BenSeverson/bisque/docs/superpowers/plans/2026-08-11-pcb-rev-b.md

# PCB Rev B Implementation Plan

> **For agentic workers:** REQUIRED SUB-SKILL: Use superpowers:subagent-driven-development (recommended) or superpowers:executing-plans to implement this plan task-by-task. Steps use checkbox (`- [ ]`) syntax for tracking.

**Goal:** Respin the Bisque controller PCB to add a touch interface, a re-mapped GPIO
assignment, an atmosphere purge relay, a second SSR zone, digital CT current sensing, a
second thermocouple input, and MAX31856 front-ends — plus opto-isolated SSR triggers, a
hardware watchdog, TVS protection and test points.

**Architecture:** Everything on the board derives from one table,
`hardware/kicad/generator/design.py` (components, pin→net connectivity, placement). The
schematic and board generators both read it, so they cannot disagree. Work proceeds
subsystem-by-subsystem into that table, each verified by the schematic netlist round-trip,
with a single integration task at the end that places, routes and DRCs the whole board.
Firmware changes are limited to pin symbols and the PSRAM mode — no drivers.

**Tech Stack:** KiCad 10 (`pcbnew` Python API + `kicad-cli`), Python 3 generator scripts,
ESP-IDF 6.0, JLCPCB Economic assembly.

## Global Constraints

- **Spec of record:** `docs/superpowers/specs/2026-08-10-pcb-rev-b-hardware-design.md`.
  Where this plan and the spec disagree, the spec wins — raise it rather than guessing.
- **Branch:** `pcb-rev-b-design` (already exists, already carries the spec).
- **Board:** 2-layer, 100 × 100 mm, `BX0,BY0,BX1,BY1 = 20.0, 20.0, 120.0, 120.0`.
- **Module:** ESP32-S3-WROOM-1U-N16R2, LCSC `C3013945`.
- **No mains anywhere on the PCB.** The ADE7953 voltage channel is DNP and lands on a
  SELV header only.
- **No TVS across thermocouple inputs** — leakage into a ~40 µV/°C source is an accuracy
  error, not protection.
- **All heat/relay outputs must be inactive from power-on through reset**: 10 kΩ pulldown
  on every SSR opto input and every ULN2003 input.
- **KiCad Python is not the system Python.** Board builds need:
  `KPY=/Applications/KiCad/KiCad.app/Contents/Frameworks/Python.framework/Versions/Current/bin/python3`
- **ESP-IDF is never on a bare shell's PATH.** Use `make firmware`, or
  `. ./scripts/idf-env.sh && idf.py ...` in the *same* command.
- **Rev A is a prototype.** No backward compatibility is owed to it by the board. The one
  exception is firmware OTA (spec §4.1), which is out of scope here.
- **Every LCSC part number must be re-verified live before the fab order.** The numbers in
  this plan were checked on 2026-08-10.

### Authoritative pinouts (extracted from KiCad 10 symbol libraries — do not re-derive)

```
MAX31856      Sensor_Temperature:MAX31856      TSSOP-14
  1 AGND   2 BIAS   3 T-     4 T+     5 AVDD   6 DNC    7 ~DRDY
  8 DVDD   9 ~CS   10 SCK   11 SDO   12 SDI   13 ~FAULT 14 DGND

ADE7953xCP    Sensor:ADE7953xCP                LFCSP-28 5x5 + EP
  1 ZX      2 ~RESET  3 VINTD   4 DGND    5 IAP     6 IAN     7 PULL_HIGH
  8 PULL_HIGH  9 IBP 10 IBN    11 VN     12 VP     13 REF    14 PULL_LOW
 15 VINTA  16 AGND   17 VDD    18 CLKIN  19 CLKOUT 20 ~REVP  21 ZX_I
 22 ~IRQ   23 CF1    24 CF2    25 SCLK   26 MISO/SDA/TX      27 MOSI/SCL/RX
 28 ~CS    29 EP

ULN2003A      Transistor_Array:ULN2003A        SOIC-16
  1..7 = I1..I7    8 GND    9 COM    10..16 = O7..O1   (note: O1 is pin 16)

SRV05-4       Power_Protection:SRV05-4         SOT-23-6
  1 IO1    2 VN(GND)   3 IO2    4 IO3    5 VP(VCC)   6 IO4

LTV-817       Isolator:LTV-817                 SO-4
  1 anode  2 cathode   3 emitter  4 collector      (symbol pins are unnamed)
```

### Net naming (use these exactly)

```
TC1_CS TC2_CS TC1_P TC1_N TC2_P TC2_N TC1_BIAS TC2_BIAS
SSR1_CTRL SSR2_CTRL SSR_EN SSR1_A SSR1_B SSR2_A SSR2_B
AUX1 AUX2 AUX3 AUX_VP AUX1_OUT AUX2_OUT AUX3_OUT
IN1_RAW IN1 IN2_RAW IN2 IN3_RAW IN3
I2C_SDA I2C_SCL
CTA_P CTA_N CTA_F CTB_P CTB_N CTB_F ADE_RESET ADE_VINTA ADE_VINTD ADE_REF
ADE_CLKIN ADE_CLKOUT ADE_VP ADE_VN
SSR1_LED_A SSR1_IND_A SSR1_IND_K SSR2_LED_A SSR2_IND_A SSR2_IND_K
T_CLK_R T_CS_R T_DIN_R T_DO_R T_IRQ_R
T_CS T_IRQ
WDT_KICK WDT_PUMP WDT_HOLD
```

`AUX_VP`, `SSR1_A/B`, `SSR2_A/B` and `SSR_EN` are **not** in `POWER_NETS` — `AUX_VP` is an
externally supplied rail the board does not generate, and the SSR nets are isolated.

---

## File Structure

| File | Responsibility | Tasks |
|---|---|---|
| `hardware/kicad/generator/design.py` | Single source of truth: components, pin→net, placement | 1, 3, 5–13 |
| `hardware/kicad/generator/check_pinmap.py` | **New.** Asserts `design.py` U1 pins match Kconfig defaults | 2 |
| `hardware/kicad/generator/check_isolation.py` | **New.** Asserts the opto barrier is unbridged | 7 |
| `hardware/kicad/generator/kicad_build.py` | Board build; gains a GND pour keepout | 7, 14 |
| `hardware/kicad/generator/gen_pcb.py` | Silkscreen header pin labels (`J5_PINS` etc.) | 11 |
| `hardware/kicad/generator/gen_jlc.py` | LCSC table, `HAND_SOLDER`, `JLC_ROTATION` | 1, 15 |
| `hardware/kicad/datasheets/REV-B-NOTES.md` | **New.** Verified answers to the spec's §7.1 risks | 4 |
| `main/Kconfig.projbuild` | Firmware pin defaults (source of truth for firmware) | 3 |
| `components/app_config/include/app_config.h` | `APP_PIN_*` macros | 3 |
| `sdkconfig.defaults` | PSRAM mode | 1 |
| `Makefile` | `pcb` / `pcb-check` targets | 15 |
| `docs/pin-assignments.md`, `docs/application-roadmap-and-pcb-provisions.md`, `hardware/kicad/README.md`, `docs/*.svg` | Documentation | 16 |

**Intermediate states carry dangling nets by design.** Task 3 re-maps U1's pins to nets
whose components do not exist until Tasks 6–13. `python3 generator/design.py` prints
`!! single-pin` for those, which is expected and not a failure until Task 14, where the
count must reach zero.

---

### Task 1: Module swap to WROOM-1U-N16R2

**Files:**
- Modify: `sdkconfig.defaults:11-14`
- Modify: `hardware/kicad/generator/design.py` (U1 entry, module docstring)
- Modify: `hardware/kicad/generator/gen_jlc.py` (LCSC["U1"])

**Interfaces:**
- Consumes: nothing.
- Produces: `U1` uses footprint `RF_Module:ESP32-S3-WROOM-1U`; GPIO 35/36/37 become
  assignable by Task 3.

- [ ] **Step 1: Change the PSRAM mode**

In `sdkconfig.defaults`, replace lines 11–14:

```
# PSRAM (ESP32-S3-WROOM-1U-N16R2: 2MB quad PSRAM)
# Quad, not octal: octal PSRAM consumes GPIO 35/36/37 inside the module, and
# docs/superpowers/specs/2026-08-10-pcb-rev-b-hardware-design.md needs them.
# The only consumer of PSRAM is CONFIG_MBEDTLS_EXTERNAL_MEM_ALLOC below, which
# needs tens of KB for OTA TLS, not megabytes.
CONFIG_SPIRAM=y
CONFIG_SPIRAM_MODE_QUAD=y
CONFIG_SPIRAM_SPEED_80M=y
```

- [ ] **Step 2: Verify the firmware still builds and PSRAM initialises**

```bash
make firmware
```

Expected: build succeeds. Confirm the config actually took:

```bash
grep -E "CONFIG_SPIRAM_MODE_(OCT|QUAD)" sdkconfig
```

Expected: `CONFIG_SPIRAM_MODE_QUAD=y` present, no `_OCT=y`. If `sdkconfig` still shows
OCT, delete `sdkconfig` and re-run `make firmware` — `sdkconfig.defaults` only seeds a
missing `sdkconfig`.

- [ ] **Step 3: Point U1 at the 1U footprint**

In `design.py`, change the `U1` entry's `fp`, `fpf` and `value` (leave `pins` alone —
Task 3 owns those):

```python
    "U1": dict(lib="RF_Module", sym="ESP32-S3-WROOM-1",
               fp="RF_Module:ESP32-S3-WROOM-1U", fpf="ESP32-S3-WROOM-1U.kicad_mod",
               value="ESP32-S3-WROOM-1U-N16R2", at=(70.0, 33.0, 0),
```

Note the symbol stays `ESP32-S3-WROOM-1` — the 1U has no separate symbol and the pin
numbering is identical. Only the footprint (body outline, origin, antenna keep-out)
differs.

- [ ] **Step 4: Update the BOM line**

In `gen_jlc.py`, replace the `U1` entry in `LCSC`:

```python
    "U1": ("C3013945", "ESP32-S3-WROOM-1U-N16R2 (16MB flash, 2MB quad PSRAM, U.FL)", False, True),
```

- [ ] **Step 5: Verify the netlist is unchanged**

```bash
cd hardware/kicad && python3 generator/design.py | tail -5
```

Expected: the same net list as before this task — the footprint swap changes geometry, not
connectivity.

- [ ] **Step 6: Commit**

```bash
git add sdkconfig.defaults hardware/kicad/generator/design.py hardware/kicad/generator/gen_jlc.py
git commit -m "feat(hw): swap to ESP32-S3-WROOM-1U-N16R2

Quad PSRAM frees GPIO 35/36/37; the U.FL connector makes Wi-Fi work in a
metal enclosure and removes the 48x21.7mm antenna keep-out."
```

---

### Task 2: `check_pinmap.py` — the Kconfig/board drift checker

Spec §7 asks for this explicitly: "assert `design.py`'s net-to-module-pin table matches
`main/Kconfig.projbuild` defaults. This has drifted before and is now checked rather than
remembered."

**Files:**
- Create: `hardware/kicad/generator/check_pinmap.py`

**Interfaces:**
- Consumes: `design.COMPONENTS["U1"]["pins"]`, `main/Kconfig.projbuild`.
- Produces: a CLI checker exiting 0 on agreement, 1 on drift. Tasks 3 and 14 run it.

- [ ] **Step 1: Write the checker**

Create `hardware/kicad/generator/check_pinmap.py`:

```python
#!/usr/bin/env python3
"""Assert design.py's U1 pin map agrees with main/Kconfig.projbuild defaults.

The GPIO assignment lives in three files that must agree and have drifted apart
before (see docs/pin-assignments.md). Kconfig is the firmware's source of truth;
design.py is the board's. This checks them against each other so a re-map that
updates one and forgets the other fails loudly instead of reaching a fab house.

Module pin number -> GPIO for ESP32-S3-WROOM-1 / -1U (identical pinout).
"""
import os
import re
import sys

sys.path.insert(0, os.path.dirname(__file__))
from design import COMPONENTS

REPO = os.path.normpath(os.path.join(os.path.dirname(__file__), "..", "..", ".."))
KCONFIG = os.path.join(REPO, "main", "Kconfig.projbuild")

# U1 module pin -> GPIO number. From the ESP32-S3-WROOM-1 datasheet pad list;
# the 1U is identical. Pins carrying power, EN or GND are absent.
# Nets on U1 that are fixed-function and correctly have NO Kconfig pin symbol:
# the native USB peripheral (GPIO 19/20), the UART0 console (GPIO 43/44) and
# the BOOT strapping pin (GPIO 0). These must never count as unmapped.
NO_KCONFIG_SYMBOL = {"USB_DN", "USB_DP", "TXD0", "RXD0", "IO0"}

MODULE_PIN_GPIO = {
    4: 4, 5: 5, 6: 6, 7: 7, 8: 15, 9: 16, 10: 17, 11: 18, 12: 8,
    13: 19, 14: 20, 15: 3, 16: 46, 17: 9, 18: 10, 19: 11, 20: 12,
    21: 13, 22: 14, 23: 21, 24: 47, 25: 48, 26: 45, 27: 0,
    28: 35, 29: 36, 30: 37, 31: 38, 32: 39, 33: 40, 34: 41, 35: 42,
    36: 44, 37: 43, 38: 2, 39: 1,
}

# net name -> Kconfig symbol that must hold that GPIO.
NET_KCONFIG = {
    "SPI_MOSI": "KILN_PIN_SPI_MOSI",
    "SPI_MISO": "KILN_PIN_SPI_MISO",
    "SPI_SCLK": "KILN_PIN_SPI_SCLK",
    "TC1_CS": "KILN_PIN_TC1_CS",
    "TC2_CS": "KILN_PIN_TC2_CS",
    "SSR1_CTRL": "KILN_PIN_SSR1",
    "SSR2_CTRL": "KILN_PIN_SSR2",
    "LCD_CS": "KILN_PIN_LCD_CS",
    "LCD_DC": "KILN_PIN_LCD_DC",
    "LCD_RST": "KILN_PIN_LCD_RST",
    "LCD_BL": "KILN_PIN_LCD_BL",
    "LED_DATA": "KILN_PIN_STATUS_LED",
    "ALARM": "KILN_PIN_ALARM",
    "AUX1": "KILN_PIN_VENT",
    "AUX2": "KILN_PIN_AUX2",
    "AUX3": "KILN_PIN_AUX3",
    "IN1": "KILN_PIN_LID_SWITCH",
    "IN2": "KILN_PIN_IN_GASFLOW",
    "IN3": "KILN_PIN_IN_SPARE",
    "I2C_SDA": "KILN_PIN_I2C_SDA",
    "I2C_SCL": "KILN_PIN_I2C_SCL",
    "T_CS": "KILN_PIN_TOUCH_CS",
    "T_IRQ": "KILN_PIN_TOUCH_IRQ",
    "WDT_KICK": "KILN_PIN_WDT_KICK",
    "BTN_UP": "KILN_PIN_BTN_UP",
    "BTN_DOWN": "KILN_PIN_BTN_DOWN",
    "BTN_LEFT": "KILN_PIN_BTN_LEFT",
    "BTN_RIGHT": "KILN_PIN_BTN_RIGHT",
    "BTN_SEL": "KILN_PIN_BTN_SELECT",
}

def kconfig_defaults(path):
    """{symbol: int default} for every `config X` / `default N` int option."""
    out, sym = {}, None
    for line in open(path):
        m = re.match(r"\s*config\s+(\w+)\s*$", line)
        if m:
            sym = m.group(1)
            continue
        m = re.match(r"\s*default\s+(-?\d+)\s*$", line)
        if m and sym:
            out.setdefault(sym, int(m.group(1)))
    return out

def board_gpios():
    """{net: gpio} for every U1 pin that carries a mapped signal."""
    out = {}
    for pin, net in COMPONENTS["U1"]["pins"].items():
        if net is None:
            continue
        gpio = MODULE_PIN_GPIO.get(int(pin))
        if gpio is not None:
            out[net] = gpio
    return out

def main():
    defaults = kconfig_defaults(KCONFIG)
    board = board_gpios()
    errors = []

    for net, sym in NET_KCONFIG.items():
        on_board = board.get(net)
        in_kconfig = defaults.get(sym)
        if on_board is None:
            errors.append("net %s is in NET_KCONFIG but not on U1 in design.py" % net)
        elif in_kconfig is None:
            errors.append("%s has no integer default in Kconfig.projbuild" % sym)
        elif on_board != in_kconfig:
            errors.append("%s: Kconfig says GPIO %d, design.py wires net %s to GPIO %d"
                          % (sym, in_kconfig, net, on_board))

    unmapped = sorted(set(board) - set(NET_KCONFIG) - NO_KCONFIG_SYMBOL)
    if unmapped:
        errors.append("U1 nets with no Kconfig symbol: %s" % ", ".join(unmapped))

    if errors:
        for e in errors:
            print("FAIL: %s" % e)
        return 1
    print("check_pinmap: %d GPIO assignments agree between Kconfig and design.py"
          % len(NET_KCONFIG))
    return 0

if __name__ == "__main__":
    sys.exit(main())
```

- [ ] **Step 2: Run it and confirm it fails on the current (rev A) state**

```bash
cd hardware/kicad && python3 generator/check_pinmap.py
```

Expected: **exit 1**, with failures naming `TC1_CS`, `SSR1_CTRL`, `AUX2`, `IN1`, and the
symbols that do not exist yet (`KILN_PIN_TC2_CS`, `KILN_PIN_I2C_SDA`, …). This is correct:
the checker encodes the rev B target, and rev B has not been built yet. It proves the
checker can detect drift rather than passing vacuously.

Also confirm it detects real board nets: the `unmapped` line should list rev A's
`TC_CS`, `SSR_CTRL`, `VENT`, `AUX_A`, `AUX_B`, `LID_SW`.

- [ ] **Step 3: Commit**

```bash
git add hardware/kicad/generator/check_pinmap.py
git commit -m "test(hw): add Kconfig/design.py GPIO drift checker

Fails against rev A by design - it encodes the rev B target map. Task 3
brings both files to it."
```

---

### Task 3: GPIO re-map — Kconfig, app_config.h and design.py together

These three must change atomically or `check_pinmap.py` stays red.

**Files:**
- Modify: `main/Kconfig.projbuild`
- Modify: `components/app_config/include/app_config.h`
- Modify: `hardware/kicad/generator/design.py` (U1 `pins` dict only)

**Interfaces:**
- Consumes: `check_pinmap.py` from Task 2.
- Produces: every net in the plan's naming list is wired to U1; Tasks 6–13 attach the
  other end of each.

- [ ] **Step 1: Rewrite U1's pin dict in `design.py`**

```python
               pins={"1": "GND", "2": "+3V3", "3": "EN", "4": "IN1",
                     "5": "T_CS", "6": "T_IRQ", "7": "ALARM",
                     "8": "AUX2", "9": "AUX3", "10": "SSR1_CTRL",
                     "11": "I2C_SDA", "12": "LCD_CS", "13": "USB_DN",
                     "14": "USB_DP", "15": "LCD_BL", "16": "LCD_RST",
                     "17": "LCD_DC", "18": "TC1_CS", "19": "SPI_MOSI",
                     "20": "SPI_SCLK", "21": "SPI_MISO", "22": "AUX1",
                     "23": "SSR2_CTRL", "24": "I2C_SCL", "25": "LED_DATA",
                     "26": None, "27": "IO0", "28": "TC2_CS",
                     "29": "WDT_KICK", "30": None, "31": "BTN_UP",
                     "32": "BTN_DOWN", "33": "BTN_LEFT", "34": "BTN_RIGHT",
                     "35": "BTN_SEL", "36": "RXD0", "37": "TXD0",
                     "38": "IN2", "39": "IN3", "40": "GND",
                     "41": "GND"}),
```

Module pin 30 is GPIO 37 — the spare — and stays `None`.

- [ ] **Step 2: Update Kconfig defaults**

In `main/Kconfig.projbuild`, inside `menu "GPIO Pin Assignments"`:

Rename `KILN_PIN_TC_CS` → `KILN_PIN_TC1_CS` (default stays `10`) and `KILN_PIN_SSR` →
`KILN_PIN_SSR1` (default stays `17`). Change the five button defaults to
`UP=38 DOWN=39 LEFT=40 RIGHT=41 SELECT=42`. Change `KILN_PIN_LID_SWITCH` default `21` →
`4`. Rename `KILN_PIN_AUX_A` → `KILN_PIN_AUX2` (default `-1` → `15`) and `KILN_PIN_AUX_B`
→ `KILN_PIN_AUX3` (default `-1` → `16`).

Then append these new options:

```
        config KILN_PIN_TC2_CS
            int "Thermocouple 2 CS GPIO (-1 = disabled)"
            default 35
            help
                Chip select for the second (load) MAX31856 on the shared SPI
                bus. Populated on the rev B board.

                NOTHING READS THIS PIN YET. The multi-channel thermocouple
                driver is a follow-on; this exists so the board and the
                firmware agree on what is routed.

                Set to -1 on any build with only one thermocouple fitted.

        config KILN_PIN_SSR2
            int "SSR zone 2 output GPIO (-1 = disabled)"
            default 21
            help
                Trigger for the second SSR zone, opto-isolated on the rev B
                board. Driven from the 100 ms SSR window rather than the 1 Hz
                firing tick, because zone 2 modulates simultaneously with
                zone 1.

                NOTHING DRIVES THIS PIN YET. Set to -1 on a single-zone kiln.

        config KILN_PIN_IN_GASFLOW
            int "Gas-flow interlock input GPIO (-1 = disabled)"
            default 2
            help
                Dry-contact input for a gas-flow switch on the atmosphere
                purge line. Same conditioning and fail-safe polarity as the
                lid switch: open contact reads HIGH, so a broken wire reads
                "no flow".

                NOTHING READS THIS PIN YET.

        config KILN_PIN_IN_SPARE
            int "Spare protected input GPIO (-1 = disabled)"
            default 1
            help
                Third dry-contact input, unassigned. Same conditioning as the
                lid and gas-flow inputs.

                NOTHING READS THIS PIN YET.

        config KILN_PIN_I2C_SDA
            int "I2C SDA GPIO (-1 = disabled)"
            default 18
            help
                I2C data. Carries the on-board ADE7953 current-metering IC and
                the Qwiic/STEMMA-QT expansion header.

                NO I2C DRIVER EXISTS YET.

        config KILN_PIN_I2C_SCL
            int "I2C SCL GPIO (-1 = disabled)"
            default 47
            help
                I2C clock. See KILN_PIN_I2C_SDA.

        config KILN_PIN_TOUCH_CS
            int "Touch controller CS GPIO (-1 = disabled)"
            default 5
            help
                Chip select for the XPT2046 resistive touch controller on the
                display module. The controller is on the LCD module, not on
                the Bisque PCB; its clock/data lines are the shared SPI bus.

                NO TOUCH DRIVER EXISTS YET.

        config KILN_PIN_TOUCH_IRQ
            int "Touch pen-down interrupt GPIO (-1 = disabled)"
            default 6
            help
                Pen-down interrupt from the XPT2046. Lets the firmware skip
                touch reads until a press occurs rather than polling.

                Set to -1 to poll instead.

        config KILN_PIN_WDT_KICK
            int "Hardware watchdog kick GPIO (-1 = disabled)"
            default 36
            help
                Square-wave output feeding the charge pump that gates both SSR
                opto channels. If the firmware stops toggling this pin - or
                wedges with it stuck high or stuck low - the pump decays and
                both SSRs de-energize within about a second.

                A charge pump needs TRANSITIONS, which is the whole point: a
                stuck level fails exactly like a stopped one.

                NOTHING TOGGLES THIS PIN YET, so a rev B board runs with the
                WDT DEFEAT solder jumper fitted until the kick task lands. A
                board with neither the jumper nor the kick task will not heat.

                Set to -1 on hardware without the watchdog circuit.
```

- [ ] **Step 3: Update `app_config.h`**

Replace the `MAX31855 Thermocouple`, `SSR Output` and `Optional GPIOs` blocks:

```c
/* --- MAX31856 Thermocouple (2 channels on the shared SPI bus) --- */
#define APP_PIN_TC1_CS CONFIG_KILN_PIN_TC1_CS
#define APP_PIN_TC2_CS CONFIG_KILN_PIN_TC2_CS

/* --- SSR Outputs (opto-isolated, 2 zones) --- */
#define APP_PIN_SSR1 CONFIG_KILN_PIN_SSR1
#define APP_PIN_SSR2 CONFIG_KILN_PIN_SSR2
```

and, in the optional-GPIO block, replace `APP_PIN_AUX_A` / `APP_PIN_AUX_B` and add the
rest:

```c
/* Aux output bank (ULN2003 channels 1-3). Routed and populated on the rev B
   PCB but NOT DRIVEN BY ANY CODE except AUX1, which components/safety/ drives
   as the vent. Roles are firmware policy, not wiring — see
   docs/pin-assignments.md §5. */
#define APP_PIN_AUX2 CONFIG_KILN_PIN_AUX2
#define APP_PIN_AUX3 CONFIG_KILN_PIN_AUX3

/* Protected dry-contact inputs. IN1 is the lid switch (APP_PIN_LID_SWITCH). */
#define APP_PIN_IN_GASFLOW CONFIG_KILN_PIN_IN_GASFLOW
#define APP_PIN_IN_SPARE   CONFIG_KILN_PIN_IN_SPARE

/* I2C bus: on-board ADE7953 current metering + Qwiic expansion header. */
#define APP_PIN_I2C_SDA CONFIG_KILN_PIN_I2C_SDA
#define APP_PIN_I2C_SCL CONFIG_KILN_PIN_I2C_SCL

/* XPT2046 touch controller (on the display module, shared SPI bus). */
#define APP_PIN_TOUCH_CS  CONFIG_KILN_PIN_TOUCH_CS
#define APP_PIN_TOUCH_IRQ CONFIG_KILN_PIN_TOUCH_IRQ

/* Hardware watchdog kick — gates both SSR opto channels. */
#define APP_PIN_WDT_KICK CONFIG_KILN_PIN_WDT_KICK
```

Update the `APP_PIN_TC_CS` / `APP_PIN_SSR` call sites the compiler flags in the next step.

- [ ] **Step 4: Fix the renamed call sites and build**

```bash
grep -rn "APP_PIN_TC_CS\|APP_PIN_SSR\b\|CONFIG_KILN_PIN_TC_CS\|CONFIG_KILN_PIN_SSR\b\|APP_PIN_AUX_A\|APP_PIN_AUX_B" main/ components/ simulator/ tests/
```

Rename each hit to the new symbol (`APP_PIN_TC1_CS`, `APP_PIN_SSR1`, `APP_PIN_AUX2/3`).
Then:

```bash
make firmware && make test-host
```

Expected: both succeed.

- [ ] **Step 5: Run the drift checker — it must now pass**

```bash
cd hardware/kicad && python3 generator/check_pinmap.py
```

Expected: `check_pinmap: 29 GPIO assignments agree between Kconfig and design.py`, exit 0.

- [ ] **Step 6: Regenerate the schematic and confirm the round-trip still passes**

```bash
cd hardware/kicad && python3 generator/gen_sch.py bisque-controller.kicad_sch \
  && python3 generator/check_netlist.py bisque-controller.kicad_sch
```

Expected: `PASS`, 0 mismatches. The single-pin warnings from `design.py` are expected
here (see File Structure).

- [ ] **Step 7: Commit**

```bash
git add main/Kconfig.projbuild components/app_config/include/app_config.h \
        hardware/kicad/generator/design.py hardware/kicad/bisque-controller.kicad_sch \
        main components
git commit -m "feat(hw)!: re-map GPIOs for rev B

Buttons to 38-42 (contiguous module pads), lid to GPIO 4, SSR2 onto 21,
TC2/watchdog onto the pins quad PSRAM freed. check_pinmap.py now passes."
```

---

### Task 4: Retire the spec's pre-layout risks

Spec §7.1 lists six risks that must be answered from datasheets before copper is
committed. Three were already retired during design review (KK-254 1×14 exists; MAX31856
and ADE7953 pinouts are in the Global Constraints above). This task closes the rest.

**Files:**
- Create: `hardware/kicad/datasheets/REV-B-NOTES.md`

**Interfaces:**
- Consumes: nothing.
- Produces: the ADE7953 footprint choice and the confirmed part numbers that Tasks 7–12
  depend on. **Tasks 8, 10 and 12 must not start before this one lands.**

- [ ] **Step 1: Pull the datasheets**

Use the `kicad-happy:datasheets` skill, or fetch directly:

```bash
cd hardware/kicad && python3 ~/.claude/plugins/cache/kicad-happy/kicad-happy/2.1.0/skills/lcsc/scripts/fetch_datasheet_lcsc.py --search "C515890" -o datasheets/ADE7953.pdf
python3 ~/.claude/plugins/cache/kicad-happy/kicad-happy/2.1.0/skills/lcsc/scripts/fetch_datasheet_lcsc.py --search "C2653162" -o datasheets/MAX31856.pdf
python3 ~/.claude/plugins/cache/kicad-happy/kicad-happy/2.1.0/skills/lcsc/scripts/fetch_datasheet_lcsc.py --search "C7512" -o datasheets/ULN2003A.pdf
python3 ~/.claude/plugins/cache/kicad-happy/kicad-happy/2.1.0/skills/lcsc/scripts/fetch_datasheet_lcsc.py --search "C109227" -o datasheets/LTV-817S.pdf
```

- [ ] **Step 2: Answer each question and write it down**

Create `hardware/kicad/datasheets/REV-B-NOTES.md` recording, with a page or table citation
for each:

1. **ADE7953 `IRMS` with the voltage channel unused.** Does the current-channel RMS
   register update independently of the voltage channel? Which registers are invalid
   without it (expect: active/reactive power, power factor, line-cycle accumulation,
   `ZX`)? **If IRMS turns out to require the voltage channel, STOP and escalate** — spec
   §2.2's whole current-only premise fails and the CT section needs redesigning.
2. **ADE7953 exposed-pad size.** KiCad ships no LFCSP-28 footprint (only LFCSP-32).
   Confirm the package's EP dimensions against
   `Package_DFN_QFN:QFN-28-1EP_5x5mm_P0.5mm_EP3.1x3.1mm` and
   `Package_DFN_QFN:VQFN-28-1EP_5x5mm_P0.5mm_EP3.25x3.25mm`, and record which one to use.
   These pads are 0.5 mm pitch — a wrong EP is not something DRC can catch.
3. **ADE7953 interface selection.** How I2C mode is strapped (pins 7/8 `PULL_HIGH`, 14
   `PULL_LOW`, and what `~CS` pin 28 must do), plus the I2C address and any address-select
   pins. Record the required resistor values.
4. **ADE7953 support components.** Required capacitor values on `VINTA` (15), `VINTD` (3),
   `REF` (13), the `CLKIN`/`CLKOUT` crystal load caps, and the `~RESET` (2) arrangement.
5. **MAX31856 `BIAS` pin (2) and split AVDD/DVDD.** The capacitor `BIAS` needs to AGND, and
   whether AVDD (5) and DVDD (8) may share the 3V3 rail (expect yes, with separate
   decoupling). Record the datasheet's recommended thermocouple input filter — series R,
   differential C, common-mode C.
6. **ULN2003 input threshold with a floating driver.** Confirm a 10 kΩ pulldown holds every
   channel off while the ESP32 pin is high-impedance at boot.
7. **LTV-817S-TA1-C footprint match.** Which of `Package_SO:SO-4_4.4x2.3mm_P1.27mm`,
   `SO-4_4.4x3.6mm_P2.54mm`, `SO-4_4.4x3.9mm_P2.54mm`, `SO-4_4.4x4.3mm_P2.54mm` matches
   the LCSC part's drawing. Record CTR at the chosen drive current and the resulting
   guaranteed output current.
8. **Charge-pump Schottky.** Confirm a suitable dual Schottky at LCSC (BAT54S or
   equivalent), its LCSC number, and whether it is Basic. Record `Vf` — the pump must hold
   the AO3400A gate above its worst-case `Vgs(th)` (see Task 12).
9. **U.FL clearance.** Connector height above the module and the pigtail's exit direction,
   so Task 14 can keep the reclaimed antenna band clear of it.

- [ ] **Step 3: Confirm every LCSC part is still in stock**

```bash
cd /tmp && for p in C3013945 C2653162 C515890 C7471632 C7512 C109227 C558418; do
  printf "%-10s " $p
  curl -s "https://jlcsearch.tscircuit.com/api/search?q=$p&limit=1&full=true" \
   | python3 -c "import json,sys;d=json.load(sys.stdin)['components'];print(d[0]['mfr'],d[0]['stock'],d[0]['price']) if d else print('NOT FOUND')"
  sleep 0.4
done
```

Expected: all seven resolve with non-zero stock. Record the figures and the date in
`REV-B-NOTES.md`; note any that have moved since 2026-08-10.

- [ ] **Step 4: Commit**

```bash
git add hardware/kicad/datasheets/
git commit -m "docs(hw): retire the rev B pre-layout datasheet risks

Answers spec 7.1 from the datasheets: ADE7953 current-only IRMS, its
exposed-pad size (KiCad has no LFCSP-28), I2C strapping, MAX31856 BIAS
and split supplies, ULN2003 boot state, opto footprint, pump Schottky."
```

---

### Task 5: Board outline and placement regions

**Files:**
- Modify: `hardware/kicad/generator/design.py` (outline constants, mounting holes,
  `POWER_NETS`, module docstring)

**Interfaces:**
- Consumes: Task 1.
- Produces: `BX0..BY1 = 20,20,120,120`; the region comment block Tasks 6–13 place against.

- [ ] **Step 1: Grow the board and move the mounting holes**

In `design.py`:

```python
# --- board outline (mm, page coords) ---
BX0, BY0, BX1, BY1 = 20.0, 20.0, 120.0, 120.0   # 100 x 100 mm

# Placement regions (docs/.../2026-08-10-pcb-rev-b-hardware-design.md §6.2).
# The quiet analog region holds both thermocouple cold junctions and the CT
# front-end; keep it away from the ULN2003 and the SSR optos.
#   digital   x 20..120  y 20..48   module, USB-C, reclaimed antenna band
#   switching x 20..60   y 50..92   ULN2003, SSR optos, watchdog, buzzer
#   analog    x 92..120  y 50..92   MAX31856 x2, ADE7953, CT front-end
#   headers   x 20..120  y 94..120  LCD / nav / aux / I2C, screw terminals
#   barrier   x 20..60   y 74..92   GND pour keepout across the opto row

# net name -> netclass ("signal" default).
# AUX_VP is an externally supplied coil rail the board does not generate, and
# the SSR_* nets are on the isolated side of the opto barrier — neither may
# join the GND/power pour logic.
POWER_NETS = {"GND", "+5V", "+3V3", "VBUS", "VIN", "VLED"}
```

Move the four mounting holes to a 90 × 90 mm grid: `H1` `(25.5, 25.0)`, `H2`
`(115.5, 25.0)`, `H3` `(25.5, 115.0)`, `H4` `(115.5, 115.0)`.

- [ ] **Step 2: Move the bottom-edge parts down 20 mm**

Everything that was referenced to the old 100 mm bottom edge moves with it. Add 20.0 to
the Y of: `J5` `(31.0, 115.0)`, `J6` `(53.0, 115.0)`, `J7` `(70.5, 115.0)`, `C11`
`(26.5, 110.5)`, `J1` `(96.0, 115.6)`, `R5` `(103.5, 117.9)`, `D2` `(102.5, 106.0)`, `U4`
`(96.0, 102.0)`, `R4` `(91.0, 108.0)`, `LED1` `(75.0, 106.0)`, `R3` `(82.0, 104.35)`,
`D3` `(72.55, 99.5)`, `C10` `(69.0, 101.5)`, `R12` `(87.3, 107.6)`, `R13` `(83.5, 101.5)`,
`C12` `(83.8, 107.6)`, `BZ1` `(38.0, 98.0)`, `D4` `(49.5, 104.0)`, `Q2` `(58.0, 100.0)`,
`R11` `(58.8, 94.0)`, `R8` `(62.0, 97.5)`.

These are initial placements. Task 14 iterates them against DRC — do not treat them as
final.

- [ ] **Step 3: Verify connectivity is untouched**

```bash
cd hardware/kicad && python3 generator/design.py > /tmp/nets-after.txt && wc -l /tmp/nets-after.txt
```

Expected: the same net count as before this task — moving parts changes no connectivity.

- [ ] **Step 4: Commit**

```bash
git add hardware/kicad/generator/design.py
git commit -m "feat(hw): grow rev B board to 100x100mm with placement regions"
```

---

### Task 6: Thermocouple front-ends — 2 × MAX31856

**Files:**
- Modify: `hardware/kicad/generator/design.py`

**Interfaces:**
- Consumes: Task 4's `REV-B-NOTES.md` (BIAS cap value, input filter values), Task 3's
  `TC1_CS` / `TC2_CS` nets.
- Produces: nets `TC1_P TC1_N TC2_P TC2_N TC1_BIAS TC2_BIAS`; designators `U3` (TC1),
  `U5` (TC2), `J3` (TC1 terminal), `J8` (TC2 terminal).

- [ ] **Step 1: Replace U3 and add U5**

Delete the old `U3` (MAX31855) entry and its `C8`/`C9`, and add. Use the filter values
recorded in `REV-B-NOTES.md` — the ones below are the datasheet's typical application and
must be confirmed against it:

```python
    # --- Thermocouple channel 1 (control TC) -----------------------------
    # MAX31856 pinout from Sensor_Temperature:MAX31856. Note AVDD (5) and
    # DVDD (8) are separate supply pins - both 3V3, each decoupled - and BIAS
    # (2) needs its own capacitor to AGND. DRDY (7) and FAULT (13) are left
    # unconnected on purpose: both are readable from registers, and polling
    # them saves four GPIOs the pin budget does not have.
    "U3": dict(lib="Sensor_Temperature", sym="MAX31856",
               fp="Package_SO:TSSOP-14_4.4x5mm_P0.65mm",
               fpf="TSSOP-14_4.4x5mm_P0.65mm.kicad_mod",
               value="MAX31856MUD+", at=(104.0, 56.0, 90),
               pins={"1": "GND", "2": "TC1_BIAS", "3": "TC1_N", "4": "TC1_P",
                     "5": "+3V3", "6": None, "7": None, "8": "+3V3",
                     "9": "TC1_CS", "10": "SPI_SCLK", "11": "SPI_MISO",
                     "12": "SPI_MOSI", "13": None, "14": "GND"}),
    "C8": dict(lib="Device", sym="C", fp=C0805[0], fpf=C0805[1],
               value="100nF", at=(100.0, 53.0, 90),
               pins={"1": "+3V3", "2": "GND"}),
    "C13": dict(lib="Device", sym="C", fp=C0805[0], fpf=C0805[1],
                value="100nF", at=(100.0, 59.0, 90),
                pins={"1": "+3V3", "2": "GND"}),
    "C14": dict(lib="Device", sym="C", fp=C0805[0], fpf=C0805[1],
                value="100nF", at=(108.0, 52.0, 0),
                pins={"1": "TC1_BIAS", "2": "GND"}),
    # Differential + common-mode input filter. No TVS here: a TVS array's
    # leakage into a ~40uV/degC source is an accuracy error, not protection.
    "C9": dict(lib="Device", sym="C", fp=C0805[0], fpf=C0805[1],
               value="10nF", at=(110.0, 56.0, 0),
               pins={"1": "TC1_P", "2": "TC1_N"}),
    "C15": dict(lib="Device", sym="C", fp=C0805[0], fpf=C0805[1],
                value="100pF", at=(110.0, 53.5, 0),
                pins={"1": "TC1_P", "2": "GND"}),
    "C16": dict(lib="Device", sym="C", fp=C0805[0], fpf=C0805[1],
                value="100pF", at=(110.0, 58.5, 0),
                pins={"1": "TC1_N", "2": "GND"}),
    "J3": dict(lib="Connector", sym="Screw_Terminal_01x02",
               fp=TBLOCK[0], fpf=TBLOCK[1], value="TC1_K", at=(116.0, 56.0, 90),
               pins={"1": "TC1_P", "2": "TC1_N"}),
```

- [ ] **Step 2: Add channel 2 as an exact copy**

Repeat the block above as `U5`, `C17`–`C22`, `J8`, substituting `TC2_*` for `TC1_*` and
`TC2_CS` for `TC1_CS`, placed 14 mm south: `U5` at `(104.0, 70.0, 90)`, `C17` `(100.0,
67.0, 90)`, `C18` `(100.0, 73.0, 90)`, `C19` `(108.0, 66.0, 0)`, `C20` `(110.0, 70.0, 0)`,
`C21` `(110.0, 67.5, 0)`, `C22` `(110.0, 72.5, 0)`, `J8` `(116.0, 70.0, 90)`.

Note `TC1_N`/`TC2_N` go to the terminal, **not** to GND — unlike rev A's MAX31855, whose
T− was grounded at the chip. Both MAX31856 channels reference their own differential pair.
Record in the README (Task 16) that **ungrounded-junction probes are required**: both
chips share board ground, so two grounded-junction probes in one chamber form a loop
through the kiln body.

- [ ] **Step 3: Verify**

```bash
cd hardware/kicad && python3 generator/design.py | grep -E "TC1_|TC2_"
```

Expected: `TC1_P`, `TC1_N`, `TC2_P`, `TC2_N`, `TC1_BIAS`, `TC2_BIAS`, `TC1_CS`, `TC2_CS`
each with ≥2 pins and **no** `!! single-pin` marker.

```bash
python3 generator/gen_sch.py bisque-controller.kicad_sch && python3 generator/check_netlist.py bisque-controller.kicad_sch
```

Expected: `PASS`.

- [ ] **Step 4: Commit**

```bash
git add hardware/kicad/generator/design.py hardware/kicad/bisque-controller.kicad_sch
git commit -m "feat(hw): two MAX31856 thermocouple front-ends

Replaces the MAX31855. Separate AVDD/DVDD decoupling and the BIAS cap per
datasheet; DRDY and FAULT left NC and polled from registers to save four
GPIOs. Ungrounded-junction probes now required."
```

---

### Task 7: Opto-isolated SSR channels, the pour keepout, and `check_isolation.py`

**Files:**
- Modify: `hardware/kicad/generator/design.py`
- Modify: `hardware/kicad/generator/kicad_build.py` (`add_zones`)
- Create: `hardware/kicad/generator/check_isolation.py`

**Interfaces:**
- Consumes: Task 4 (`LTV-817S` footprint choice, CTR), Task 3 (`SSR1_CTRL`, `SSR2_CTRL`).
- Produces: net `SSR_EN` — the shared opto-LED cathode node that Task 12's watchdog
  MOSFET gates. **Task 12 depends on this net existing.**

- [ ] **Step 1: Write the isolation checker first**

Create `hardware/kicad/generator/check_isolation.py`:

```python
#!/usr/bin/env python3
"""Assert the SSR opto-isolation barrier is not bridged.

The board pours GND on both layers. An opto buys nothing if the pour runs
underneath it, so kicad_build.py carves a keepout across the opto row and the
isolated nets must touch nothing but their opto and their terminal.

Runs on design.py connectivity alone - no KiCad required.
"""
import os
import sys

sys.path.insert(0, os.path.dirname(__file__))
from design import netlist

# isolated net -> exactly the (ref, pin) endpoints it may have.
ISOLATED = {
    "SSR1_A": {("U8", "4"), ("J4", "1")},
    "SSR1_B": {("U8", "3"), ("J4", "2")},
    "SSR2_A": {("U9", "4"), ("J9", "1")},
    "SSR2_B": {("U9", "3"), ("J9", "2")},
}

# Nets that must never appear on the isolated side.
FORBIDDEN = {"GND", "+3V3", "+5V", "VBUS", "VIN", "VLED", "AUX_VP"}

def main():
    nets = netlist()
    errors = []
    for net, allowed in ISOLATED.items():
        got = set(nets.get(net, []))
        if not got:
            errors.append("isolated net %s does not exist" % net)
        elif got != allowed:
            errors.append("isolated net %s connects to %s; expected exactly %s"
                          % (net, sorted(got), sorted(allowed)))
    isolated_refs = {ref for allowed in ISOLATED.values() for ref, _ in allowed}
    for bad in FORBIDDEN:
        for ref, pin in nets.get(bad, []):
            if ref in isolated_refs and (ref, pin) not in \
                    {e for a in ISOLATED.values() for e in a}:
                errors.append("%s.%s is on %s but %s straddles the barrier"
                              % (ref, pin, bad, ref))
    if errors:
        for e in errors:
            print("FAIL: %s" % e)
        return 1
    print("check_isolation: %d isolated nets, barrier intact" % len(ISOLATED))
    return 0

if __name__ == "__main__":
    sys.exit(main())
```

- [ ] **Step 2: Run it and confirm it fails**

```bash
cd hardware/kicad && python3 generator/check_isolation.py
```

Expected: **exit 1**, "isolated net SSR1_A does not exist" ×4. The optos do not exist yet.

- [ ] **Step 3: Replace the discrete SSR driver with two opto channels**

Delete rev A's `R6`, `R7`, `Q1`, `LED3`, `R10` and re-point `J4`. Add:

```python
    # --- SSR channel 1 (opto-isolated) -----------------------------------
    # GPIO -> R -> opto LED -> SSR_EN, with the indicator LED as a parallel
    # branch off the same GPIO. The indicator cannot sit in SERIES with the
    # opto LED: ~2.0V (indicator) + ~1.2V (opto) leaves nothing to drop from a
    # 3.3V GPIO. Both cathodes land on SSR_EN so the watchdog (Task 12) gates
    # the indicator too - an LED that lights while the SSR is cut would lie.
    # R7/R14 hold the LEDs dark through boot and reset.
    "U8": dict(lib="Isolator", sym="LTV-817",
               fp="Package_SO:SO-4_4.4x4.3mm_P2.54mm",
               fpf="SO-4_4.4x4.3mm_P2.54mm.kicad_mod",
               value="LTV-817S", at=(30.0, 78.0, 0),
               pins={"1": "SSR1_LED_A", "2": "SSR_EN",
                     "3": "SSR1_B", "4": "SSR1_A"}),
    "R6": dict(lib="Device", sym="R", fp=R0805[0], fpf=R0805[1],
               value="220R", at=(36.0, 78.0, 180),
               pins={"1": "SSR1_CTRL", "2": "SSR1_LED_A"}),
    "R7": dict(lib="Device", sym="R", fp=R0805[0], fpf=R0805[1],
               value="10k", at=(40.0, 76.0, 90),
               pins={"1": "SSR1_CTRL", "2": "GND"}),
    "LED3": dict(lib="Device", sym="LED", fp=LED0805[0], fpf=LED0805[1],
                 value="amber", at=(24.5, 74.0, 270),
                 pins={"1": "SSR1_IND_K", "2": "SSR1_IND_A"}),
    "R10": dict(lib="Device", sym="R", fp=R0805[0], fpf=R0805[1],
                value="680R", at=(28.0, 74.0, 90),
                pins={"1": "SSR1_CTRL", "2": "SSR1_IND_A"}),
    "R15": dict(lib="Device", sym="R", fp=R0805[0], fpf=R0805[1],
                value="0R", at=(24.5, 71.0, 0),
                pins={"1": "SSR1_IND_K", "2": "SSR_EN"}),
    "J4": dict(lib="Connector", sym="Screw_Terminal_01x02",
               fp=TBLOCK[0], fpf=TBLOCK[1], value="SSR1", at=(22.5, 82.0, 270),
               pins={"1": "SSR1_A", "2": "SSR1_B"}),
```

Repeat as channel 2 — `U9`, `R16` (220R), `R17` (10k), `LED4` (amber), `R18` (680R),
`R19` (0R), `J9` — substituting `SSR2_*`, placed 8 mm south: `U9` `(30.0, 86.0, 0)`,
`R16` `(36.0, 86.0, 180)`, `R17` `(40.0, 84.0, 90)`, `LED4` `(24.5, 90.0, 270)`, `R18`
`(28.0, 90.0, 90)`, `R19` `(24.5, 93.0, 0)`, `J9` `(22.5, 90.0, 270)`.

The 220 Ω series value assumes ~10 mA into the LED from 3.3 V; confirm against the CTR
recorded in `REV-B-NOTES.md` that the resulting collector current clears the SSR input's
requirement.

- [ ] **Step 4: Carve the GND keepout in `kicad_build.py`**

In `add_zones()`, after the two GND zones are added, append a rule area over the barrier
band. `_gnd_islands()` already skips `z.GetIsRuleArea()`, so the healing logic ignores it:

```python
    # Opto-isolation barrier: no GND copper on either layer across the SSR
    # opto row, or the pour shorts around the barrier the optos exist to make.
    # A rule area (not a zone) - _gnd_islands() skips these by design.
    ka = pcbnew.ZONE(board)
    ka.SetIsRuleArea(True)
    ka.SetDoNotAllowZoneFills(True)
    ka.SetDoNotAllowTracks(False)
    ka.SetDoNotAllowVias(True)
    ka.SetLayerSet(pcbnew.LSET(
        [pcbnew.F_Cu, pcbnew.B_Cu]))
    ol = ka.Outline()
    ol.NewOutline()
    for (x, y) in [(20.5, 70.0), (34.0, 70.0), (34.0, 96.0), (20.5, 96.0)]:
        ol.Append(MM(x), MM(y))
    board.Add(ka)
```

- [ ] **Step 5: Verify both checkers**

```bash
cd hardware/kicad && python3 generator/check_isolation.py
```

Expected: `check_isolation: 4 isolated nets, barrier intact`, exit 0.

```bash
python3 generator/gen_sch.py bisque-controller.kicad_sch && python3 generator/check_netlist.py bisque-controller.kicad_sch
```

Expected: `PASS`.

- [ ] **Step 6: Commit**

```bash
git add hardware/kicad/generator/design.py hardware/kicad/generator/kicad_build.py \
        hardware/kicad/generator/check_isolation.py hardware/kicad/bisque-controller.kicad_sch
git commit -m "feat(hw): opto-isolate both SSR channels

LTV-817S per channel, indicator LED as a parallel branch (series would not
fit under 3.3V). Both cathodes on SSR_EN so the watchdog gates the
indicator too. GND pour keepout across the barrier, checked by
check_isolation.py."
```

---

### Task 8: Aux output bank — ULN2003 with an external coil rail

**Files:**
- Modify: `hardware/kicad/generator/design.py`

**Interfaces:**
- Consumes: Task 4 (ULN2003 boot behaviour), Task 3 (`AUX1`, `AUX2`, `AUX3`).
- Produces: `AUX_VP`, `AUX1_OUT`, `AUX2_OUT`, `AUX3_OUT`; designator `U6`, terminal `J10`.

- [ ] **Step 1: Add the bank**

```python
    # --- Aux output bank (vent / purge / spare) --------------------------
    # ULN2003A: 7 Darlington channels with integrated freewheel diodes to COM,
    # and a JLCPCB *Basic* part - so it replaces ~19 discrete parts at zero
    # feeder fee. Pin order is I1..I7 = 1..7, GND = 8, COM = 9, O7..O1 = 10..16
    # (note O1 is pin 16, so the outputs run backwards).
    #
    # COM goes to AUX_VP, its own screw terminal, NOT the board's +5V: a gas
    # purge solenoid is realistically 12V or 24V DC and the ULN is rated 50V /
    # 500mA per channel. A solder link (SJ1) ties AUX_VP to +5V for plain 5V
    # relays. The buzzer deliberately keeps its discrete driver so a 5V buzzer
    # and a 24V solenoid never share a COM rail.
    #
    # R20-R22 hold the inputs low while the ESP32 pins are high-impedance at
    # boot - a floating Darlington input must not energize a solenoid.
    "U6": dict(lib="Transistor_Array", sym="ULN2003A",
               fp="Package_SO:SOIC-16_3.9x9.9mm_P1.27mm",
               fpf="SOIC-16_3.9x9.9mm_P1.27mm.kicad_mod",
               value="ULN2003A", at=(44.0, 60.0, 0),
               pins={"1": "AUX1", "2": "AUX2", "3": "AUX3",
                     "4": None, "5": None, "6": None, "7": None,
                     "8": "GND", "9": "AUX_VP",
                     "10": None, "11": None, "12": None, "13": None,
                     "14": "AUX3_OUT", "15": "AUX2_OUT", "16": "AUX1_OUT"}),
    "R20": dict(lib="Device", sym="R", fp=R0805[0], fpf=R0805[1],
                value="10k", at=(38.0, 56.0, 90),
                pins={"1": "AUX1", "2": "GND"}),
    "R21": dict(lib="Device", sym="R", fp=R0805[0], fpf=R0805[1],
                value="10k", at=(38.0, 59.0, 90),
                pins={"1": "AUX2", "2": "GND"}),
    "R22": dict(lib="Device", sym="R", fp=R0805[0], fpf=R0805[1],
                value="10k", at=(38.0, 62.0, 90),
                pins={"1": "AUX3", "2": "GND"}),
    # 4-position terminal: coil rail + three switched low sides.
    "J10": dict(lib="Connector", sym="Screw_Terminal_01x04",
                fp="TerminalBlock_Phoenix:TerminalBlock_Phoenix_MKDS-1,5-4-5.08_1x04_P5.08mm_Horizontal",
                fpf="TerminalBlock_Phoenix_MKDS-1,5-4-5.08_1x04_P5.08mm_Horizontal.kicad_mod",
                value="AUX", at=(22.5, 60.0, 270),
                pins={"1": "AUX_VP", "2": "AUX1_OUT",
                      "3": "AUX2_OUT", "4": "AUX3_OUT"}),
    # Solder link: AUX_VP <- +5V for 5V relay coils. Open by default.
    "SJ1": dict(lib="Jumper", sym="SolderJumper_2_Open",
                fp="Jumper:SolderJumper-2_P1.3mm_Open_RoundedPad1.0x1.5mm",
                fpf="SolderJumper-2_P1.3mm_Open_RoundedPad1.0x1.5mm.kicad_mod",
                value="AUX_VP=5V", at=(30.0, 55.0, 0),
                pins={"1": "+5V", "2": "AUX_VP"}),
```

- [ ] **Step 2: Verify**

```bash
cd hardware/kicad && python3 generator/design.py | grep -E "AUX"
```

Expected: `AUX1 AUX2 AUX3 AUX1_OUT AUX2_OUT AUX3_OUT AUX_VP` all with ≥2 pins, no
`!! single-pin`.

```bash
python3 generator/gen_sch.py bisque-controller.kicad_sch && python3 generator/check_netlist.py bisque-controller.kicad_sch
```

Expected: `PASS`.

- [ ] **Step 3: Commit**

```bash
git add hardware/kicad/generator/design.py hardware/kicad/bisque-controller.kicad_sch
git commit -m "feat(hw): ULN2003 aux bank with external coil rail

Vent, purge and spare on one Basic part with integrated flyback diodes.
COM lands on its own AUX_VP terminal so 12/24V solenoids work; SJ1 links
it to +5V for 5V relays."
```

---

### Task 9: Protected inputs ×3 and TVS

**Files:**
- Modify: `hardware/kicad/generator/design.py`

**Interfaces:**
- Consumes: Task 3 (`IN1`, `IN2`, `IN3`).
- Produces: `IN1_RAW`, `IN2_RAW`, `IN3_RAW`; terminal `J11`, TVS `D5`.

- [ ] **Step 1: Generalise rev A's lid conditioning to three channels**

Rev A's `R12`/`R13`/`C12` become input 1. Re-point them from `LID_IN`/`LID_SW` to
`IN1_RAW`/`IN1`, then add two more copies plus the TVS and terminal:

```python
    # --- Protected dry-contact inputs (lid / gas flow / spare) -----------
    # Rev A's proven conditioning, three times over: 1k series, 10k pull-up to
    # +3V3, 100nF to GND. Open contact reads HIGH, so a broken wire, a pulled
    # connector or a failed-open switch all read "open" and fail safe.
    # Wire a dry contact between the channel and J11.4 (GND).
    "R12": dict(lib="Device", sym="R", fp=R0805[0], fpf=R0805[1],
                value="1k", at=(96.0, 100.0, 180),
                pins={"1": "IN1_RAW", "2": "IN1"}),
    "R13": dict(lib="Device", sym="R", fp=R0805[0], fpf=R0805[1],
                value="10k", at=(92.0, 97.0, 0),
                pins={"1": "+3V3", "2": "IN1"}),
    "C12": dict(lib="Device", sym="C", fp=C0805[0], fpf=C0805[1],
                value="100nF", at=(92.0, 100.0, 0),
                pins={"1": "IN1", "2": "GND"}),
    "R23": dict(lib="Device", sym="R", fp=R0805[0], fpf=R0805[1],
                value="1k", at=(96.0, 104.0, 180),
                pins={"1": "IN2_RAW", "2": "IN2"}),
    "R24": dict(lib="Device", sym="R", fp=R0805[0], fpf=R0805[1],
                value="10k", at=(92.0, 103.0, 0),
                pins={"1": "+3V3", "2": "IN2"}),
    "C23": dict(lib="Device", sym="C", fp=C0805[0], fpf=C0805[1],
                value="100nF", at=(92.0, 106.0, 0),
                pins={"1": "IN2", "2": "GND"}),
    "R25": dict(lib="Device", sym="R", fp=R0805[0], fpf=R0805[1],
                value="1k", at=(96.0, 108.0, 180),
                pins={"1": "IN3_RAW", "2": "IN3"}),
    "R26": dict(lib="Device", sym="R", fp=R0805[0], fpf=R0805[1],
                value="10k", at=(92.0, 109.0, 0),
                pins={"1": "+3V3", "2": "IN3"}),
    "C24": dict(lib="Device", sym="C", fp=C0805[0], fpf=C0805[1],
                value="100nF", at=(92.0, 112.0, 0),
                pins={"1": "IN3", "2": "GND"}),
    # SRV05-4: 1 IO1, 2 VN(GND), 3 IO2, 4 IO3, 5 VP(+3V3), 6 IO4.
    # Rev A skipped a TVS because one feeder fee for a single input was not
    # worth it; rev B takes the externally exposed net count from two to ~ten,
    # so one array covers the board. IO4 is spare.
    "D5": dict(lib="Power_Protection", sym="SRV05-4",
               fp="Package_TO_SOT_SMD:SOT-23-6", fpf="SOT-23-6.kicad_mod",
               value="SRV05-4", at=(101.0, 104.0, 0),
               pins={"1": "IN1_RAW", "2": "GND", "3": "IN2_RAW",
                     "4": "IN3_RAW", "5": "+3V3", "6": None}),
    "J11": dict(lib="Connector", sym="Screw_Terminal_01x04",
                fp="TerminalBlock_Phoenix:TerminalBlock_Phoenix_MKDS-1,5-4-5.08_1x04_P5.08mm_Horizontal",
                fpf="TerminalBlock_Phoenix_MKDS-1,5-4-5.08_1x04_P5.08mm_Horizontal.kicad_mod",
                value="INPUTS", at=(112.0, 104.0, 90),
                pins={"1": "IN1_RAW", "2": "IN2_RAW",
                      "3": "IN3_RAW", "4": "GND"}),
```

- [ ] **Step 2: Remove the lid signal from J7**

J7 pin 6 carried `LID_IN` in rev A. The lid now lands on `J11`, so change J7 pin 6 to
`None` (Task 11 re-purposes the freed header pins).

- [ ] **Step 3: Verify**

```bash
cd hardware/kicad && python3 generator/design.py | grep -E "IN[123]"
```

Expected: `IN1 IN1_RAW IN2 IN2_RAW IN3 IN3_RAW` all with ≥2 pins, no `!! single-pin`, and
no remaining `LID_IN` or `LID_SW` net.

```bash
python3 generator/gen_sch.py bisque-controller.kicad_sch && python3 generator/check_netlist.py bisque-controller.kicad_sch
```

Expected: `PASS`.

- [ ] **Step 4: Commit**

```bash
git add hardware/kicad/generator/design.py hardware/kicad/bisque-controller.kicad_sch
git commit -m "feat(hw): three protected dry-contact inputs with TVS

Lid, gas-flow interlock and a spare, all on rev A's proven RC conditioning
and one SRV05-4 array. Lid moves off J7 onto its own terminal."
```

---
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
