BenSeverson/bisque/docs/superpowers/plans/2026-08-15-rev-a-freeze-and-rev-b-transition.md

# Rev A Freeze and Rev B Transition — Implementation Plan

> **For agentic workers:** REQUIRED SUB-SKILL: Use superpowers:subagent-driven-development (recommended) or superpowers:executing-plans to implement this plan task-by-task. Steps use checkbox (`- [ ]`) syntax for tracking.

**Goal:** Freeze the rev A perfboard firmware behind a verified tag and a `v1` branch, hand `main` to rev B, and correct every document that the handover makes false.

**Architecture:** Rev A is preserved as a published GitHub release, not a maintained line — no board profile, no CI matrix, no OTA changes. `main` becomes rev B only. The documentation debt is then paid in one follow-up PR so `main` is not left internally inconsistent.

**Tech Stack:** git/GitHub Actions (`release.yml` triggers on `v*`, `build.yml` on `main` + PRs to `main`), ESP-IDF, `make test` / `make lint` / `make pcb-check`.

**Spec:** [`docs/superpowers/specs/2026-08-15-rev-a-freeze-and-rev-b-firmware-design.md`](../specs/2026-08-15-rev-a-freeze-and-rev-b-firmware-design.md)

## Global Constraints

- **Task 1 is a human gate.** It requires physical hardware — flashing the perfboard and firing a real profile end to end. An agent cannot complete it and must not mark it done.
- The freeze tag must be an **annotated** tag matching `v*` and must be an **ancestor of `main`**. `v1.0.0` is not (`git merge-base --is-ancestor v1.0.0 main` is false, `git describe --tags main` fails), which is why `scripts/version.sh` currently prints a bare hash.
- **Never create a tag named `v1`.** `refs/heads/v1` and `refs/tags/v1` would both answer to `v1`. Tags on that line stay fully qualified: `v1.1.0`, `v1.1.1`.
- **Do not push any new `v*` tag after Task 1** until the PCBs arrive. An untagged `main` is the mechanism that keeps the frozen perfboard from being offered a rev B image.
- After editing any firmware C/H file, run `clang-format -i` on it. CI's `clang-format` job fails on unformatted code.
- Commit messages end with `Co-Authored-By: Claude Opus 5 <noreply@anthropic.com>`.

## File Structure

| File | Task | Responsibility after this plan |
|---|---|---|
| `docs/heat-treating-extension-plan.md` | 3 | Phase-3 TC plan, corrected to a driver *replacement* |
| `components/app_config/include/app_config.h` | 4 | `APP_PID_KD_DEFAULT` rationale, no longer citing MAX31855 quantization as settled |
| `components/pid_control/pid_control.c` | 4 | Same rationale in the derivative-filter comment |
| `tests/host/stubs/safety_host.c` | 4 | Lid-switch default comment, GPIO 21 → 4 |
| `docs/perfboard-layout.svg` | 5 | Marked historical (rev A) |
| `docs/wiring-diagram.svg` | 5 | Marked historical (rev A) |
| `README.md` | 5 | Perfboard BOM/wiring marked rev A; MAX31855 → MAX31856 in the component tree |
| `CLAUDE.md` | 5 | Hardware Diagrams section and component tree point at rev B |

---

### Task 1: Verify and freeze rev A

**HUMAN GATE — requires the physical perfboard kiln. Do not mark complete without a real firing.**

**Files:** none modified. Produces a tag, a branch, and a GitHub release.

**Interfaces:**
- Produces: the annotated tag `v1.1.0` and the branch `v1`, both consumed by Task 2's ordering constraint (rev B must not reach `main` before the freeze exists).

- [ ] **Step 1: Confirm you are freezing rev A, not rev B**

```bash
git switch main
git log --oneline -1
grep -A1 'config KILN_PIN_BTN_UP' main/Kconfig.projbuild
```

Expected: `KILN_PIN_BTN_UP` defaults to `4` (the rev A perfboard map). If it defaults to `38`, you are on the rev B branch — stop, switch to `main`.

- [ ] **Step 2: Build the freeze candidate**

```bash
./build.sh
```

Expected: `=== Build Complete ===`. This builds the web UI and firmware together; the frozen image must include the SPIFFS web bundle.

- [ ] **Step 3: Flash the perfboard**

```bash
. ./scripts/idf-env.sh && idf.py flash monitor
```

Expected: the kiln boots to the splash and then the dashboard, the 5-way nav switch moves focus, and a temperature reads.

- [ ] **Step 4: Fire a real profile end to end**

Load `docs/smoke-test-profile.json` (or a real bisque profile) and run it to completion on the actual kiln. Follow `docs/bench-smoke-test.md`.

Expected: the firing starts, ramps, holds, and completes; the SSR cycles; history records the run. **This is the step that makes the tag a proven recovery point.** If anything fails, fix it on `main` and restart from Step 2.

- [ ] **Step 5: Tag the verified commit**

```bash
git tag -a v1.1.0 -m "Rev A perfboard — final firmware

Verified on the perfboard kiln with a complete firing before tagging.
Rev A is frozen here: main moves to rev B hardware after this tag.
Recovery image for the perfboard; see docs/superpowers/specs/2026-08-15-rev-a-freeze-and-rev-b-firmware-design.md"
git push origin v1.1.0
```

- [ ] **Step 6: Verify the tag actually describes `main`**

```bash
git merge-base --is-ancestor v1.1.0 main && echo OK-ancestor
git describe --tags main
./scripts/version.sh
```

Expected: `OK-ancestor`, then `v1.1.0` from both commands (not a bare hash). If `describe` still fails, the tag is on the wrong commit — delete and redo it before going further.

- [ ] **Step 7: Create the `v1` branch**

```bash
git branch v1 v1.1.0
git push -u origin v1
```

Do not protect it, do not open PRs against it, do not add it to any workflow trigger.

- [ ] **Step 8: Archive the release artifacts**
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
