BenSeverson/bisque/docs/screenshots/lcd-autotune.png

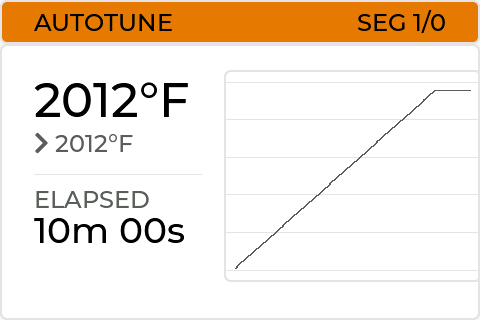
docs/screenshots/lcd-autotune.png
