BenSeverson/bisque/docs/screenshots/lcd-modal-stop-confirm.png

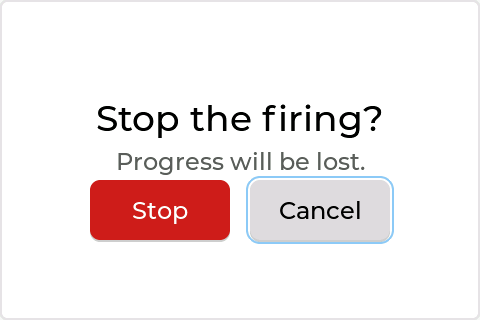
docs/screenshots/lcd-modal-stop-confirm.png
