BenSeverson/bisque/components/safety/include/lid_state.h

#pragma once

/**
 * State of the lid/door interlock switch, as reported to the UIs.
 *
 * Deliberately standalone — no esp_err.h, no FreeRTOS — so the three consumers
 * can share one type without dragging the safety driver's dependencies along:
 * the pure JSON builders in web_server/api_json.c (host-buildable by contract),
 * the LVGL dashboard (which the SDL simulator compiles with no ESP-IDF at all),
 * and safety.c itself.
 *
 * NOT_FITTED is a distinct state rather than a "closed": a kiln with no switch
 * would otherwise show an indicator permanently reading "lid closed", reporting
 * on hardware that isn't there. Consumers omit the reading entirely in that
 * case.
 *
 * Note that CONFIG_KILN_PIN_LID_SWITCH now defaults to GPIO 4 to match the
 * PCB (J11 pin 1, the rev B protected-input terminal), so NOT_FITTED only
 * appears on builds that explicitly set it back to -1.
 * A build with no switch fitted must do that, or jumper the input to GND —
 * otherwise the pulled-up pin reads OPEN and the interlock holds the SSR off.
 */
typedef enum {
    LID_STATE_NOT_FITTED = -1,
    LID_STATE_CLOSED = 0,
    LID_STATE_OPEN = 1,
} lid_state_t;
