BenSeverson/bisque/hardware/kicad/generator/kicad_build.py

"""Build bisque-controller.kicad_pcb through KiCad's own engine (pcbnew API).

Loads the real system-library footprints, places them per design.py,
routes with router.py (obstacle model taken from the *loaded* pad
geometry, so it always matches the libraries actually used), then lets
KiCad do the rest: `kicad-cli pcb drc --refill-zones` fills the ground
pours and runs KiCad's real DRC. The saved board is a genuine
pcbnew-written file. Requires KiCad 10+.

Usage: python3 kicad_build.py [--no-route] <out.kicad_pcb>

`--no-route` is the fast path. Routing 93 nets across 141 parts is ~91%
of the 158 s a full build costs, and several classes of change cannot
touch copper at all: silkscreen placement (silk.py), 3D model offsets
(MODEL_FIXUP), the title block, reference-designator text metrics. With
`--no-route` the tracks, vias and filled zones are read back off the
existing board and everything else is re-derived by the same code a full
build runs, so the result is byte-identical for the same design.py -
`check_fast_path.py` proves that rather than assuming it. Anything that
moves a part, changes connectivity, or changes a routing parameter needs
the full path; `verify_reusable()` below refuses the fast one when
design.py and the loaded board have drifted apart.
"""
import math
import os
import shutil
import subprocess
import sys
import tempfile

sys.path.insert(0, os.path.dirname(__file__))
try:
    # macOS: pcbnew's settings manager needs a live wx app in standalone use
    import wx
    _wx_app = wx.App(False)
    if hasattr(wx, "DisableAsserts"):
        wx.DisableAsserts()
except ImportError:
    pass
import pcbnew
from canonicalize import canonicalize_file
from design import COMPONENTS, netlist, BX0, BY0, BX1, BY1
from project_sync import sync_project
import router as R
import silk
import stages
from gen_jlc import DNP, NOT_ASSEMBLED
from gen_pcb import (all_seeds, route_all, ripup_retry, promoted_order, plane_vias,
                     apply_stackup, SILK, SILK_GRAPHICS, MANUAL_VIAS,
                     EP_VIA_GRID, STITCH_VIAS, is_ep_pad, TP_LABEL_TEXTS, LEGEND_OWNER,
                     TP_LEGEND_OK,
                     PLANE_LAYER, HIDE_REFS, STRIP_FP_SILK, sync_netclasses,
                     netclass_table,
                     USB_KEEPOUT_MARGIN, USB_DIFF_PAIR, route_usb_pair,
                     U2_POUR, COPPER_LAYER_TYPE, FID_KEEPOUT)

# Copper stack-up. Rev B is 4-layer (spec 6.1): signals on the outside, an
# unbroken GND plane on In1.Cu and the +3V3 plane on In2.Cu. router.py still
# knows only two routing layers - 0 and 1 - and they map to F.Cu and B.Cu; the
# inner layers carry no tracks at all, only the plane fills, so the router
# never needs to model them. Vias stay through-hole, which is what lets a pad
# reach either plane with a single hole.
COPPER_LAYERS = 4
LAYER = {0: pcbnew.F_Cu, 1: pcbnew.B_Cu}
PLANE_CU = {"In1.Cu": pcbnew.In1_Cu, "In2.Cu": pcbnew.In2_Cu}


def _find_fp_base():
    cand = [os.environ.get("KICAD_FOOTPRINT_DIR", "")]
    cand += ["/usr/share/kicad/footprints",
             "/usr/local/share/kicad/footprints",
             "/Applications/KiCad/KiCad.app/Contents/SharedSupport/footprints",
             r"C:\Program Files\KiCad\10.0\share\kicad\footprints"]
    import glob as _g
    cand += sorted(_g.glob("/usr/share/kicad*/footprints"), reverse=True)
    for c in cand:
        if c and os.path.isdir(c):
            return c
    sys.exit("KiCad footprint libraries not found - set KICAD_FOOTPRINT_DIR")


import glob
FPBASE = _find_fp_base()


MM = pcbnew.FromMM

# Minimum silkscreen stroke, mm. JLCPCB quotes 0.153 mm as the floor below
# which a legend line may print blurred or drop out entirely. 0.16 rather than
# KiCad's 0.15 house value on purpose: 0.15 is 2.4 um UNDER the quoted number,
# which is finer than a screen resolves and would almost certainly print, but
# "under the published figure by less than anyone can measure" is a sentence
# nobody should have to reconstruct while reading a DFM report. 0.16 is over
# it, and it was free - the placer seats all 204 labels with 0 silk-on-silk at
# either value, so there was no trade to make.
#
# Both silk TEXT sites clamp here, and so - since JLC's DFM report on the
# 2026-10-04 package - do footprint OUTLINES (`widen_fp_silk`). They arrive at
# 0.12 mm from KiCad's stock libraries and used to be left there on the
# argument that nobody reads a part outline during assembly. Two things broke
# that: JLC's DFM flags every one of them under its line-width floor, and some
# outlines ARE read - C46's chamfered outline and `+` are the board's only
# printed polarity mark on a 100 uF electrolytic, and LED1's corner and U1's
# pin-1 marker orient parts by eye. The cost the old note feared is real but
# small: the placer's outline obstacles grow by 0.02 mm a side. It is done at
# build time, as STRIP_FP_SILK is, so no .kicad_mod is edited.
SILK_MIN_STROKE = 0.16

_major = int(pcbnew.Version().split(".")[0])
if _major < 10:
    sys.exit("kicad_build.py requires KiCad 10+ (found %s)" % pcbnew.Version())

# The footprint reader, resolved once. Belt-and-braces against the swig
# type-table corruption `strip_derived()` documents: while a live pcbnew
# session is in that state, PCB_IO_MGR.FindPlugin() is one of the calls that
# hands back an untyped pointer - here, one with no FootprintLoad on it. A
# handle taken before any board is loaded keeps working.
_FP_PLUGIN = pcbnew.PCB_IO_MGR.FindPlugin(pcbnew.PCB_IO_MGR.KICAD_SEXP)


def load_footprint(lib, name):
    path = os.path.join(FPBASE, lib + ".pretty")
    return _FP_PLUGIN.FootprintLoad(path, name)


def V(x, y):
    return pcbnew.VECTOR2I(MM(x), MM(y))


# 3D models. Cosmetic only - no fab output (gerbers, drill, BOM, CPL, DRC)
# touches a model at all - but the renders in 3d/ are how placement and silk
# get eyeballed without a board in hand, so a part that renders as bare pads
# or floats off its footprint costs real time to diagnose.
#
# Five footprints need help. KiCad 10 ships NO model for four of them, and its
# failure mode is silence: `kicad-cli pcb render` exits 0, prints "Loading 3D
# models...", and omits the part. That is why every model this board depends on
# is vendored into 3dmodels/ and referenced through ${KIPRJMOD} rather than
# ${KICAD10_3DMODEL_DIR} - the system path is not reproducible (a KiCad upgrade
# wipes a hand-installed file, and a fresh clone never had one), and the whole
# point of a committed render is that a clean machine can reproduce it.
#
# `file` is a stem in 3dmodels/; see that directory's README for provenance.
# `offset` is mm in the footprint frame, `rotate` degrees about X/Y/Z.
#
# U1 - Espressif's own STEP is authored with its origin at a body CORNER (body
# spans X 0..18, Y 0..19.2 mm, measured off the STEP) while KiCad's footprint
# origin is the body CENTRE. Two independent derivations agree on -9.6:
#   * body centre from the STEP bounding box = (9.0, 9.6) -> offset (-9, -9.6)
#   * Espressif's own footprint uses (offset -9 -9.75 0), and their footprint
#     origin differs from KiCad's by exactly dY -0.15 mm (verified across all
#     40 signal pads, dX 0.0) -> -9.75 + 0.15 = -9.60
#
# J1 - the only one of the four LCSC models needing a correction. Unrotated,
# the shell sits ~8.9 mm north of its pads, which reads as a translation but is
# not one: EasyEDA stores a per-model display rotation next to the geometry
# (the SVGNODE's c_rotation, "0,0,180" for this part) and the STEP is authored
# in the unrotated frame. Applying it puts all 12 pins on the 12 signal pads
# with the mouth facing the board edge. C515890's c_rotation is "0,0,90" and is
# deliberately NOT applied - a square QFN is invariant under it, so it would be
# an untestable claim; C318884's is "0,0,0".
MODEL_FIXUP = {
    "U1": dict(file="ESP32-S3-WROOM-1U", offset=(-9.0, -9.6, 0.0)),
    "J1": dict(file="USB_C_Receptacle_HRO_TYPE-C-31-M-12", rotate=(0, 0, 180)),
    "U7": dict(file="QFN-28-1EP_5x5mm_P0.5mm_EP3.1x3.1mm"),
    "SW1": dict(file="SW_Push_1P1T_XKB_TS-1187A"),
    "SW2": dict(file="SW_Push_1P1T_XKB_TS-1187A"),
    # Y1 - the fifth footprint KiCad 10 ships no model for. It DECLARES one at
    # ${KICAD10_3DMODEL_DIR}/Oscillator.3dshapes/..., and that directory exists
    # with nine other parts in it, so the reference looks satisfied right up
    # until the render quietly omits the part. c_rotation is "0,0,0", so unlike
    # J1 there is nothing to correct.
    "Y1": dict(file="Oscillator_SMD_Abracon_ASE-4Pin_3.2x2.5mm"),
    # F1 - the sixth, and the one that proves the trap is still live. The
    # footprint declares ${KICAD10_3DMODEL_DIR}/Fuse.3dshapes/
    # Fuse_1812_4532Metric.step and that directory exists with 0402, 0603,
    # 0805, 1206 and 1210 in it - just not 1812. So the reference resolves to
    # a real directory, the render exits 0, and F1 simply is not there.
    # Nobody noticed until it was spotted in the committed image.
    # c_rotation "0,0,0", so nothing to correct.
    "F1": dict(file="Fuse_1812_4532Metric"),
}
MODEL_DIR = "${KIPRJMOD}/3dmodels/%s.step"


def build_board(existing=None):
    """Everything about the board except copper.

    `existing` is an already-routed board that `strip_derived()` has just
    emptied of footprints and board graphics; it keeps its tracks, vias and
    filled zones and gets the rest rebuilt here. Passing it through the same
    function as a fresh build - rather than a separate "patch the loaded
    board" routine - is what makes `--no-route` byte-identical by
    construction instead of by inspection.
    """
    board = pcbnew.BOARD() if existing is None else existing
    board.SetCopperLayerCount(COPPER_LAYERS)
    bds = board.GetDesignSettings()
    bds.m_TrackMinWidth = MM(0.2)
    bds.m_ViasMinSize = MM(0.5)
    bds.m_MinThroughDrill = MM(0.3)
    bds.m_CopperEdgeClearance = MM(0.3)

    # Title block. The schematic has carried one since rev A; the board did
    # not, so every page of the exported board PDF showed a blank Title and
    # Rev - on six pages that otherwise look nearly identical, since four
    # copper layers of the same outline are hard to tell apart at a glance.
    # Values mirror gen_sch.py's block so the two documents agree. The date is
    # deliberately FIXED, not today's: check_canonical.py requires rebuilds to
    # be byte-identical, and a live date would break that every midnight.
    # A fresh TITLE_BLOCK rather than board.GetTitleBlock(): on a board that
    # came off disk the getter hands back an untyped swig pointer with no
    # methods on it. Building one here also means every field is set from
    # this table, so `--no-route` cannot inherit a stale one.
    tb = pcbnew.TITLE_BLOCK()
    tb.SetTitle("Bisque Kiln Controller")
    tb.SetDate("2026-09-19")
    tb.SetRevision("B")
    tb.SetCompany("Bisque project")
    tb.SetComment(0, "ESP32-S3-WROOM-1U-N16R2 + 2x MAX31856 + dual SSR + ADE7953")
    tb.SetComment(1, "4-layer, 100 x 100 mm, JLCPCB standard process")
    board.SetTitleBlock(tb)

    # nets. A .kicad_pcb of this vintage carries no net table - tracks, vias
    # and zones name their net inline - so a reused board already has every
    # net the copper on it mentions, and re-minting them would orphan that
    # copper. Net *codes* are internal only and never reach the file.
    nets = {}
    for name in sorted(netlist()):
        n = board.FindNet(name) if existing is not None else None
        if n is None:
            n = pcbnew.NETINFO_ITEM(board, name)
            board.Add(n)
        nets[name] = n

    # footprints
    fps = {}
    for ref, c in COMPONENTS.items():
        lib, name = c["fp"].split(":", 1)
        fp = load_footprint(lib, name)
        assert fp is not None, c["fp"]
        fx, fy, frot = c["at"]
        fp.SetReference(ref)
        fp.SetValue(c["value"])
        fp.SetPosition(V(fx, fy))
        fp.SetOrientationDegrees(frot)
        for pad in fp.Pads():
            num = str(pad.GetNumber())
            net = c["pins"].get(num)
            if net:
                pad.SetNet(nets[net])
            # library EP thermal vias use 0.2mm drills; upsize to 0.3mm so
            # the whole board stays inside JLCPCB's standard drill range
            if pad.GetAttribute() == pcbnew.PAD_ATTRIB_PTH:
                d = pad.GetDrillSize().x
                if 0 < d < MM(0.3):
                    pad.SetDrillSize(pcbnew.VECTOR2I(MM(0.3), MM(0.3)))
            # solid pour connection where thermals starve (module GND/EP,
            # USB shell) — these want maximum copper anyway
            if (ref == "U1" and num in ("1", "40", "41")) or \
               (ref == "J1" and num in ("A1", "B1", "A12", "B12", "S1")):
                pad.SetLocalZoneConnection(pcbnew.ZONE_CONNECTION_FULL)
        fix = MODEL_FIXUP.get(ref)
        if fix:
            # fp.Models() hands back COPIES - mutating them writes nothing
            # back to the footprint. Rebuild the entry instead.
            #
            # The scale and rotation are unpacked to plain floats HERE rather
            # than carried as VECTOR3Ds. `m` is a temporary, and `m.m_Scale`
            # is a reference into it, so holding that reference past the
            # comprehension leaves it dangling: whether it still reads (1,1,1)
            # or has become (0,0,0) depends on when Python happens to collect
            # the temporary. A model scaled to zero renders nothing at all,
            # and it made the board file differ between two runs of an
            # unchanged design - a determinism bug that only showed up once
            # the fast path changed the allocation pattern around it.
            old = [((m.m_Scale.x, m.m_Scale.y, m.m_Scale.z),
                    (m.m_Rotation.x, m.m_Rotation.y, m.m_Rotation.z))
                   for m in fp.Models()]
            # Every ref here names a footprint the library ships a <model>
            # entry for, even when it ships no file to back it. Rebuilding a
            # missing entry from nothing would work, but losing one is a
            # library change worth hearing about rather than papering over.
            assert old, "%s: MODEL_FIXUP set but footprint has no 3D model" % ref
            fp.Models().clear()
            for scale, rot in old:
                nm = pcbnew.FP_3DMODEL()
                nm.m_Filename = MODEL_DIR % fix["file"]
                nm.m_Scale = pcbnew.VECTOR3D(*scale)
                nm.m_Rotation = pcbnew.VECTOR3D(*fix.get("rotate", rot))
                nm.m_Offset = pcbnew.VECTOR3D(*fix.get("offset", (0.0, 0.0, 0.0)))
                fp.Models().push_back(nm)
        # A part that is not fitted must not be rendered as if it were. J13 is
        # the AC-sense header, deliberately DNP - the board ships with the
        # voltage channel unconnected - and it was drawing a full 2-pin header
        # body in 3d/, which reads as "this is populated". The set is the one
        # gen_jlc already keeps, so this cannot drift from the BOM: if a part
        # is excluded from assembly it is also absent from the picture.
        #
        # The MODEL is hidden rather than the footprint marked DNP, and that
        # is deliberate. `kicad-cli pcb render` has no DNP switch; whether it
        # draws DNP parts follows an appearance PRESET stored in the project,
        # which is a setting a GUI session can change out from under a
        # committed image. m_Show is a property of the board file itself, so
        # the render is a function of the design either way.
        #
        # Rebuilt, not mutated, for the same reason MODEL_FIXUP above rebuilds:
        # fp.Models() hands back COPIES, so `for m in fp.Models(): m.m_Show =
        # False` sets the flag on a temporary and writes nothing. It reports
        # no error and the board is unchanged - this shipped once exactly that
        # way, with J13 still drawing a populated header.
        # The footprint attribute, set from the same table gen_sch.py writes
        # `(dnp yes)` from, so the two documents cannot disagree and
        # --schematic-parity has nothing to compare unfavourably. This is a
        # narrower set than NOT_ASSEMBLED below on purpose: DNP means a part
        # that could be fitted and is not, and a test point or fiducial is not
        # a part at all.
        if ref in DNP:
            fp.SetDNP(True)
        if ref in NOT_ASSEMBLED and fp.Models():
            keep = [(m.m_Filename,
                     (m.m_Scale.x, m.m_Scale.y, m.m_Scale.z),
                     (m.m_Rotation.x, m.m_Rotation.y, m.m_Rotation.z),
                     (m.m_Offset.x, m.m_Offset.y, m.m_Offset.z))
                    for m in fp.Models()]
            fp.Models().clear()
            for fn, scale, rot, off in keep:
                nm = pcbnew.FP_3DMODEL()
                nm.m_Filename = fn
                nm.m_Scale = pcbnew.VECTOR3D(*scale)
                nm.m_Rotation = pcbnew.VECTOR3D(*rot)
                nm.m_Offset = pcbnew.VECTOR3D(*off)
                nm.m_Show = False
                fp.Models().push_back(nm)
        board.Add(fp)
        fps[ref] = fp
    # Silk: one size for every reference designator. WHERE each one lands is
    # not decided here - `silk.py` derives it after the board texts exist (see
    # add_outline_and_silk). Rev B carried a hand-maintained list of 18 refs
    # nudged out of collisions at this point; at 141 parts a patch list cannot
    # keep up, and it didn't - DRC reported 109 silkscreen violations across
    # 49 designators.
    #
    # SILK_MIN_STROKE is a fab floor, not a taste setting. JLCPCB's published
    # legend capability is 0.153 mm minimum stroke and 0.8 mm minimum height;
    # below either, the line is documented as possibly blurred or dropped
    # outright. These labels are load-bearing rather than decorative - the 13
    # through-hole parts on `jlcpcb/hand-solder-parts.csv` are fitted by hand
    # against them after the board comes back - so an illegible designator is
    # a functional defect. The stroke used to be 0.12 mm, 0.033 mm UNDER the
    # floor.
    #
    # The HEIGHT stays at 0.8 mm, which meets the minimum exactly, and the
    # 0.1875 stroke ratio that gives is bolder than KiCad's 0.15 convention.
    # That is deliberate, and taking it to 0.9 mm for a prettier 1:6 ratio was
    # tried and reverted: `silk.py` is a greedy placer over a live index, so
    # making all 141 designators 12.5% taller does not just cost those labels
    # room - it reorders who wins which gap board-wide. The one casualty was
    # the `INPUTS 1 / 2 / 3 / GND` legend, which lost its 1.82 mm slot between
    # the J6/J7 header row (F.Fab bottom y=106.93) and J11 (F.Fab top
    # y=108.75) and printed across the terminal block it names. Nothing was
    # wrong with the anchor; a neighbour simply got there first. Stroke width
    # was the actual fab defect, so stroke width is all that changed.
    for ref, fp in fps.items():
        t = fp.Reference()
        t.SetTextSize(pcbnew.VECTOR2I(MM(0.8), MM(0.8)))
        t.SetTextThickness(MM(SILK_MIN_STROKE))
        # The designator is not the only text a footprint can put on silk.
        # Two here arrive from the stock libraries at 1.0/0.15 - under the
        # floor by the same 2.4 um the constant above declines to ship - and
        # neither this loop nor the SILK table would otherwise reach them,
        # which would leave "every silk text clears the floor" true only of
        # the text we author. Clamp, never shrink: LED1's pin-1 mark and BZ1's
        # `+` are deliberately bolder than the floor in their own libraries.
        for it in list(fp.GraphicalItems()) + [fp.Value()]:
            if it.GetLayer() == pcbnew.F_SilkS and hasattr(it, "GetText"):
                if it.GetTextThickness() < MM(SILK_MIN_STROKE):
                    it.SetTextThickness(MM(SILK_MIN_STROKE))
        # Hidden, not deleted: the field still exists, so the netlist, the
        # BOM and the CPL are untouched and DRC still knows what it is - it
        # simply is not printed. `silk.py` and `check_silk.py` both skip an
        # invisible reference already, so this also hands the placer back the
        # four corners those labels were competing for.
        if ref in HIDE_REFS:
            t.SetVisible(False)
        # Outline-only silk that cannot meet the pad-to-silk rule on this
        # footprint at all; see gen_pcb.STRIP_FP_SILK.
        if str(fp.GetFPID().GetLibItemName()) in STRIP_FP_SILK:
            for it in list(fp.GraphicalItems()):
                if it.GetLayer() == pcbnew.F_SilkS and not hasattr(it, "GetText"):
                    fp.Remove(it)
                    _REMOVED.append(it)   # never let swig collect it; see strip_derived()
        widen_fp_silk(fp)
    return board, nets, fps


# Pad-to-silk clearance, mm - the `JLC: pad to silkscreen` rule in the .dru.
PAD_SILK_CLEAR = 0.15


def _pad_gap(sh, pads):
    """Edge-to-edge distance from silk shape `sh` to the nearest mask opening.

    A mask opening is the pad's copper grown by its solder-mask expansion -
    zero on every pad here except the fiducials. Bisected on Collide() rather
    than computed, because pcbnew's SHAPE API answers "within c?" and not
    "how far?"; 20 halvings of 1 mm is under a nanometre.
    """
    lim = MM(1.0)
    best = lim
    bb = sh.BBox()
    for psh, exp in pads:
        pb = psh.BBox()
        if (pb.GetLeft() - exp - lim > bb.GetRight() or bb.GetLeft() > pb.GetRight() + exp + lim
                or pb.GetTop() - exp - lim > bb.GetBottom() or bb.GetTop() > pb.GetBottom() + exp + lim):
            continue
        if sh.Collide(psh, exp):
            return 0
        if not sh.Collide(psh, exp + best):
            continue
        lo, hi = 0, best
        for _ in range(20):
            mid = (lo + hi) // 2
            if sh.Collide(psh, exp + mid):
                hi = mid
            else:
                lo = mid
        best = hi
    return best


def widen_fp_silk(fp):
    """Clamp a footprint's silk OUTLINES to SILK_MIN_STROKE, growing away from its pads.

    A stroke widened in place moves both edges out, and on the outlines that
    already sit closest to their own copper - TP1-TP12's ring (0.141 mm) and
    U1's pin-1 corner (0.130 mm), both under the pad-to-silk rule by name in
    the .dru - that would eat the very clearance the exception budgets. So an
    outline whose widened gap falls below min(original gap, the 0.15 mm rule)
    is moved by the half-width it gained, in whichever direction gives it the
    most room: grown in radius (a ring around its pad), or slid along one of
    eight directions (a line or a marker beside one). If no move gets back to
    that floor the build fails naming the outline, rather than shipping one
    that a DRC exception would have to absorb.
    """
    floor = MM(SILK_MIN_STROKE)
    pads = [(p.GetEffectiveShape(pcbnew.F_Cu), max(0, p.GetSolderMaskExpansion(pcbnew.F_Mask)))
            for p in fp.Pads()
            if p.IsOnLayer(pcbnew.F_Cu) and p.IsOnLayer(pcbnew.F_Mask)]
    for it in fp.GraphicalItems():
        if it.GetLayer() != pcbnew.F_SilkS or hasattr(it, "GetText"):
            continue
        w = it.GetWidth()
        if w >= floor:
            continue
        before = _pad_gap(it.GetEffectiveShape(), pads)
        it.SetWidth(floor)
        need = min(before, MM(PAD_SILK_CLEAR))
        if _pad_gap(it.GetEffectiveShape(), pads) >= need:
            continue
        d = (floor - w + 1) // 2
        moves = [("move", pcbnew.VECTOR2I(round(d * math.cos(a)), round(d * math.sin(a))))
                 for a in (k * math.pi / 4 for k in range(8))]
        if it.GetShape() == pcbnew.SHAPE_T_CIRCLE:
            moves.append(("radius", d))
        best = None
        for kind, arg in moves:
            if kind == "move":
                it.Move(arg)
            else:
                it.SetRadius(it.GetRadius() + arg)
            gap = _pad_gap(it.GetEffectiveShape(), pads)
            if kind == "move":
                it.Move(pcbnew.VECTOR2I(-arg.x, -arg.y))
            else:
                it.SetRadius(it.GetRadius() - arg)
            if best is None or gap > best[0]:
                best = (gap, kind, arg)
        if best[0] < need:
            raise SystemExit("widen_fp_silk: %s %s outline cannot reach %.3f mm of its pads "
                             "at a %.2f mm stroke (best %.3f mm)"
                             % (fp.GetReference(), it.GetShapeStr(), pcbnew.ToMM(need),
                                SILK_MIN_STROKE, pcbnew.ToMM(best[0])))
        if best[1] == "move":
            it.Move(best[2])
        else:
            it.SetRadius(it.GetRadius() + best[2])


def ep_via_positions(fps):
    """(x, y, net) for every via EP_VIA_GRID asks for, from real pad geometry.

    Derived rather than tabulated so the vias follow the part if it moves, and
    inset from the pad edge by a via radius plus a little so the annulus stays
    fully inside the copper - a via breaking the pad edge is a solder-wicking
    path out of the joint, which is the whole thing via-in-pad has to avoid.
    """
    out = []
    for (ref, num), n in sorted(EP_VIA_GRID.items()):
        fp = fps[ref]
        pad = next((p for p in fp.Pads()
                    if is_ep_pad(str(p.GetNumber()), num,
                                 pcbnew.ToMM(p.GetSizeX()),
                                 pcbnew.ToMM(p.GetSizeY()))), None)
        if pad is None:
            raise SystemExit("EP_VIA_GRID: %s pad %s is not a large pad" % (ref, num))
        cx = pcbnew.ToMM(pad.GetPosition().x)
        cy = pcbnew.ToMM(pad.GetPosition().y)
        w = pcbnew.ToMM(pad.GetSizeX()); h = pcbnew.ToMM(pad.GetSizeY())
        inset = R.VIA_DIA / 2.0 + 0.15
        spanx = max(0.0, w / 2.0 - inset); spany = max(0.0, h / 2.0 - inset)
        net = pad.GetNetname()
        if isinstance(n, int):
            offsets = [(0.0 if n == 1 else (i / (n - 1.0)) * 2.0 - 1.0,
                        0.0 if n == 1 else (j / (n - 1.0)) * 2.0 - 1.0)
                       for i in range(n) for j in range(n)]
        else:
            offsets = list(n)
        for fx, fy in offsets:
            out.append((cx + fx * spanx, cy + fy * spany, net))
    return out


def build_router_model(board, fps):
    r = R.Router(BX0, BY0, BX1, BY1)
    # Antenna keepout, if the module footprint carries one. The WROOM-1U does
    # NOT - that is the point of the swap (spec 2.1): the 48 x 7 mm band the
    # WROOM-1's PCB antenna reserved is reclaimed for parts and pour, and rev
    # B places USB-C, the reset switch and three test points in it. There is
    # deliberately no computed fallback: inventing a keepout for a module that
    # has none would bar tracks from a third of the digital band.
    for z in fps["U1"].Zones():
        if z.GetIsRuleArea():
            bb = z.GetBoundingBox()
            r.add_keepout(pcbnew.ToMM(bb.GetLeft()), BY0,
                          pcbnew.ToMM(bb.GetRight()), pcbnew.ToMM(bb.GetBottom()))
    # Fiducial keepouts. A fiducial is a bare copper dot with a LOCAL pad
    # clearance override (0.6 mm) so the placement camera sees an unambiguous
    # target, and it is on no net - so the router, which reasons about nets,
    # had no reason to keep away and the pads alone do not stop it. That was
    # invisible while nothing happened to route nearby; adding the 24 V entry
    # chain put VIN_F straight past FID1 and the buck's output caps past FID3,
    # for 6 DRC violations on a board that had 0.
    #
    # 1.7 mm from centre: 0.5 mm pad radius + the 0.6 mm override + up to
    # 0.4 mm of half-track on the widest rail here, plus margin.
    for ref, fp in fps.items():
        if not ref.startswith("FID"):
            continue
        cx = pcbnew.ToMM(fp.GetPosition().x)
        cy = pcbnew.ToMM(fp.GetPosition().y)
        r.add_keepout(cx - FID_KEEPOUT, cy - FID_KEEPOUT,
                      cx + FID_KEEPOUT, cy + FID_KEEPOUT)
    pad_pos = {}
    for ref, fp in fps.items():
        c = COMPONENTS[ref]
        for pad in fp.Pads():
            ls = pad.GetLayerSet()
            on_f = ls.Contains(pcbnew.F_Cu)
            on_b = ls.Contains(pcbnew.B_Cu)
            if not (on_f or on_b):
                continue
            layers = tuple([l for l, on in ((0, on_f), (1, on_b)) if on])
            bb = pad.GetBoundingBox()
            cx = pcbnew.ToMM(bb.GetCenter().x)
            cy = pcbnew.ToMM(bb.GetCenter().y)
            w = pcbnew.ToMM(bb.GetWidth())
            h = pcbnew.ToMM(bb.GetHeight())
            num = str(pad.GetNumber())
            if pad.GetAttribute() == pcbnew.PAD_ATTRIB_NPTH or num == "":
                net = None
            else:
                net = c["pins"].get(num)
                if net is None:
                    net = "__nc_%s_%s" % (ref, num)
            # Hole geometry is not pad geometry. A slot drill (the USB-C
            # shield's `(drill oval 0.6 1.7)`) has a diameter AND a length,
            # and its centre is the pad's position, not the copper bounding
            # box centre — those differ whenever the pad has an offset. Both
            # distinctions matter to hole-to-hole clearance and neither
            # survives collapsing the drill to GetDrillSize().x.
            drill = drill_len = 0.0
            drill_ang = 0.0
            hole = None
            if pad.GetAttribute() in (pcbnew.PAD_ATTRIB_PTH,
                                      pcbnew.PAD_ATTRIB_NPTH):
                ds = pad.GetDrillSize()
                dw, dh = pcbnew.ToMM(ds.x), pcbnew.ToMM(ds.y)
                drill, drill_len = min(dw, dh), max(dw, dh)
                drill_ang = pad.GetOrientationDegrees() + (0.0 if dw >= dh else 90.0)
                hole = (pcbnew.ToMM(pad.GetPosition().x),
                        pcbnew.ToMM(pad.GetPosition().y))
            r.add_pad(net, layers, cx, cy, w, h,
                      circle=pad.GetShape() == pcbnew.PAD_SHAPE_CIRCLE,
                      drill=drill, drill_len=drill_len, drill_ang=drill_ang,
                      hole=hole)
            if num:
                pad_pos.setdefault((ref, num), []).append((cx, cy, layers, w * h))
    return r, pad_pos


def add_copper(board, nets, r):
    for s in r.result_tracks:
        t = pcbnew.PCB_TRACK(board)
        t.SetStart(V(s.x1, s.y1))
        t.SetEnd(V(s.x2, s.y2))
        t.SetWidth(MM(s.w))
        t.SetLayer(LAYER[s.layer])
        t.SetNet(nets[s.net])
        board.Add(t)
    for (net, x, y, _fixed) in r.result_vias:
        v = pcbnew.PCB_VIA(board)
        v.SetPosition(V(x, y))
        v.SetViaType(pcbnew.VIATYPE_THROUGH)
        v.SetDrill(MM(R.VIA_DRILL))
        v.SetWidth(MM(R.VIA_DIA))
        v.SetLayerPair(pcbnew.F_Cu, pcbnew.B_Cu)
        v.SetNet(nets[net])
        board.Add(v)


def add_outline_and_silk(board):
    corners = [(BX0, BY0), (BX1, BY0), (BX1, BY1), (BX0, BY1)]
    for k in range(4):
        a, b = corners[k], corners[(k + 1) % 4]
        sh = pcbnew.PCB_SHAPE(board)
        sh.SetShape(pcbnew.SHAPE_T_SEGMENT)
        sh.SetStart(V(*a))
        sh.SetEnd(V(*b))
        sh.SetLayer(pcbnew.Edge_Cuts)
        sh.SetWidth(MM(0.1))
        board.Add(sh)
    anchors = []
    for (txt, x, y, rot, size, lock) in SILK:
        t = pcbnew.PCB_TEXT(board)
        t.SetText(txt)
        t.SetPosition(V(x, y))
        t.SetLayer(pcbnew.F_SilkS)
        t.SetTextSize(pcbnew.VECTOR2I(MM(size), MM(size)))
        # The 0.15 ratio is KiCad's own stroke-to-height convention and the
        # nameplate rows depend on it, but the floor underneath it has to be
        # the fab's, not a round number: at the 0.8 mm size most of the SILK
        # table uses, size * 0.15 is 0.12 mm - well under JLCPCB's 0.153 mm
        # legend minimum, and the old 0.1 mm floor was lower still, so it
        # never bit. Clamping at SILK_MIN_STROKE leaves every row above
        # 1.0 mm untouched (they already derive more than the floor) and
        # lifts only the small legends that were under it.
        t.SetTextThickness(MM(max(SILK_MIN_STROKE, size * 0.15)))
        t.SetTextAngleDegrees(rot)
        board.Add(t)
        anchors.append((t, x, y, lock))
    # Silk graphics are placed, not anchored, so none of these go into
    # `anchors`: `silk.place()` has nothing to move them to. It does have to
    # SEE them - board-level F.SilkS drawings are in its obstacle set for
    # exactly this reason, or the nameplate's flame would be the one thing on
    # the board a reference designator could legally print through.
    for pts, width in SILK_GRAPHICS:
        sh = pcbnew.PCB_SHAPE(board)
        sh.SetShape(pcbnew.SHAPE_T_POLY)
        sh.SetLayer(pcbnew.F_SilkS)
        sh.SetPolyPoints([V(x, y) for x, y in pts])
        sh.SetFilled(False)
        sh.SetWidth(MM(width))
        board.Add(sh)
    return anchors


def usb_keepout(board):
    """(x0, y0, x1, y1) of the outer-layer copper keepout around the USB pair:
    the bounding box of every USB_DP/USB_DN track on the board, grown by
    USB_KEEPOUT_MARGIN.

    Read off the board rather than typed, so it follows the pair on both
    paths - the full build has just drawn the tracks, --no-route has just
    loaded them - and cannot go stale the way the measured constant it
    replaces did. Asserts the box stays east of U2_POUR: a keepout reaching
    into that pour does not fail anything, it just stops the AMS1117's
    thermal copper from filling.
    """
    names = set(USB_DIFF_PAIR)
    xs, ys = [], []
    for t in board.GetTracks():
        if t.Type() != pcbnew.PCB_TRACE_T or t.GetNetname() not in names:
            continue
        for v in (t.GetStart(), t.GetEnd()):
            xs.append(pcbnew.ToMM(v.x))
            ys.append(pcbnew.ToMM(v.y))
    assert xs, "usb_keepout: no %s tracks on the board" % "/".join(sorted(names))
    m = USB_KEEPOUT_MARGIN
    box = (min(xs) - m, min(ys) - m, max(xs) + m, max(ys) + m)
    assert box[0] >= U2_POUR[2], (
        "USB keepout reaches x %.2f, into U2_POUR (ends at x %.2f): the pair "
        "has moved west and the AMS1117's thermal pour would silently stop "
        "filling" % (box[0], U2_POUR[2]))
    return box


def add_zones(board, nets):
    """The two inner planes, plus a GND pour on each outer layer.

    The outer pours are a late addition and the reasoning that kept them off
    is worth keeping, because it was right at the time. Rev A poured GND on
    both signal layers; on rev B's density that was the single largest
    consumer of routing space on exactly the two layers the boxed-in signals
    needed to escape through, so the 4-layer respin dropped them and gave the
    outer layers to signals alone.

    What changed is that the routing is now DONE. These zones are added after
    every track and via exists, so they flood what is left rather than
    competing for it - the objection was about the router's freedom, and the
    router has already had it. What they buy back is everything a pour buys
    that a buried plane does not:

      * U7's exposed pad is now embedded in F.Cu ground rather than sitting
        on bare laminate with one 0.25 mm stub to one via. Measured: the pour
        merges with the pad.
      * The 3.58 MHz crystal gets local ground - 1.30 and 2.35 mm from its
        two pins. The ADE7953's layout section (Rev C p.67) asks for "a
        ground plane surrounding as much as possible the through hole crystal
        pins", and a board with bare laminate on both outer layers had none
        at all. It does not shorten the 40 mm oscillator loop, which is a
        placement problem and stays open.
      * Copper balance, which is the big one. F.Cu carried ~2% coverage
        against ~90% on both inner layers; it is now 50.9% and B.Cu 73.8%.
        That asymmetry is what warps a 1.6 mm press.

    It does NOT help U2, and the tempting claim that it would is wrong: the
    SOT-223 tab is +3V3 and this is a GND pour, so the nearest poured copper
    stops 1.47 mm away across a clearance gap and conducts nothing. U2's
    thermal path was fixed by giving its tab four plane vias instead of one
    (_extra_plane_vias in gen_pcb.py); pouring +3V3 locally around the tab
    would add to that, and is a separate change.

    USB is held off by geometry, not by a clearance number. gen_pcb.STACKUP's
    comment is explicit that a flood at the default clearance turns the pair
    into coplanar waveguide and drags it from 93.1 to ~79 ohm, outside
    JLCPCB's +-10% window, and that any pour must stay >= 0.5 mm clear. A
    clearance setting would satisfy that letter while leaving the coupling
    question live - at 0.5 mm against a 0.2104 mm dielectric the gap is only
    2.4 dielectric heights, which is not obviously far enough to ignore. So
    instead a rule area keeps copper out of the pair's neighbourhood
    altogether: the 93.1 ohm figure is a microstrip-over-In1.Cu calculation,
    and it stays valid because there is no outer copper near the pair to
    invalidate it. The box is usb_keepout(): the pair's track bounding box
    plus USB_KEEPOUT_MARGIN, derived from the board every build.
    """
    m = 0.5
    corners = [(BX0 + m, BY0 + m), (BX1 - m, BY0 + m),
               (BX1 - m, BY1 - m), (BX0 + m, BY1 - m)]

    def _pour(layer, netname):
        z = pcbnew.ZONE(board)
        z.SetLayer(layer)
        z.SetNet(nets[netname])
        ol = z.Outline()
        ol.NewOutline()
        for (x, y) in corners:
            ol.Append(MM(x), MM(y))
        z.SetLocalClearance(MM(0.3))
        z.SetMinThickness(MM(0.2))
        z.SetThermalReliefGap(MM(0.3))
        z.SetThermalReliefSpokeWidth(MM(0.4))
        z.SetPadConnection(pcbnew.ZONE_CONNECTION_THERMAL)
        board.Add(z)
        return z

    for netname, layername in sorted(PLANE_LAYER.items()):
        _pour(PLANE_CU[layername], netname)

    for layer in (pcbnew.F_Cu, pcbnew.B_Cu):
        z = _pour(layer, "GND")
        # min_thickness stays at _pour's 0.2 mm. 0.25 was tried, to sever the
        # 0.116 mm neck that moving H1 west (review A1) left in the NW corner
        # puddle, and it is a strictly worse trade: it severed the B.Cu pour
        # near J5 too, isolating a puddle that J5 pad 2 then thermal-connected
        # to with one spoke. That is a `starved_thermal` ERROR in place of a
        # `connection_width` WARNING on a corner sliver of ground that carries
        # nothing. If the neck is ever worth removing, do it by moving copper
        # near H1, not by raising the floor for the whole board.
        # An inner plane is one sheet and any island is a defect worth
        # reporting (plane_islands does). An outer pour is the opposite: it
        # is *expected* to leave puddles trapped between traces, and a puddle
        # touching no pad is unconnected copper - an antenna, and a DRC
        # island. Drop them rather than ship them.
        z.SetIslandRemovalMode(pcbnew.ISLAND_REMOVAL_MODE_ALWAYS)

    # Local +3V3 flood around U2, the one place a GND pour cannot help. Three
    # things about it are deliberate:
    #
    # Priority 1, above the GND pour's 0, or the board-wide zone would fill
    # this area first and leave the tab with the same clearance gap it has now.
    #
    # ZONE_CONNECTION_FULL, not THERMAL. Thermal relief exists to make a pad
    # hand-solderable by RESTRICTING heat flow into the copper, which is the
    # exact opposite of what a heat path wants. Everything this zone touches
    # (U2's tab, its pin-2 pad) is reflow-soldered, so there is no reason to
    # pay the spokes. This is also why it is a separate zone rather than a
    # net change on the big one: the pad connection differs.
    #
    # F.Cu only. The tab is on the front, and B.Cu under U2 is more useful as
    # continuous ground.
    z = pcbnew.ZONE(board)
    z.SetLayer(pcbnew.F_Cu)
    z.SetNet(nets["+3V3"])
    ol = z.Outline()
    ol.NewOutline()
    x0, y0, x1, y1 = U2_POUR
    for (x, y) in [(x0, y0), (x1, y0), (x1, y1), (x0, y1)]:
        ol.Append(MM(x), MM(y))
    z.SetLocalClearance(MM(0.3))
    z.SetMinThickness(MM(0.2))
    z.SetPadConnection(pcbnew.ZONE_CONNECTION_FULL)
    z.SetAssignedPriority(1)
    z.SetIslandRemovalMode(pcbnew.ISLAND_REMOVAL_MODE_ALWAYS)
    board.Add(z)

    # Copper-free box around the USB pair; see the docstring for why this is
    # geometry rather than a clearance. Outer layers only - the pair is a
    # microstrip referenced to the In1.Cu GND plane, so that plane must stay
    # whole underneath it. Cutting In1 here would remove the very reference
    # the 93.1 ohm figure is computed against.
    ka = pcbnew.ZONE(board)
    ls = pcbnew.LSET()
    ls.addLayer(pcbnew.F_Cu)
    ls.addLayer(pcbnew.B_Cu)
    ka.SetLayerSet(ls)
    ka.SetIsRuleArea(True)
    ka.SetDoNotAllowZoneFills(True)
    ka.SetDoNotAllowTracks(False)
    ka.SetDoNotAllowVias(False)
    ka.SetDoNotAllowPads(False)
    ka.SetDoNotAllowFootprints(False)
    ol = ka.Outline()
    ol.NewOutline()
    x0, y0, x1, y1 = usb_keepout(board)
    for (x, y) in [(x0, y0), (x1, y0), (x1, y1), (x0, y1)]:
        ol.Append(MM(x), MM(y))
    board.Add(ka)

    # Rev B also carved a four-layer pour keepout across the SSR optocoupler
    # row so the planes could not short around the barrier; the optos were
    # reverted to direct low-side MOSFET drive (design.py's SSR block), so
    # that one is gone and both inner planes run whole.


def plane_islands(board):
    """[(layer, area_mm2, x, y), ...] for every plane island beyond the
    largest one on its layer.

    A plane is one sheet of copper only until enough antipads line up to cut
    it. Nothing can bridge a severed island back - there is no second copper
    layer carrying the same net to via across to - so this is a report, not a
    repair: it names the layer and the spot so the fix goes into placement.
    KiCad's own DRC reports the same thing as an unconnected zone, but only
    when a pad happens to sit on the stranded piece.

    INNER layers only. That restriction is the whole meaning of the check: on
    In1/In2 an island is a severed plane and a real defect, while on an outer
    pour it is just a puddle of copper trapped between traces, which is what
    a pour on a routed layer always produces. Reporting those would bury the
    signal it exists to raise - the outer pours generated two B.Cu puddles of
    87 and 75 mm2 on their first build, both perfectly ordinary. Anything the
    outer pours strand with no pad on it is deleted rather than reported, by
    ISLAND_REMOVAL_MODE_ALWAYS in add_zones().
    """
    out = []
    for z in board.Zones():
        if z.GetIsRuleArea():
            continue
        layer = z.GetLayer()
        if layer not in PLANE_CU.values():
            continue
        polys = z.GetFilledPolysList(layer)
        areas = []
        for i in range(polys.OutlineCount()):
            ol = polys.Outline(i)
            bb = ol.BBox()
            areas.append((abs(ol.Area()) / 1e12,
                          pcbnew.ToMM(bb.GetCenter().x),
                          pcbnew.ToMM(bb.GetCenter().y)))
        for (area, cx, cy) in sorted(areas, reverse=True)[1:]:
            out.append((board.GetLayerName(layer), area, cx, cy))
    return out


def summarize(rpt_path):
    import re
    report = open(rpt_path).read()
    counts = dict(re.findall(r"\*\* Found (\d+) (\w[\w ]*?) \*\*", report))
    for key, v in counts.items():
        print("  %s: %s" % (v, key.strip()) if False else "  %s: %s" % (key.strip(), v))
    return counts


# Sentinel rule appended to a throwaway copy of the .kicad_dru by
# verify_dru_loaded(). It has to be a constraint no real board can satisfy, so
# that silence means "file dropped" and never "board happens to comply".
DRU_SENTINEL_NAME = "SELF-TEST: rules file loaded"
DRU_SENTINEL = ('\n(rule "%s"\n\t(constraint track_width (min 5mm)))\n'
                % DRU_SENTINEL_NAME)


def verify_dru_loaded(out):
    """Prove KiCad actually READ the .kicad_dru, rather than assume it.

    A .kicad_dru KiCad cannot parse is discarded IN FULL and WITHOUT A
    MESSAGE. The one that happened here (FAB-READINESS-REVIEW-REVB.md A11)
    was a `(condition "...")` string broken across two lines; the cost was
    that every `kicad-cli pcb drc` pass for the life of the file checked none
    of JLC's limits and said so in the only way it can - by reporting a clean
    board. That is indistinguishable from success, which is exactly why it
    survived: 0 violations is what passing looks like.

    So the load is asserted positively instead. Copy the board, its project
    and the rules to a scratch directory, append a rule that CANNOT hold on
    any real board (every track at least 5 mm wide), and require it to fire.
    A silent sentinel means the rules file was dropped. Returns None on
    success, or a message describing the failure.
    """
    dru = os.path.splitext(out)[0] + ".kicad_dru"
    if not os.path.exists(dru):
        return None          # no sidecar is a choice, not a defect
    pro = os.path.splitext(out)[0] + ".kicad_pro"
    with tempfile.TemporaryDirectory() as tmp:
        base = os.path.basename(os.path.splitext(out)[0])
        shutil.copy(out, os.path.join(tmp, base + ".kicad_pcb"))
        if os.path.exists(pro):
            shutil.copy(pro, os.path.join(tmp, base + ".kicad_pro"))
        # The rules KiCad will be asked to load, plus the sentinel.
        with open(os.path.join(tmp, base + ".kicad_dru"), "w") as fh:
            fh.write(open(dru).read() + DRU_SENTINEL)
        rpt = os.path.join(tmp, "selftest.rpt")
        # No --refill-zones and no --save-board: this pass exists to find out
        # whether a file parsed, not to check or rewrite anything.
        subprocess.run(["kicad-cli", "pcb", "drc", "--format", "report",
                        "--severity-error", "-o", rpt,
                        os.path.join(tmp, base + ".kicad_pcb")],
                       check=True, capture_output=True)
        hits = open(rpt).read().count(DRU_SENTINEL_NAME)
    if hits:
        print("  %s: loaded (self-test rule fired %d\u00d7)"
              % (os.path.basename(dru), hits))
        return None
    return ("%s was IGNORED by KiCad - the whole file, silently. Every JLC "
            "limit in it went unchecked and the DRC report above is "
            "meaningless. Almost always a syntax error: a quoted string "
            "spanning two lines, an unbalanced paren, an unknown token. "
            "kicad-cli names neither the file nor the line, so bisect it by "
            "deleting rules until the self-test fires."
            % os.path.basename(dru))


def build_copper(board, fps, order):
    """One complete routing attempt. Returns (router, failed-net list)."""
    r, pad_pos = build_router_model(board, fps)
    seed_list, stub_terms = all_seeds(pad_pos)
    for (net, layer, pts, w) in seed_list:
        for a, b in zip(pts, pts[1:]):
            r.add_seg(net, layer, a[0], a[1], b[0], b[1], w, fixed=True)
    for (net, x, y) in MANUAL_VIAS:
        r.add_via(net, x, y, fixed=True)
    for (net, x, y) in STITCH_VIAS:
        r.add_via(net, x, y, fixed=True)
    for (x, y, net) in ep_via_positions(fps):
        r.add_via(net, x, y, fixed=True)
    # The USB pair before anything else, plane vias included. It is the one
    # impedance-controlled object on the board and the only one whose two
    # tracks have to stay side by side, so it gets the board while the board
    # is empty; everything after it is routed around it. Routed as one
    # object (router.route_pair) and marked fixed, so no later net and no
    # rip-up can move it. A failure here is a placement problem, not an
    # ordering one, and stops the build.
    pair = route_usb_pair(r, pad_pos)
    a, b = USB_DIFF_PAIR
    la, lb = (sum(math.hypot(q[0] - p[0], q[1] - p[1])
                  for p, q in zip(pair[n], pair[n][1:])) for n in (a, b))
    print("  USB pair: %s %.2f mm, %s %.2f mm, skew %.2f mm, F.Cu, no vias"
          % (a, la, b, lb, abs(la - lb)))
    # Plane vias next: they are not optional (a missing one is an unconnected
    # pad) and they are short, so they claim their spots while the board is
    # still nearly empty and the signal router threads what is left.
    pv, pv_fail = plane_vias(r, pad_pos, seed_list)
    print("  plane vias: %d (%d unplaceable)" % (len(pv), len(pv_fail)))
    failed = route_all(r, pad_pos, seed_list, stub_terms, order=order,
                       verbose=False)
    if failed:
        failed = ripup_retry(r, failed, pad_pos, stub_terms)
    failed = failed + pv_fail
    r._memo = {}
    r._memo_net = None
    print("  mitred %d right-angle corners" % r.miter_corners())
    return r, failed


def route_board(board, fps, passes=6):
    """Route, promoting whatever failed and trying again.

    router.py is greedy and never rips up, so a failed net failed because
    something routed earlier took the one lane out of its pocket. Re-running
    with the failures at the head of the order is the cheapest rip-up
    available: the blocking net gets re-routed around them, and being the
    longer of the two it usually has somewhere else to go. Iterate until
    nothing fails or the failure set stops shrinking, and keep the best
    attempt - promotion can trade one failure for another, and the loop must
    not end on a worse board than it has already seen.
    """
    promoted = []
    best = None
    seen = []
    for attempt in range(passes):
        order = promoted_order(promoted) if promoted else None
        print("routing pass %d (%d promoted)..." % (attempt + 1, len(promoted)))
        r, failed = build_copper(board, fps, order)
        print("  pass %d: %d net(s) unrouted%s"
              % (attempt + 1, len(failed),
                 (": " + ", ".join(failed)) if failed else ""))
        if best is None or len(failed) < len(best[1]):
            best = (r, failed)
        if not failed:
            break
        if frozenset(failed) in seen:
            break                      # the same answer again: a cycle
        seen.append(frozenset(failed))
        # This pass's failures go to the FRONT, ahead of everything promoted
        # before them. Appending them behind is what this used to do, and
        # it is wrong for the case that actually recurs: a net promoted in
        # pass N fails in pass N+1 because a net promoted in the same batch
        # - routed just ahead of it - took its lane (CTA_N lost D6.3 to
        # CTB_N that way and the loop then declared the promotion had
        # "stopped helping", with the answer one position away). A net that
        # failed while promoted has to move ahead of whoever beat it; a net
        # that no longer fails keeps its place behind.
        promoted = failed + [n for n in promoted if n not in failed]
    return best


def verify_reusable(board):
    """Refuse `--no-route` when design.py and the loaded board have drifted.

    The fast path is only sound while the copper it inherits is the copper a
    full build would produce. Nothing here can prove that outright, but every
    input the router reads out of design.py *can* be compared against what the
    board actually has, and a mismatch on any of them means the inherited
    routing belongs to a different design. A stale fast path that quietly
    emits a plausible-but-wrong board is worse than no fast path at all, so
    this exits rather than warns.

    Deliberately not checked: `value` and the SILK text table, both of which
    the fast path genuinely re-derives, and router.py's own parameters, which
    are not recorded on the board. Changing those needs the full path and the
    docs say so.
    """
    bad = []
    seen = {}
    for fp in board.GetFootprints():
        seen.setdefault(fp.GetReference(), []).append(fp)
    for ref in sorted(r for r, v in seen.items() if len(v) > 1):
        bad.append("%s: %d footprints share this reference" % (ref, len(seen[ref])))
    for ref in sorted(set(COMPONENTS) - set(seen)):
        bad.append("%s: in design.py, absent from the board" % ref)
    for ref in sorted(set(seen) - set(COMPONENTS)):
        bad.append("%s: on the board, absent from design.py" % ref)

    for ref in sorted(set(COMPONENTS) & set(seen)):
        c = COMPONENTS[ref]
        fp = seen[ref][0]
        # The board's footprints were loaded through the plugin directly, so
        # they carry the bare footprint name with no library nickname.
        want_fp = c["fp"].split(":", 1)[1]
        if fp.GetFPID().GetUniStringLibItemName() != want_fp:
            bad.append("%s: footprint is %s, design.py says %s"
                       % (ref, fp.GetFPID().GetUniStringLibItemName(), want_fp))
        x, y, rot = c["at"]
        p = fp.GetPosition()
        if abs(pcbnew.ToMM(p.x) - x) > 1e-4 or abs(pcbnew.ToMM(p.y) - y) > 1e-4:
            bad.append("%s: at (%.3f, %.3f), design.py says (%.3f, %.3f)"
                       % (ref, pcbnew.ToMM(p.x), pcbnew.ToMM(p.y), x, y))
        if abs((fp.GetOrientationDegrees() - rot + 180.0) % 360.0 - 180.0) > 1e-4:
            bad.append("%s: rotated %.2f deg, design.py says %.2f"
                       % (ref, fp.GetOrientationDegrees(), rot))
        for pad in fp.Pads():
            num = str(pad.GetNumber())
            want = c["pins"].get(num)
            have = pad.GetNetname()
            if want and have != want:
                bad.append("%s pad %s: net %s, design.py says %s"
                           % (ref, num, have or "<none>", want))

    have_nets = set(str(k) for k in board.GetNetsByName().keys()) - {""}
    want_nets = set(netlist())
    for n in sorted(want_nets - have_nets):
        bad.append("net %s: in design.py, absent from the board" % n)
    for n in sorted(have_nets - want_nets):
        bad.append("net %s: on the board, absent from design.py" % n)

    # MANUAL_VIAS are hand-placed copper, so an edit to that table is a
    # copper edit even though it lives beside the cosmetic tables.
    vias = set()
    for t in board.GetTracks():
        if t.Type() == pcbnew.PCB_VIA_T:
            vias.add((t.GetNetname(), round(pcbnew.ToMM(t.GetPosition().x), 3),
                      round(pcbnew.ToMM(t.GetPosition().y), 3)))
    for (net, x, y) in MANUAL_VIAS:
        if (net, round(x, 3), round(y, 3)) not in vias:
            bad.append("MANUAL_VIAS %s at (%.3f, %.3f): no such via on the board"
                       % (net, x, y))

    if bad:
        sys.stderr.write(
            "--no-route refused: the loaded board is not this design.\n"
            "%d mismatch(es); the first few:\n" % len(bad))
        for line in bad[:12]:
            sys.stderr.write("  %s\n" % line)
        if len(bad) > 12:
            sys.stderr.write("  ... and %d more\n" % (len(bad) - 12))
        sys.exit("Run a full build (make pcb-build) - this change moves copper.")


_REMOVED = []


def strip_derived(board):
    """Delete everything `--no-route` re-derives; keep the routing.

    Footprints and board graphics are removed outright rather than edited
    back to a default state. `silk.place()` has already moved every reference
    designator and every board text on the loaded board, so re-running the
    placer over it would be scoring its own previous output instead of the
    inputs a fresh build gives it. Re-adding the library footprints is the
    only reset that is exactly the fresh build's starting state, because it
    *is* it - and it resets the 3D-model list and the reference text metrics
    for free, which a hand-written reset would have to remember to do.

    Tracks, vias and the two filled zones stay: they are the routing result,
    and they are the whole point.
    """
    # Both lists are taken before anything is removed: the swig wrappers over
    # BOARD's item containers do not survive a mutation of a sibling
    # container, and iterating Drawings() after the footprints have gone
    # raises rather than returning the drawings.
    doomed = list(board.GetFootprints()) + list(board.GetDrawings())
    for item in doomed:
        board.Remove(item)
    # And the proxies are parked in a module-level list rather than dropped.
    # A BOARD_ITEM the board no longer owns has no destructor swig can find,
    # and collecting one does not merely leak it - it corrupts pcbnew's shared
    # swig type table, after which EVERY later call returns an untyped
    # SwigPyObject. The first symptom is FootprintLoad() handing back
    # something with no SetReference() on it, ~150 lines away from the Remove
    # that caused it. Holding the references costs a few MB for one run.
    _REMOVED.extend(doomed)


def apply_layer_types(board):
    """Set copper layer types on a loaded board from gen_pcb.COPPER_LAYER_TYPE.

    gen_pcb writes these into the board text it emits, and that is not enough:
    pcbnew builds its own layer table when it loads a board and writes THAT
    back out, so the types in the input text never reach disk. This runs on
    both paths - full and --no-route - because the fast path loads a saved
    board and would otherwise carry forward whatever types it already had,
    exactly as apply_stackup() has to re-impose the stack-up for the same
    reason.

    Unlike BOARD_STACKUP, this one KiCad 10 does wrap, so it is set through the
    API rather than patched into the text afterwards.
    """
    kinds = {"signal": pcbnew.LT_SIGNAL, "power": pcbnew.LT_POWER,
             "mixed": pcbnew.LT_MIXED, "jumper": pcbnew.LT_JUMPER}
    for name, kind in COPPER_LAYER_TYPE.items():
        lid = board.GetLayerID(name)
        if lid < 0:
            raise SystemExit("kicad_build: no layer %r on the board" % name)
        board.SetLayerType(lid, kinds[kind])


def read_project(out):
    """Snapshot the sibling .kicad_pro/.kicad_prl before anything writes a board.

    Every tool here attaches the project to the board it saves and writes it
    back out from the PCB side alone, dropping whatever it never loaded. The
    known casualty used to be `schematic.top_level_sheets`, which sync_project()
    puts back - but it is not the only one: a full build also took out the whole
    `erc` block and `sch_revision`, because build_board() starts from a bare
    pcbnew.BOARD() with an empty project attached. Nothing noticed, since the
    two repairs downstream only rebuild the blocks THEY own.

    So snapshot the bytes instead of enumerating what might go missing, and put
    them back once the last write is done. sync_project()/sync_netclasses()
    still run afterwards and are idempotent, so the derived blocks stay derived
    and the hand-authored ones stop being collateral. The fast path never needed
    this - LoadBoard() attaches the real project - and the restore is a no-op
    there.
    """
    stem = os.path.splitext(out)[0]
    return {f: open(f, "rb").read()
            for f in (stem + ".kicad_pro", stem + ".kicad_prl")
            if os.path.exists(f)}


def restore_project(saved):
    for f, blob in saved.items():
        if os.path.exists(f) and open(f, "rb").read() != blob:
            with open(f, "wb") as fh:
                fh.write(blob)
            print("  %s: restored blocks the board save dropped"
                  % os.path.basename(f))


def resort_to_kicad_order(path):
    """Leave the board in the order KiCad's own writer produces.

    KiCad orders board items by uuid - footprints outright, tracks and vias as
    the tie-break after position - so with every uuid derived (canonicalize.py)
    that order is a function of the design, and putting the file in it is what
    makes opening the board in the GUI and saving it a no-op instead of a
    61,654-line reorder.

    Two things about this are easy to get wrong, and both were, here:

    `kicad-cli pcb drc --save-board` is NOT the tool for it. It writes items
    back in the order it read them, so it will happily preserve
    canonicalize.py's content order and report byte-identical output - which
    makes it useless as a stand-in for a GUI save, and it was believed to be
    one for a while. `pcb upgrade --force` does sort.

    One pass is not enough. KiCad's sort leaves ties in load order, so a file
    arriving in a foreign order needs a second pass to settle; measured on this
    board, pass 1 and pass 2 differ by 16,860 lines and pass 2 and pass 3 by
    none. Loop to the fixpoint rather than assuming a count, and fail loudly if
    it does not converge - an oscillation would mean the writer has no fixpoint
    at all, and every one of these files would churn forever.
    """
    for i in range(5):
        before = open(path, "rb").read()
        subprocess.run(["kicad-cli", "pcb", "upgrade", "--force", path],
                       check=True, capture_output=True)
        if open(path, "rb").read() == before:
            print("  re-sorted into KiCad's own item order (%d pass(es))" % (i + 1))
            return i
    sys.exit("kicad-cli pcb upgrade --force never settled on an order for %s; "
             "KiCad's writer has no fixpoint here and the board cannot be "
             "stored in it" % path)


def main(out, reuse_routing=False):
    out = os.path.abspath(out)
    # Intermediate snapshots into hardware/kicad/stages/, on every run. Only
    # this writer's numbers are cleared: gen_sch.py owns 0* in the same
    # directory and `make pcb-build` runs it as a separate process first.
    stages.reset(out, "[1-9]*")
    if reuse_routing:
        if not os.path.isfile(out):
            sys.exit("--no-route reuses the routing in %s, and that file does "
                     "not exist.\nRun a full build first: make pcb-build" % out)
        # Canonicalise on the way IN as well as out. The tracks and vias are
        # carried across with the uuids the file gave them, and KiCad's
        # s-expression writer breaks position ties between items with the
        # uuid - so copper the GUI ADDED, carrying a random uuid, would tie
        # against derived ones and land wherever chance put it. Re-deriving
        # here makes every tie a function of the design again. No-op on a
        # board this pipeline wrote, and note the order it produces is not
        # the order the run ends in: the kicad-cli save below has the last
        # word on that, deliberately.
        canonicalize_file(out)
        loaded = pcbnew.LoadBoard(out)
        verify_reusable(loaded)
        n_via = sum(1 for t in loaded.GetTracks() if t.Type() == pcbnew.PCB_VIA_T)
        print("reusing routing from %s: %d tracks, %d vias, %d filled zones"
              % (os.path.basename(out), len(list(loaded.GetTracks())) - n_via,
                 n_via, len(list(loaded.Zones()))))
        strip_derived(loaded)
        stages.board(loaded, out, "10-reused.kicad_pcb")
        board, nets, fps = build_board(loaded)
        stages.board(board, out, "20-placed.kicad_pcb")
    else:
        board, nets, fps = build_board()
        stages.board(board, out, "20-placed.kicad_pcb")
        r, failed = route_board(board, fps)
        if failed:
            print("UNROUTED: %s" % ", ".join(failed))
        add_copper(board, nets, r)
        stages.board(board, out, "30-routed.kicad_pcb")
    anchors = add_outline_and_silk(board)
    stages.board(board, out, "40-outline.kicad_pcb")
    # Silk placement runs last, once every pad, footprint outline and board
    # text exists: it is a whole-board packing problem, and it cannot be
    # solved a label at a time as each one is created.
    _labels = silk.place(board, anchors)
    stages.board(board, out, "50-silk.kicad_pcb")
    strayed, slid = silk.adrift(_labels), silk.offaxis(_labels)
    intruding = silk.in_legend_column(_labels, TP_LABEL_TEXTS, LEGEND_OWNER)
    if not reuse_routing:
        add_zones(board, nets)
        stages.board(board, out, "60-zones.kicad_pcb")
    rpt_path = os.path.splitext(out)[0] + "-drc.rpt"
    # standalone python fill/DRC needs a project-attached board; kicad-cli
    # fills, saves and checks in one authentic pass.
    board.SetFileName(out)
    # Copper layer types, which unlike the stack-up pcbnew DOES wrap - but it
    # rewrites the layer table from its own model on save, so the types
    # gen_pcb wrote into the input text are gone by the time the file lands.
    # Set on the board object, before the save that would otherwise drop them.
    apply_layer_types(board)
    project_before = read_project(out)
    pcbnew.SaveBoard(out, board)
    # The physical stack-up, which pcbnew cannot be asked to set: KiCad 10's
    # SWIG bindings do not wrap BOARD_STACKUP, so gen_pcb.STACKUP is written
    # into the saved file instead. Here rather than after the DRC pass, so
    # that on the full path kicad-cli parses the block and writes it back out
    # itself - a stack-up KiCad rejected fails the build rather than reaching
    # the fab. The fast path has nothing dirty to save, so it keeps these
    # bytes verbatim; that is why gen_pcb.stackup_sexp() emits KiCad's own
    # formatting rather than leaving it to the round trip.
    apply_stackup(out)
    stages.copy(out, out, "70-stackup.kicad_pcb")
    # Fix the uuids BEFORE the last KiCad write, and let KiCad do the sorting.
    # pcbnew hands each item a random uuid and then orders the file by it, so
    # without this an unchanged design lands on disk differently every run
    # (#234); with it, KiCad's own comparators - which key on the uuid, either
    # outright (footprints) or as the tie-break (tracks, vias) - become a
    # deterministic function of the design. The board therefore leaves this
    # pipeline in the order KiCad itself would write, which is the whole point:
    # opening it in the GUI and saving is a no-op instead of a 61k-line reorder.
    # Running before *each* write, not just once at the end, also matters
    # because the zone fill is only reproducible if kicad-cli is handed a
    # reproducible board.
    canonicalize_file(out)
    # --refill-zones is not merely unnecessary on the fast path, it is WRONG.
    # KiCad's filler is idempotent once a zone is filled, but filling an
    # unfilled zone and refilling an already-filled one do not agree: refilling
    # this board's +3V3 pour rewrites ~180 lines of its filled_polygon. The
    # full path fills from empty; the fast path inherits that fill and must
    # leave it exactly alone, or byte-identity is lost on the pour rather than
    # on anything to do with silk. Skipping it is also ~0.8 s cheaper.
    drc = ["kicad-cli", "pcb", "drc"]
    if not reuse_routing:
        drc.append("--refill-zones")
    drc += ["--save-board", "--severity-all", "--all-track-errors",
            "-o", rpt_path, out]
    print("saved %s (%s); DRC via kicad-cli..."
          % (out, "fill inherited" if reuse_routing else "unfilled"))
    subprocess.run(drc, check=True, capture_output=True)
    stages.copy(out, out, "80-filled.kicad_pcb")
    # Canonicalise once more, then hand it straight back to KiCad so KiCad has
    # the last word on ORDER. Both halves of that are load-bearing, and each
    # was learned by removing it.
    #
    # The second canonicalise is what keeps the two paths agreeing. A uuid is
    # derived from the item's serialised content, and a ZONE's content is its
    # filled_polygon - which does not exist yet when the full path canonicalises
    # above (it fills from empty, here) but does on the fast path (it inherits
    # the fill). Skip this and the five pours get one uuid on `pcb-build` and a
    # different one on `pcb-cosmetic`, breaking pcb-cosmetic-verify on the only
    # five items in the file whose bytes KiCad writes rather than pcbnew.
    # Deriving after the fill is what puts both paths on the same content.
    #
    # The second save is what stops that from re-introducing the churn it was
    # meant to remove. KiCad orders items by uuid (footprints outright, tracks
    # and vias as the position tie-break), so re-deriving uuids leaves the file
    # sorted on the PREVIOUS ones - and the next GUI save would reorder it,
    # which is exactly the 61,654-line diff this arrangement exists to kill.
    # resort_to_kicad_order() sorts it on the uuids it now carries. One extra
    # canonicalise round is enough: that pass only reorders, so a third would
    # derive the same uuids again.
    canonicalize_file(out)
    resort_to_kicad_order(out)
    stages.copy(out, out, "90-final.kicad_pcb")
    restore_project(project_before)
    # Put `schematic.top_level_sheets` back. Saving this board blanked it, and
    # the culprit is `pcbnew.SaveBoard()` above, NOT kicad-cli: a BOARD has a
    # PROJECT attached, saving the board writes that project alongside it, and
    # on the FULL path build_board() hands us a bare `pcbnew.BOARD()` whose
    # project is empty - so the root-sheet block is written out as []. The
    # fast path escapes it because `build_board(loaded)` starts from
    # LoadBoard(), which attaches the real project and carries the block
    # through. Measured both ways on a scratch copy: a fresh BOARD saved next
    # to a populated .kicad_pro empties it; `kicad-cli pcb drc --refill-zones
    # --save-board` over the same file leaves it exactly alone.
    #
    # That last point is worth recording, because 9bcb0bf blamed kicad-cli
    # ("the PCB tooling never loads a schematic") and concluded it "only ever
    # adds the block when missing and preserves a populated one". The
    # conclusion is right and still holds - kicad-cli is innocent here. What
    # the fix missed is that pcbnew's own writer does the damage, and it runs
    # AFTER gen_sch.sync_project(), so on `make pcb` the derived entry was
    # being reverted minutes later and a tracked file ended every full regen
    # silently changed.
    #
    # Re-syncing here, after the last write of the run, is ordering-
    # independent rather than another lap of the tug-of-war. sync_project is
    # idempotent: it returns False and touches nothing when already correct,
    # which is what the fast path reports.
    # Pass the SCHEMATIC path: sync_project derives both the .kicad_pro to
    # edit and the `filename` field it records from what it is handed, so
    # giving it `out` would record "bisque-controller.kicad_pcb" as the root
    # sheet - in step with nothing, and worse than the empty list.
    if sync_project(os.path.splitext(out)[0] + ".kicad_sch"):
        print("  root sheet in .kicad_pro: restored after the board save "
              "blanked it")
    # Same story, same remedy: the board save drops every net class but
    # Default and empties netclass_patterns, so the derived table is written
    # back here rather than anywhere earlier in the run.
    if sync_netclasses(os.path.splitext(out)[0] + ".kicad_pro"):
        print("  net classes in .kicad_pro: %d class(es) written"
              % (len(netclass_table()) + 1))
    # Last, once the .kicad_pro is finished: a stage board opened without one
    # gets KiCad's defaults - no net classes, no custom DRC rules - and then
    # reports violations the real board does not, which is the opposite of a
    # debugging aid.
    print("  stages -> %s/ (%d project file(s) attached)"
          % (stages.DIRNAME, stages.attach_projects(out)))
    for (lname, area, cx, cy) in plane_islands(pcbnew.LoadBoard(out)):
        print("  !! %s plane island of %.1f mm2 stranded at (%.1f, %.1f)"
              % (lname, area, cx, cy))
    print("KiCad DRC report -> %s" % rpt_path)
    summarize(rpt_path)
    dru_fail = verify_dru_loaded(out)
    # Last, and after the board is on disk: a label that had to travel is not
    # a reason to withhold the artefact you need in order to see why. It is a
    # reason not to ship it. `silk.RING_MAX` is a bound on how far a legend
    # may be moved from where it was authored before it stops describing what
    # it was pointed at - `CT A+/A-/B+/B-` once slid 14 mm onto a different
    # terminal block - and no amount of placer cleverness fixes an anchor
    # aimed at occupied board. That is a human's call, so it stops the build.
    for txt, d in strayed:
        print("FAIL: board text %r moved %.2f mm from its anchor "
              "(silk.RING_MAX = %.1f) - move the anchor in gen_pcb.SILK, "
              "or the parts crowding it" % (txt, d, silk.RING_MAX))
    # The same judgement, one class up in severity. A legend that had to leave
    # the axis identifying its terminal is not merely far from what it
    # describes, it is beside something else - `A-` printed level with the B+
    # screw is worse than no legend at all, because a reader acts on it. The
    # fix is never in silk.py: give the legend column room (see gen_pcb.
    # PIN_LEGENDS and TP11, which was moved out of J12's).
    for txt, axis, d in slid:
        print("FAIL: terminal legend %r moved %.2f mm along its locked %s "
              "axis - it names a different terminal now. Clear the legend "
              "column in gen_pcb.PIN_LEGENDS, or move the part in the way."
              % (txt, d, axis))
    # A test point's label is free to sit anywhere; a terminal legend is not.
    # When the free one lands in the locked ones' column nothing in the placer
    # can resolve it, and the block ends up with two names for one screw.
    for txt, owner, d in intruding:
        if (txt, owner) in TP_LEGEND_OK:
            print("  (known) test-point label %r sits in %s's legend column "
                  "(overlap %.2f mm) - see gen_pcb.TP_LEGEND_OK" % (txt, owner, d))
            continue
        print("FAIL: test-point label %r prints inside %s's terminal legend "
              "column (overlap %.2f mm) - a reader takes it for one of that "
              "block's screw marks. Move the TEST POINT (design.py), not the "
              "label: the legends are axis-locked and cannot step aside."
              % (txt, owner, d))
    if dru_fail:
        print("FAIL: %s" % dru_fail)
    intruding = [t for t in intruding if (t[0], t[1]) not in TP_LEGEND_OK]
    if strayed or slid or intruding or dru_fail:
        sys.exit(1)


if __name__ == "__main__":
    argv = sys.argv[1:]
    reuse = False
    paths = []
    for a in argv:
        if a == "--no-route":
            reuse = True
        elif a.startswith("-"):
            sys.exit("unknown option %s (usage: kicad_build.py [--no-route] "
                     "<out.kicad_pcb>)" % a)
        else:
            paths.append(a)
    main(paths[0] if paths else "bisque-controller.kicad_pcb",
         reuse_routing=reuse)
