BenSeverson/bisque/hardware/kicad/generator/design.py

"""Bisque kiln controller PCB — single source of truth.

Components, pin->net connectivity, and PCB placement. Both the schematic and
board generators derive everything from these tables, so the two files can
never disagree on connectivity.

Pin GPIO mapping mirrors main/Kconfig.projbuild defaults (the firmware's
source of truth). This is the rev B map — see docs/pin-assignments.md §1 for
the full as-built table with module pin numbers and net names:
  SPI: MOSI=11 MISO=13 SCLK=12 | TC1 CS=10 TC2 CS=35 | SSR1=17 SSR2=21
  LCD: CS=8 DC=9 RST=46 BL=3   | WS2812=48 | ALARM=7
  BTN: UP=38 DOWN=39 SEL=42 LEFT=40 RIGHT=41 (moved off ADC1 in Task 3)
  AUX bank (U6, ULN2003): AUX1(vent)=14 AUX2=15 AUX3=16, on terminal J10
    with the external AUX_VP coil rail (SJ1 links it to +5V).
  Touch (Task 11): T_CS=5 T_IRQ=6 — dedicated GPIOs; T_CLK/T_DIN/T_DO are the
    shared SPI2 bus (SPI_SCLK/SPI_MOSI/SPI_MISO) through series resistors.
  I2C: SDA=18 SCL=47 — shared bus, pulled up on-board, broken out on
    both J7 (0.1") and J14 (Qwiic/STEMMA QT).
  Watchdog: WDT_KICK=36 retriggers the U10 one-shot; its Q holds Q3 on, Q3
    holds SSR_PG down, which turns on the high-side switch Q4 supplying
    SSR_EN. SSR_EN is a +5V GATE-DRIVE rail, not the terminal supply: it
    feeds both opto collectors and Q7's gate, so losing it opens both
    channels two independent ways. SJ2 ("WDT DEFEAT") shorts SSR_PG to GND,
    defeating the watchdog - leave it open on boards that carry U10.
  J11: IN1(lid)=4 IN2(gas flow)=2 IN3(spare)=1
  SSR drive: 24 V terminals fed from VIN_P (always live), switched on the low
    side by a CJ2310 per channel (Q5/Q6) whose gate is driven through an
    optocoupler (U8/U9), with Q7 in the shared return as the watchdog gate.
    The optos are CONTAINMENT, not isolation - rev B's opto-ISOLATED version
    was reverted and that reasoning still stands. See the SSR block below.
  Power path: J2 -> F1 -> D8 (clamp) -> Q8 (reverse polarity, a P-FET and no
    longer a diode) = VIN_P, which feeds the buck AND both SSR terminals.
    U11 makes BUCK_5V; U12 selects between BUCK_5V and USB VBUS to make +5V,
    in PRIORITY mode so the buck wins over a higher USB port rather than the
    other way round; U2 drops +5V to +3V3. BUCK_5V and +5V are separate nets
    on purpose - C44/C45/C46 belong to the buck's feedback loop and stay on
    its side of the mux. See the Q8 and U12 blocks for both derivations.

J7's pins 5-8 carried VENT/(unconnected)/AUX_A/AUX_B through Task 10, all
either dangling single-pin nets or declared-but-undriven — nothing on this
board actually sourced them (the real VENT output is AUX1, wired to the
ULN2003 aux bank, U6). Task 11 re-points J7 5-8 to I2C_SDA/I2C_SCL/+3V3/GND,
retiring the AUX_A/AUX_B nets for good and giving the I2C bus a 0.1" header
alongside the Qwiic connector (J14). IN1/IN2/IN3 (Task 9) land on their own
terminal, J11, not J7 - rev A's lid switch was the only occupant of J7.6 and
has moved there. Note that an enabled-but-unwired IN1 (lid) reads open and
holds the SSR off - it needs a switch, a jumper to GND, or -1. The full
as-built map, the constraints behind it, and the planned expansion live in
docs/pin-assignments.md — keep that table in sync with this one.
"""

# --- board outline (mm, page coords) ---
# 100 x 100 mm, 4-layer - spec 6.3 rung 3 (measured outcome). The 2-layer
# escalation ladder never closed: 100x100/0805 (rung 0) left 34 nets
# unroutable, 100x100/0603 (rung 1) left 23, and 125x100/0603 (rung 2) left 9
# short local nets boxed in by neighbours' copper in the SSR driver cluster
# and the ADE7953 block - the signature of a layer shortage, not an area
# shortage. Going 4-layer (rung 3: GND plane on In1.Cu, +3V3 plane on In2.Cu)
# closed it at 0 unrouted/0 DRC errors, and then gave back every rung-1/rung-2
# concession: the board walked back to 100 x 100 mm, 0805 passives, and rev
# A's 0.3 mm signal / 0.7-0.8 mm rail widths, staying inside JLCPCB's
# <=100x100 promo tier. Those widths live in gen_pcb.ROUTE_ORDER, and
# gen_pcb.netclass_table() derives the .kicad_pro net classes from that same
# table - for a long time this comment said "net classes" while the project
# file held one Default class at 0.2 mm and no patterns at all.
# See the task 14 report for the DRC counts at each rung.
BX0, BY0, BX1, BY1 = 20.0, 20.0, 120.0, 120.0   # 100 x 100 mm

# Placement regions. DESCRIPTIVE, not enforced - nothing checks a part against
# a band, so this block is only worth what its accuracy is worth. Measured off
# the placement below rather than copied forward from spec §6.2, because the
# spec's version had stopped being true:
#
#   digital    x 20..120  y 20..48   module, USB-C, power in, RESET + BOOT
#   switching  x 20..60   y 48..95   ULN2003, SSR drivers, watchdog, buzzer
#   analog     x 88..120  y 33..92   MAX31856 x2 (north), ADE7953 + CT (south)
#   headers    x 20..120  y 94..120  LCD / nav / aux / I2C, input terminal
#   (unzoned)  x 60..92   y 48..94   buzzer driver, TP4-TP10, status LED,
#                                    the nameplate
#
# Two corrections against §6.2, both found by measuring:
#
# The analog region is a COLUMN spanning y 33..92, not the y 50..92 box the
# spec drew, and it does not "hold both thermocouple cold junctions" in the
# quiet band - U3 sits at y 37.8 and U5 at y 49.8, i.e. the TC front-ends are
# level with the digital band and always were. That is tolerable rather than
# intended: the east end of the digital band holds only R2 and the two
# buttons, so it is quiet in practice, and every low-level terminal (J3, J8,
# J12) still lands on the east edge while every mains-side one (J2, J4, J9,
# J10) lands on the west. That west/east split is the property this floorplan
# is actually built on and it does hold - ~30 mm separates the SSR/ULN2003
# cluster from the front-ends.
#
# The 32 x 46 mm band between the switching column and the analog column
# belongs to no region at all. It is the lowest-density area on the board
# (~1.1 parts/cm2 against 2.30 in the analog column), which is why the
# nameplate search (gen_pcb.largest_empty_rect) keeps landing in it, why the
# WS2812 status cluster moved into it, and also why the ADE7953 block, boxed
# in at 2.30, had to push its crystal 19.5 mm south. If something needs room,
# this band is where the room is.
#
# But do not mistake it for the ONLY room, and above all do not mistake the
# band just south of the module (x 60..88, y 44..56) for room at all. It
# measures emptier than anywhere else on the board and it is the escape path
# for forty castellated pads: putting the status LED there cost SPI_MOSI and
# SPI_SCLK their test-point terminals and left TC1_CS unrouted. Clear board
# beside a big part is not free board.
#
# There is no isolation-barrier region, and U8/U9 coming back in rev B.2 did
# NOT bring one with them. The four-layer pour keepout that used to reserve
# x 20..40.8 / y 71..95.5 belonged to the opto-ISOLATED design, which was
# reverted and stays reverted; the optos are back as a containment part in
# ordinary pour and routing area. See the SSR block below before adding a
# keepout on their account.

# net name -> netclass ("signal" default).
# AUX_VP is an externally supplied coil rail the board does not generate, so
# it may not join the GND/power pour logic. SSR_EN is board +5V switched by
# the watchdog's high-side MOSFET - a driven rail, but a gated one, so it is
# deliberately not a pour net either.
POWER_NETS = {"GND", "+5V", "+3V3", "VBUS", "VIN", "VLED"}

# ---------------------------------------------------------------------------
# Components
# ---------------------------------------------------------------------------
# ref: (lib, symbol, fp_lib_id, fp_file, value, (pcb_x, pcb_y, rot), {pin: net})
# net None => explicit no-connect

# Chip passives are 0805, same as rev A (spec 6.3 rung 3, walked back from
# the 0603 the 2-layer escalation ladder tried at rungs 1-2). Rev B put 2.7x
# rev A's part count on the same 100x100 area; on 2 layers even 0603 at
# 125x100 left nine nets unroutable, and going 4-layer closed the board
# without needing the smaller passives at all - see the task 14 report for
# the DRC numbers at each rung. 0603 and 0805 are both JLCPCB *Basic* sizes,
# so the walkback cost no feeder fee and no assembly tier. The names below
# (R0603/C0603) are historical from the rung-1 attempt; the footprints they
# point to are 0805. The 22 uF/25 V bulk capacitors stay 1206 - that
# value/voltage is not a Basic part in 0603 or 0805, and neither sits in a
# congested area.
R0603 = ("Resistor_SMD:R_0805_2012Metric", "R_0805_2012Metric.kicad_mod")
C0603 = ("Capacitor_SMD:C_0805_2012Metric", "C_0805_2012Metric.kicad_mod")
C1206 = ("Capacitor_SMD:C_1206_3216Metric", "C_1206_3216Metric.kicad_mod")
# SSOP-8 (TI's DCT package), not the VSSOP-8 the same die also ships in. Two
# reasons, and the second is the one that decided it:
#   - Pitch. VSSOP's 0.5 mm land leaves 0.150 mm between adjacent pads and this
#     board's net classes require 0.200 mm, so that footprint is twelve DRC
#     violations before a single track is routed. SSOP-8 at 0.65 mm gives
#     0.350 mm - more margin even than TSSOP-8's 0.250 mm.
#   - Datasheet basis. The window arithmetic below is TI's (SCES586E): the
#     K = 1.0-1.1 constant at the 10k x 0.1uF anchor, the +-0.25 uA Rext/Cext
#     leakage, the -40..125 C table. C123302 is that same TI die in a different
#     package, so the numbers carry over unchanged. A Nexperia 74LVC1G123 is a
#     different datasheet and would need the window re-derived from it.
SSOP8 = ("Package_SO:SSOP-8_2.95x2.8mm_P0.65mm", "SSOP-8_2.95x2.8mm_P0.65mm.kicad_mod")
C1206 = ("Capacitor_SMD:C_1206_3216Metric", "C_1206_3216Metric.kicad_mod")

# --- thermocouple channel geometry ---------------------------------------
# The two MAX31856 front-ends are one circuit placed twice, and this is the
# table both copies are written against: TC1_Y / TC2_Y are the chips' own y,
# every other part in a channel is `TCn_Y + <its offset>`, and the two
# channels use the SAME offsets with the sign flipped, because the two chips
# are MIRRORED.
#
# The mirror is the part worth explaining, because "make both parts face the
# same way" is the obvious instinct and it was tried and reverted here.
#
# U3 is rot 270 and U5 is rot 90 - a 180 deg flip, which on a TSSOP swaps
# which row every pin is on. So U3's digital row (pins 8-14: SPI + chip
# select) faces SOUTH and U5's faces NORTH, and the two look at each other
# across a 6 mm channel at y 41..47. The whole SPI bus lives in that channel:
# three bus nets plus two chip selects, one lane, both chips reached without
# leaving it. Turn U5 to match U3 and its digital row moves to y 52.7, which
# drags the bundle 6 mm south into the ADE7953's own escape corridor - and
# that corridor has no room. Measured, three times: `I2C_SDA` could not reach
# U7's SDA escape at (94.5, 68) and the board finished with 4 unconnected
# pads. It failed even when promoted to route FIRST, so it is a geometry
# problem, not an ordering one.
#
# What the mirror genuinely cost was NOT the rotation. It was that channel 2's
# parts had been placed on channel 1's offsets un-mirrored, so U5's analog
# inputs (pins 1-7, south) sat on the OPPOSITE side of the package from their
# own 100R/100nF/10nF input filter (north, level with the digital row).
# Channel 2's differential pair left the filter, ran the length of the chip
# past SPI_SCLK/MOSI/MISO and the chip select, and came back - on an input
# where 40 uV is a degree. Mirroring the filter with the chip fixes that and
# keeps the SPI channel; it is what TC2_DY exists to enforce.
#
# What the mirror still costs, and this is the residue: the supply pins sit
# on the far side from the x=90 decoupling column, 9.0 and 7.7 mm out against
# channel 1's 6.4 and 5.1. Moving those two caps east would fix it and puts
# 0805s in the SPI channel, which is the one thing this whole arrangement
# exists to keep clear. On a ~100 SPS sigma-delta with no fast edges, leave
# it.
#
# Nothing in the netlist can catch any of this: connectivity is identical
# whichever way a chip faces, which is exactly why the geometry is derived
# here instead.
TC1_Y, TC2_Y = 37.8, 49.8
TC1_ROT, TC2_ROT = 270, 90      # mirrored; see above before "fixing" this
TC1_DY, TC2_DY = 1, -1          # ... and every offset below flips with them

# --- SSR channel readout geometry ----------------------------------------
# Same idea, for the thing a person standing at the kiln actually reads: each
# SSR channel's amber indicator and its control test point sit on ONE row,
# the two rows 8 mm apart, and the two test points share an x. So LED3/TP9
# name channel 1 and LED4/TP10 name channel 2 by being level with each other,
# and the pair of test points is a pair you can get two probe tips onto.
#
# They used to be scattered across the switching block - LED3 (57.0, 76.0),
# LED4 (54.0, 87.5), TP9 (58.5, 80.5), TP10 (44.5, 94.15) - on four different
# y and three different x, 14.2 mm apart, with TP10 close enough to J5's pin
# row that its `SSR2` legend needed a hand-written override to stop reading
# as a fifteenth display pin (see gen_pcb.TP_LABEL_AT, now empty).
SSR_IND_X = 57.0            # both indicator LEDs
SSR_TP_X = 61.0             # both control test points, 4 mm east of the LED
SSR1_IND_Y, SSR2_IND_Y = 78.0, 86.0
SMA = ("Diode_SMD:D_SMA", "D_SMA.kicad_mod")
SOT23 = ("Package_TO_SOT_SMD:SOT-23", "SOT-23.kicad_mod")
LED0603 = ("LED_SMD:LED_0805_2012Metric", "LED_0805_2012Metric.kicad_mod")
TBLOCK = ("TerminalBlock_Phoenix:TerminalBlock_Phoenix_MKDS-1,5-2-5.08_1x02_P5.08mm_Horizontal",
          "TerminalBlock_Phoenix_MKDS-1,5-2-5.08_1x02_P5.08mm_Horizontal.kicad_mod")

COMPONENTS = {
    # --- MCU -------------------------------------------------------------
    "U1": dict(lib="RF_Module", sym="ESP32-S3-WROOM-1",
               fp="RF_Module:ESP32-S3-WROOM-1U", fpf="ESP32-S3-WROOM-1U.kicad_mod",
               value="ESP32-S3-WROOM-1U-N16R2", at=(70.0, 34.0, 0),
               # The five nav buttons on pins 31-35 map straight across to
               # J6.1-J6.5, and that mapping has all five nets crossing all
               # the others - pins 31-35 are a column at x 78.75 and J6's pins
               # a row at y 104, opposite sides of the region, so the NESTED
               # matching is the planar one. Reversing it was tried and
               # REVERTED, and the measurement is the reason: the two
               # matchings have the same total ideal length to within 0.2 mm
               # (353.0 vs 352.8), the rebuild came out 2.7 mm LONGER over two
               # fewer vias, and both figures are inside the noise of an
               # unrelated reshuffle. The crossings are nearly free because
               # the sources span 5 mm of column against a 70 mm run: the five
               # nets are almost parallel whichever way they are paired, and a
               # crossing between near-parallel tracks costs a layer change,
               # not length. Not worth a Kconfig re-map. Keep in step with
               # main/Kconfig.projbuild and docs/pin-assignments.md -
               # check_pinmap.py asserts the first two agree and CI runs it.
               pins={"1": "GND", "2": "+3V3", "3": "EN", "4": "IN1",
                     "5": "T_CS", "6": "T_IRQ", "7": "ALARM",
                     "8": "AUX2", "9": "AUX3", "10": "SSR1_CTRL",
                     "11": "I2C_SDA", "12": "LCD_CS", "13": "USB_DN",
                     "14": "USB_DP", "15": "LCD_BL", "16": "LCD_RST",
                     "17": "LCD_DC", "18": "TC1_CS", "19": "SPI_MOSI",
                     "20": "SPI_SCLK", "21": "SPI_MISO", "22": "AUX1",
                     "23": "SSR2_CTRL", "24": "I2C_SCL", "25": "LED_DATA",
                     "26": None, "27": "IO0", "28": "TC2_CS",
                     "29": "WDT_KICK", "30": None, "31": "BTN_UP",
                     "32": "BTN_DOWN", "33": "BTN_LEFT", "34": "BTN_RIGHT",
                     "35": "BTN_SEL", "36": "RXD0", "37": "TXD0",
                     "38": "IN2", "39": "IN3", "40": "GND",
                     "41": "GND"}),
    # --- Power -----------------------------------------------------------
    # The board makes its own 5 V rail from a 24 V input (U11 below). Two revs
    # ago it took 5 V directly and +5V was literally VIN minus a series
    # Schottky, so every drop and every turn of the installer's trim pot
    # landed on the WS2812B threshold, the SSR drive and the relay coil at
    # once. Regulating after the protection is what stopped that, and this
    # rev finishes the job by taking the drop out of the protection as well:
    # reverse polarity is now Q8, a P-FET at ~33 mV, and the USB OR is U12,
    # a power mux at ~40 mOhm. Between them they deleted the board's last two
    # series diode drops, on the two rails least able to spare one.
    #
    # The protection cluster stays HERE, at the entry, not beside the buck -
    # a TVS placed at the load protects only the load. The 24 V run east to
    # U11 is the cheap direction to send power: ~0.25 A against the ~1 A the
    # same load costs on a 5 V rail.
    "J2": dict(lib="Connector", sym="Screw_Terminal_01x02",
               fp=TBLOCK[0], fpf=TBLOCK[1], value="24V_IN", at=(26.0, 39.0, 270),
               pins={"1": "VIN", "2": "GND"}),
    # Review C item 1, scaled to the new input. The review named an SMAJ5.0A,
    # which on a 24 V rail is a permanent short - a 5.0 V standoff breaks down
    # at 6.4 V. F1+D8 are the same clamp-and-blow pair at the right voltage:
    # D8 defines the clamp, F1 ends the event. Neither works alone - a 400 W
    # TVS is rated for a 10/1000 us pulse, not for holding a DC fault, and a
    # PPTC on its own is far too slow to protect anything from the voltage.
    #
    # Ratings are picked against each other and against U11's 40 V abs max.
    # D8 stands off 30 V (above an HDR-15-24 at full +10% trim, 26.4 V) and
    # breaks down at 33.3 V min, so a SUSTAINED fault sits at 33-37 V, inside
    # U11's rating. Its 48.4 V clamp at 8.3 A does exceed 40 V, but that is a
    # surge figure and an abs-max is a DC spec. F1 must survive the fault
    # voltage MINUS the clamp, so its 33 V rating covers inputs to ~67 V.
    # 750 mA hold against a ~250 mA load leaves room for inrush without
    # nuisance tripping, and its 90 mohm sits upstream of a regulator.
    "F1": dict(lib="Device", sym="Polyfuse", fp="Fuse:Fuse_1812_4532Metric",
               fpf="Fuse_1812_4532Metric.kicad_mod",
               value="750mA/33V", at=(23.7, 32.2, 0),
               pins={"1": "VIN", "2": "VIN_F"}),
    "D8": dict(lib="Device", sym="D_TVS", fp=SMA[0], fpf=SMA[1],
               value="SMAJ30A", at=(35.0, 23.5, 0),
               pins={"1": "VIN_F", "2": "GND"}),
    # --- REVERSE POLARITY: a P-channel MOSFET, not a diode ----------------
    # D1, an SS34 in series with the rail, was here and was the obvious part
    # for the job right up until VIN_P stopped being a 250 mA net. It now
    # feeds the buck AND both 24 V SSR terminals, whose budget below is
    # 400 mA, so at the fuse's 750 mA hold the diode burned 0.4 V x 0.65 A =
    # 260 mW in an SMA. Q8 burns 0.65^2 x 60 mOhm = 25 mW and drops ~39 mV,
    # taking the AO3401A's GUARANTEED 60 mOhm at V_GS = -4.5 V rather than
    # the 47 mOhm typical or the 50 mOhm it reaches at -10 V, because -4.5 V
    # is the datasheet's lowest spec point still below D11's clamp. Same
    # protection, ~235 mW back, and the SSR block no longer has to spend a
    # paragraph excusing a terminal voltage of "24 V minus a diode".
    #
    # SOURCE on the LOAD side (VIN_P), DRAIN on the SUPPLY side (VIN_F), gate
    # pulled to GND. That orientation is the one that reads backwards and it
    # is not negotiable: a P-channel body diode runs drain->source, so with
    # the drain on the supply it conducts the instant power arrives and the
    # FET then enhances itself from the V_GS that appears across it. Wire the
    # part the intuitive way round and the body diode faces the supply, which
    # conducts a reversed input straight into the board and protects nothing.
    #
    # WHY 30 V IS ENOUGH HERE WHEN IT WAS NOT FOR Q5/Q6/Q7. The SSR block
    # buys 60 V CJ2310s because those switches stand off a sustained fault at
    # the 33-37 V D8 clamps it to. Q8 never stands off anything like it, in
    # either direction, and the two reasons are different:
    #   FORWARD - the body diode clamps V_DS to one drop from the first
    #     microsecond, before the gate has charged at all. The part never
    #     blocks the input voltage, not even during a fast ramp or a fault.
    #   REVERSE - a reversed input forward-biases D8, which holds VIN_F at
    #     about -0.8 V. Q8 stands off well under a volt.
    # It is also not a free choice. The whole fee-free library holds exactly
    # one P-channel part above 30 V - an LBSS84, 130 mA and 10 ohm, which
    # cannot carry this rail at all - so a 60 V P-FET here would be a feeder
    # fee to solve a problem the body diode and D8 already solve. AO3401A is
    # Q4's part, already a BOM line and already Basic: this swap adds none.
    #
    # R62 turns it on; D11 is what stops R62 destroying the gate. At 24 V an
    # unclamped V_GS is twice the AO3401A's +-12 V rating. 100k against the
    # zener's ~7.5 V at this current draws (24 - 7.5)/100k = 165 uA, i.e.
    # 4 mW against the diode's 260 mW. 8.2 V and not 10 or 12 V because the
    # tolerance stacks the wrong way - a 12 V part at +5% is 12.6 V, outside
    # the rating it exists to guard - while 7.5 V at the low end still clears
    # the -4.5 V spec point where the AO3401A guarantees 60 mOhm, which is
    # the number the loss above is taken at.
    #
    # Pin order from KiCad's Transistor_FET:AO3401A symbol, as for Q4:
    # 1 G, 2 S, 3 D.
    "Q8": dict(lib="Transistor_FET", sym="AO3401A", fp=SOT23[0], fpf=SOT23[1],
               value="AO3401A", at=(36.6, 45.6, 0),
               pins={"1": "VIN_GATE", "2": "VIN_P", "3": "VIN_F"}),
    # R62 and D11 sit SOUTH of Q8, not in the free column west of it, and
    # that column is the reason. J2's two screws are the board's only
    # per-terminal polarity marks, and the strip between J2's body (x 31.71)
    # and whatever is east of it is the only place `-` can legally print at
    # its screw's y of 44.08 - a 1.32 mm glyph needing the whole gap. An 0805
    # parked there is silk-clean by DRC and still buries the mark inside the
    # connector, which is exactly the failure the U2 row was shifted 1.5 mm
    # east to fix (see U2). The first placement of R62 did it again, and
    # silk.py caught it as "board text '-' sits on a part body".
    "R62": dict(lib="Device", sym="R", fp=R0603[0], fpf=R0603[1],
                value="100k", at=(33.5, 48.35, 0),
                pins={"1": "VIN_GATE", "2": "GND"}),
    # Pad 1 is the cathode on this footprint, so 1 = VIN_P (the source, and
    # the more positive node) and 2 = VIN_GATE. Fitted the other way round it
    # is a forward diode across the gate and the FET never turns on at all.
    "D11": dict(lib="Device", sym="D_Zener", fp="Diode_SMD:D_SOD-323",
                fpf="D_SOD-323.kicad_mod",
                value="BZT52C8V2", at=(37.4, 48.6, 180),
                pins={"1": "VIN_P", "2": "VIN_GATE"}),
    # --- +5V SOURCE SELECT: a power mux, not an ORing diode ---------------
    # D2, an SS34 from VBUS to +5V, was here. It did three jobs and did one
    # of them expensively: it let USB power the board with no 24 V present,
    # it stopped the buck back-driving a host, and - because a diode drops -
    # it handed the buck priority whenever both were live, for free. The cost
    # was 0.4 V off the USB path, and that 0.4 V is the whole reason U2 has
    # to be a TLV1117LV. See U2 below: the conclusion there does not change,
    # but the arithmetic reaching it does, so it is restated there.
    #
    # U12 does all three jobs across ~40 mOhm rather than a diode drop, and
    # adds the one this board actually needed: it blocks reverse current INTO
    # the unpowered buck. Today every USB-only bench session - which is every
    # flashing session - parks 5 V on U11's output, back-feeding FB (pin 3)
    # and, through L1, the switch pin, both rated only to V_IN on a part
    # whose V_IN is 0 V at the time. That is fab-review finding C1 and this
    # is its fix, so the measurement it asked for on board 1 is moot.
    #
    # PRIORITY MODE, NOT HIGHEST-VOLTAGE-WINS, AND THE DIFFERENCE IS THE
    # POINT. An ideal diode or a plain ORing controller passes whichever
    # input is higher, and a 5.25 V USB port is higher than a 5.0 V buck - so
    # a laptop would end up sourcing the relay bank and both SSR terminals.
    # The diode gave the buck priority by dropping; U12 has to be told. MODE
    # ties to VIN1, so pins 3 and 5 are both BUCK_5V - one net with two
    # terminals, nothing for the router to strand on a private MODE stub -
    # and R63/R64 divide BUCK_5V into PR1. Above VREF the buck wins whatever
    # USB is doing.
    #
    # 30k/10k sets the switchover at 4.0 V nominal, and that value is pinned
    # from BOTH ends rather than rounded to:
    #   TOO HIGH and the buck loses its own priority. VREF is 0.92-1.08 V, so
    #     the real threshold is 3.68-4.32 V; against a buck 4% low (4.8 V)
    #     the worst corner still reads PR1 = 1.20 V against a 1.08 V VREF.
    #     33k/10k - the obvious 4.3 V divider - leaves 36 mV at that same
    #     corner, which is not a margin.
    #   TOO LOW and THE RAIL SAGS TO THE THRESHOLD before USB takes over.
    #     Pull the 24 V with USB plugged in and +5V tracks BUCK_5V down until
    #     PR1 crosses VREF: the threshold IS the floor of that dip. 10k/4.7k
    #     needs no new BOM line and puts it at 3.13 V, under U2's dropout -
    #     so a bench supply switched off would brown out the ESP32 on the way
    #     to the USB rail it was about to reach. 3.68 V worst case clears U2
    #     (3.3 V + 90 mV at 200 mA) by 290 mV.
    # The switchover is break-before-make and ~8 us, over which +5V's own
    # ceramics (C1 22 uF + C11 10 uF + C2, ~25 uF after DC bias) droop
    # 0.3 A x 8 us / 25 uF = ~100 mV - so the dip depth is set by the
    # threshold and essentially nothing else.
    #
    # Coming back the other way dips too, and by the same amount. When 24 V
    # returns with USB attached, PR1 crosses VREF while BUCK_5V is still at
    # the 3.68-4.32 V threshold, below the ~5 V USB is holding +5V at. U12
    # opens both channels and will not close channel 1 until +5V has
    # discharged to BUCK_5V + V_RCB (42-70 mV) - TPS2116 SLVSFG1A s7.6.1 -
    # so the rail falls to the threshold on the way UP as well, and the buck
    # is never back-driven. (An earlier note here said U12 waits for BUCK_5V
    # to rise past VOUT; the datasheet says it waits for VOUT to fall.)
    #
    # MODE with the buck absent is also settled by the datasheet rather than
    # by the topology: MODE = BUCK_5V = 0 V reads as manual mode (<= 0.35 V),
    # PR1 is low, and s7.6.1 passes "the higher voltage supply between VIN1
    # and VIN2" - USB. That is what makes USB-only bench power work at all.
    #
    # ST (pin 8) IS DELIBERATELY UNCONNECTED, and it is the one thing here
    # worth reopening in a later rev. It is an open-drain "running on VIN2"
    # flag, and a kiln controller that refuses to start a firing on bench
    # power is a real feature. The only free GPIO is module pin 30 (GPIO37)
    # at x 78.75 - the far side of U1 - so the net would have to cross the
    # castellated escape band at x 60..88, the band that cost SPI_MOSI and
    # SPI_SCLK their test points the last time anything was routed through
    # it. Not worth a strandable net for a flag no firmware reads yet.
    #
    # PLACEMENT, AND IT IS NOT JUST A COURTYARD PROBLEM. SOT-583-8 is a
    # 0.5 mm-pitch part, so it belongs in gen_pcb.FANOUT with U7/U3/U5/U10
    # for exactly the reason documented there: the front layer between
    # 0.5 mm-pitch pads is entirely clearance, via-in-pad is forbidden, and a
    # pad with no seeded lane cannot start a route at all. Left out of the
    # table it fails precisely the way U10 did - "0 goal node(s), free
    # neighbours F/B=0/0" on VBUS, +5V and BUCK_5V, which is what the first
    # attempt at this part did on pass 1.
    #
    # ROT 180, NOT 0, AND THE FANOUT IS THE WHOLE REASON. all_seeds() sends
    # each pad out along whichever axis its offset from the part centre is
    # larger on. This footprint is 1.48 mm across the columns and 1.50 mm
    # along them, so the four CORNER pads escape vertically and the four
    # middle pads horizontally - a 0.01 mm margin deciding a direction. At
    # rot 0 the two corner pads that carry a net are PR1 and MODE, and they
    # escape SOUTH: 1.75 mm from y 36.95 lands at y 38.7, straight through
    # the USB pair. At rot 180 those two are at the north edge instead and
    # escape into the open band above, while GND (a plane net, via not stub)
    # and the unconnected ST take the south corners where a stub would be a
    # problem. The horizontal pairs then fall out right as well: VBUS and
    # +5V leave west toward U4/J1 and U2, BUCK_5V and +5V leave east.
    #
    # The USB pair's own constraint still holds and is now met with room to
    # spare: C3's north edge pins the pair's centreline at y 38.0 until it is
    # past C3, the pair needs 1.2 mm, so anything here must end above y 37.4.
    # The SMA ended at 37.25 with 0.15 mm of slack and the router still chose
    # to thread the pair BETWEEN its two pads, under the body. This part's
    # pads end at 36.95 and its courtyard at 37.50, and nothing of it reaches
    # into the lane, so the pair can simply run south of it.
    #
    # R63/R64 are NOT beside the part, and that is deliberate: the west
    # escape corridor (two stubs at y 35.95 and 36.45 running out to x 52.5)
    # has to stay empty, and an 0805 anywhere in D2's old footprint sits in
    # it - the first attempt put R63 at x 52.5 and its pad landed 0.20 mm
    # from the VBUS stub. They go instead in the band north of R4 (x 54.7 to
    # 60, y 29.8 to 32.6), which is the largest genuinely free area in this
    # quadrant, both rotated so their MUX_PR1 pads share y 32.31. That makes
    # PR1 a straight 2.4 mm run with U12's own PR1 stub ending 0.7 mm off it,
    # and hands BUCK_5V the detour around R63 - the right way round, because
    # PR1 is a 0.3 mm signal routed LAST while BUCK_5V is a 0.7 mm rail
    # routed fourth, into an empty band.
    #
    # ONE THING THE DIODE USED TO DO THAT U12 DOES NOT: drop 0.4 V off a
    # high USB port. VIN2 now sees VBUS directly, against a 5.5 V
    # recommended maximum and a 6.0 V absolute maximum. A compliant source
    # is 4.75-5.25 V so this is 250 mV inside the recommendation and 750 mV
    # inside the rating, and U4 (the SRV05-4 on VBUS) clamps the transients
    # either way - but a non-compliant charger sitting at 5.6 V would now be
    # out of the recommended range where the Schottky used to hide it. Judged
    # acceptable: the same charger already puts 5.6 V on the SSR gate rail,
    # the WS2812B and the display, none of which had a diode in front of them
    # either.
    #
    # +$3, the one feeder this change adds. Nothing fee-free does this job:
    # the Basic and Preferred libraries hold no power mux and no ideal-diode
    # controller at any voltage.
    "U12": dict(lib="Power_Management", sym="TPS2116DRL",
                fp="Package_TO_SOT_SMD:SOT-583-8", fpf="SOT-583-8.kicad_mod",
                value="TPS2116DRLR", at=(55.8, 36.2, 180),
                pins={"1": "GND", "2": "+5V", "3": "BUCK_5V", "4": "MUX_PR1",
                      "5": "BUCK_5V", "6": "VBUS", "7": "+5V", "8": None}),
    "R63": dict(lib="Device", sym="R", fp=R0603[0], fpf=R0603[1],
                value="30k", at=(55.8, 31.4, 270),
                pins={"1": "BUCK_5V", "2": "MUX_PR1"}),
    "R64": dict(lib="Device", sym="R", fp=R0603[0], fpf=R0603[1],
                value="10k", at=(58.2, 31.6, 90),
                pins={"1": "MUX_PR1", "2": "GND"}),
    # U12's INPUT capacitors, one per channel, and the datasheet is the reason
    # rather than taste. TPS2116 SLVSFG1A s9: "using an input capacitance
    # (CIN) of 1 uF is sufficient"; s10.1: input capacitors "must be placed
    # close to the device". Until review A6 (2026-09-29) VBUS had no
    # capacitor anywhere on the board and BUCK_5V's nearest was C44, 85 mm
    # away at the buck.
    #
    # What they are for is the switchover. With VOUT above 1 V a change of
    # channel is NOT soft-started (s7.3.2): the incoming channel closes onto
    # an output that sagged through the ~8 us break-before-make gap, and its
    # input has to supply that step at once. Behind a USB cable's ~1 uH, or
    # 85 mm of BUCK_5V track, the pin sags with it unless the charge is
    # already at the pin - which is the reason s9 itself gives ("to prevent
    # the supply voltage from dipping when the switch is turned on"). The
    # outgoing channel's current has to go somewhere too, but it is opened
    # over microseconds, not cut: ~1 uH x 0.5 A/us is ~0.5 V at a pin rated
    # to 6 V, and the cap takes most of that as well. Both are bench events
    # (USB is only attached on the bench), and the bench checklist switches
    # the 24 V with USB attached on purpose.
    #
    # 0402s, the board's only ones, because nothing larger fits either spot,
    # and each spot is the product of a failed first attempt worth knowing:
    #   C48 (BUCK_5V) sits north of R63 against J1's courtyard, beside R63's
    #     BUCK_5V pad - ~5 mm of the rail from U12 pin 3, against the 85 mm to
    #     C44. It is at the WEST edge of the pocket between J1, C6 and R63 on
    #     purpose: the pocket's middle is where R9's, C6's and LED2's
    #     designators overflow to. With C48 centred there (55.8, 28.6) its own
    #     label took that space, the greedy silk placer pushed LED2's onto
    #     the `PWR` legend, and DRC failed on silk_overlap; vertical at the
    #     west edge (54.0, 29.2) still left one label touching. Here the
    #     silk report is 0/0/0/0. It was tried twice nearer the pin as well,
    #     and the way each failed is worth knowing before trying again:
    #     - In the column east of the pin-3 rail terminal (58.25, 34.75),
    #       and in the strip north of it with its GND pad west, plane_vias()
    #       put the cap's GND via 0.75-0.79 mm from that terminal, inside
    #       the 0.85 mm a 0.7 mm track end needs. BUCK_5V failed with
    #       "0 goal node(s)" on every pass; a plane via is placed before
    #       routing and never ripped up, so no promotion rescues it.
    #     - With the GND pad east the terminal was clear, but the via
    #       (59.75, 33.75) sat on the B.Cu lane the module's west-side nets
    #       use. The board still routed, but only at pass 8 against the
    #       6-pass limit (main closes at pass 4), with the failures
    #       wandering between U1's escapes. Raising the limit would have
    #       hidden that for every future build, so the cap moved instead.
    #     Here the six-pass router closes at pass 4, on exactly main's path,
    #     with 0 DRC violations and 0 unconnected pads.
    #   C47 (VBUS) is at J1's VBUS entry, in the pocket between the VBUS
    #     seed, R4 and R63, about 6 mm of track from U12 pin 6. Its first spot,
    #     beside the VBUS terminal, split the only lane VBUS has between R4
    #     and U12's +5V escape (0.69 mm above the pads and 0.76 mm below, for
    #     a 0.5 mm track). 6 mm of 0.5 mm track is a few nH against the ~1 uH
    #     of a USB cable, so the cap still does its job from there, and it is
    #     where USB practice puts one anyway: at the receptacle.
    # C52923 is 25 V X5R, a Basic part (no feeder), and keeps roughly half
    # its capacitance at 5 V - the datasheet's 1 uF is a floor for the
    # typical case, not a tolerance, and ~0.5 uF is still what the pin
    # needs for a sub-amp step. A 6.3 V part would read
    # higher on paper and sit 1.1 V above a 5.25 V port at rated voltage.
    "C47": dict(lib="Device", sym="C", fp="Capacitor_SMD:C_0402_1005Metric",
                fpf="C_0402_1005Metric.kicad_mod",
                value="1uF", at=(52.3, 31.1, 270),
                pins={"1": "VBUS", "2": "GND"}),
    "C48": dict(lib="Device", sym="C", fp="Capacitor_SMD:C_0402_1005Metric",
                fpf="C_0402_1005Metric.kicad_mod",
                value="1uF", at=(54.4, 29.05, 180),
                pins={"1": "BUCK_5V", "2": "GND"}),
    # --- 24 V -> 5 V buck (the +5V rail) ---------------------------------
    # XL1509-5.0E1: 40 V abs max in, FIXED 5 V out, 2 A, 150 kHz, SOIC-8,
    # LCSC C61063 and a JLCPCB *Basic* part, so it costs no feeder fee. Two
    # things picked it over the adjustable 500 kHz parts: 40 V of input
    # headroom means the 12/24 V misconnect that used to destroy U2 is not
    # even a fault any more, and a fixed output needs no feedback divider -
    # two fewer parts and no divider to get wrong. FB (pin 3) ties straight
    # to the output for the fixed version. EN (pin 4) is active LOW, so it is
    # grounded to keep the regulator enabled.
    #
    # The whole block sits in the south-east because that is the only region
    # of this board with room: 266 mm2 at x 100.25-119.25, y 95.75-109.75
    # carrying zero tracks and zero vias. The power corner cannot take it -
    # measured, its largest free pocket is 12.5 x 6.5 mm and the y 30-36 band
    # is boxed in by J2, R5 and U2 on three sides, so fitting the buck there
    # means exiling the LDO block out of the quadrant entirely.
    #
    # Being 18-34 mm from the CT front-end is the price. It is affordable
    # rather than free: the ADE7953 measures a 50/60 Hz signal through the
    # 1k/33nF filters on CTA_F/CTB_F, whose ~4.8 kHz corner puts 150 kHz
    # ~30x down, and the MAX31856s are 50-60 mm away behind their own
    # filters. Keep the hot loop (C41/C42 -> U11 pin 1 -> pin 2 -> D7 -> GND)
    # tight; it, not the inductor, is what radiates.
    "C41": dict(lib="Device", sym="C", fp=C1206[0], fpf=C1206[1],
                value="10uF/50V", at=(104.0, 98.5, 0),
                pins={"1": "VIN_P", "2": "GND"}),
    "C42": dict(lib="Device", sym="C", fp=C1206[0], fpf=C1206[1],
                value="10uF/50V", at=(110.5, 98.5, 0),
                pins={"1": "VIN_P", "2": "GND"}),
    "C43": dict(lib="Device", sym="C", fp=C0603[0], fpf=C0603[1],
                value="100nF", at=(116.0, 98.5, 0),
                pins={"1": "VIN_P", "2": "GND"}),
    "U11": dict(lib="Regulator_Switching", sym="XL1509-5.0",
                fp="Package_SO:SOIC-8_3.9x4.9mm_P1.27mm",
                fpf="SOIC-8_3.9x4.9mm_P1.27mm.kicad_mod",
                value="XL1509-5.0E1", at=(104.5, 103.5, 0),
                pins={"1": "VIN_P", "2": "SW_5V", "3": "BUCK_5V", "4": "GND",
                      "5": "GND", "6": "GND", "7": "GND", "8": "GND"}),
    # Catch diode. Non-synchronous buck, so this carries the inductor current
    # for ~79% of every cycle - it is not optional and it is not a snubber.
    # SS34 is already a BOM line and its 40 V / 3 A covers a 24 V input at
    # 1.28 A peak. Pad 1 = cathode, on the switch node.
    "D7": dict(lib="Device", sym="D_Schottky", fp=SMA[0], fpf=SMA[1],
               value="SS34", at=(112.5, 102.0, 0),
               pins={"1": "SW_5V", "2": "GND"}),
    # 47 uH is the small end, not a lazy round number: at 150 kHz and
    # 24 -> 5 V it gives dI = 5 x 0.792 / (47u x 150k) = 0.56 A, so 56%
    # ripple on a 1 A load and a 1.28 A peak. Going smaller makes that worse,
    # not the part - inductor volume goes as L x I^2.
    "L1": dict(lib="Device", sym="L", fp="Inductor_SMD:L_Changjiang_FXL0650",
               fpf="L_Changjiang_FXL0650.kicad_mod",
               # +5V on pin 1, SW_5V on pin 2, and the order is not arbitrary
               # even though an inductor is symmetric. A rail's port symbol is
               # never rotated - a +5V bar sits ABOVE its wire - so a rail on
               # the DOWNWARD pin makes power_path() elbow the wire sideways,
               # into the same flank field_pos() hands to an all-vertical-pin
               # part's Reference/Value. That collision is a check_sch_layout
               # failure, and swapping the pins is the whole fix.
               value="47uH/2A", at=(114.0, 107.5, 0),
               pins={"1": "BUCK_5V", "2": "SW_5V"}),
    "C44": dict(lib="Device", sym="C", fp=C1206[0], fpf=C1206[1],
                value="22uF", at=(103.0, 108.5, 0),
                pins={"1": "BUCK_5V", "2": "GND"}),
    "C45": dict(lib="Device", sym="C", fp=C1206[0], fpf=C1206[1],
                value="22uF", at=(108.0, 108.8, 90),
                pins={"1": "BUCK_5V", "2": "GND"}),
    # C46 is the reason this rail is stable, and it is NOT interchangeable
    # with more ceramic. The XL1509 is an LM2596-class VOLTAGE-mode regulator
    # with fixed internal compensation: the loop has an LC double pole and no
    # zero of its own, so it relies on the ESR zero of the output capacitor to
    # recover phase before crossover. The datasheet says so by omission and by
    # example - its 5 V/2 A design table (Rev 2.0 p.9) lists ONLY through-hole
    # electrolytic (180 uF/35 V) or surface-mount tantalum (100 uF/10 V) for
    # COUT, and p.8's note about "very low ESR output capacitors" offers a
    # feed-forward capacitor as the cure, which the FIXED-output part cannot
    # take: FB is tied straight to the output, so there is no divider to put
    # CFF across.
    #
    # C44/C45 alone are 2 x 22 uF X5R, ~32 uF after DC bias at 5 V, ESR a few
    # milliohms. That puts the double pole at 1/(2*pi*sqrt(47u*32u)) = 4.1 kHz
    # and the ESR zero near 1 MHz - i.e. nowhere useful - which is the classic
    # all-ceramic instability for this family. Adding 100 uF of aluminium at
    # ~0.5-1.5 ohm ESR moves the pole to ~2.0 kHz and plants a zero at
    # 1.1-3.2 kHz, right where it is wanted.
    #
    # High ESR is a FEATURE here and costs nothing in ripple: at 150 kHz the
    # ceramics are ~0.04 ohm and this part is ~1 ohm, so the ceramics shunt
    # ~96% of the inductor ripple and C46 sees ~6 mA against its 50 mA rating.
    # Do not "improve" it with a polymer or another MLCC - both have the low
    # ESR that is the problem.
    #
    # D5 x 5.4 mm rather than the commoner D6.3: the only free board left in
    # this corner is 6.0 mm tall (CP_Elec_6.3x5.4 needs a 7.10 mm courtyard),
    # and 100 uF is the largest value that fits a D5 can. Placed south-west of
    # C44 with 0.66 mm of courtyard clearance to it, 3.4 mm of body-to-centre
    # clearance to FID3 (the assembly camera needs to see the fiducial), and a
    # ~7.8 mm run on +5V - long for a ceramic, irrelevant for a bulk cap whose
    # job is at 2 kHz. No fee-free equivalent exists: LCSC lists no aluminium
    # electrolytic in the Basic or Preferred libraries at all, so this line
    # costs the eleventh feeder fee ($3).
    "C46": dict(lib="Device", sym="C_Polarized",
                fp="Capacitor_SMD:CP_Elec_5x5.4", fpf="CP_Elec_5x5.4.kicad_mod",
                value="100uF/16V", at=(97.5, 113.25, 0),
                pins={"1": "BUCK_5V", "2": "GND"}),
    # The regulator and the bulk-cap row east of it sit 1.5 mm further east
    # than they did, as one block: U2 36.6 -> 38.1, C1 44.0 -> 45.5, C3
    # 49.2 -> 50.7, C4 53.8 -> 55.3. They are shoulder to shoulder (the
    # smallest pad-to-pad gap in the row is ~1.1 mm), so moving one means
    # moving all four, and the last of them still clears U12 and the module.
    #
    # The reason is silk, which is a thin reason for moving a regulator and
    # was still the right call. J2 is the board's power INPUT, and the only
    # place its two screws can be named individually is the strip east of the
    # block - there is 0.67 mm to the board edge on the other side. U2's
    # three SOT-223 lead pads used to start 1.13 mm from J2's outline at
    # exactly the y of the `+` screw, leaving 0.93 mm of usable column for a
    # 1.32 mm glyph, so `+` had nowhere legal to print and the placer buried
    # it inside J2 - the same failure the mark exists to prevent. No y offset
    # helps either: U2's leads span y 36.45..42.55 continuously and J2's two
    # screws are inside that band 5.08 mm apart. The column is now 2.43 mm.
    # TLV1117LV33, not AMS1117: same SOT-223, same 1117 pinout (GND/OUT/IN,
    # tab=OUT), but dropout is 700mV MAX at 1A against the AMS1117's 1.1V
    # at 800mA. The AMS1117 is a JLCPCB *Basic* part, so the swap keeps
    # getting proposed as a free $3 (#348). It is not free, and the reason
    # is NOT the 24V input:
    #
    # U2's input rail has two sources. U11 is one, and behind the buck's
    # regulated 5.0V an AMS1117 would be fine. USB is the other, and it is
    # the one that decides the part: VBUS -> +5V is how the board runs on
    # USB alone, which is every bench and flashing session.
    #
    # THIS SURVIVED U12, WHICH IS THE INTERESTING PART, because removing the
    # ORing diode's 0.4V is exactly the change that should have reopened it.
    # It does not, and the reason is that USB's own tolerance is wider than
    # the drop that was deleted. A 4.75V port (5V -5%) behind the old SS34
    # put +5V at 4.35V against the AMS1117's ~4.4V need - out of regulation
    # before the ESP32 had transmitted anything. Through U12's ~40 mOhm the
    # same port puts +5V at 4.73V, which looks like 330mV of margin and is
    # not: 4.75V is specified AT THE PORT, and a cable plus two contacts at
    # 0.2-0.5 ohm take another 0.1-0.25V out of it at half an amp. That
    # leaves the AMS1117 somewhere between 0.2V and 0.05V, and behind a
    # bus-powered hub (4.35V at the connector, which USB permits) it is out
    # of regulation again. The TLV's 700mV-max dropout holds in all of it.
    # Neither U11 nor U12 raised the floor of the USB path - only the port
    # and the cable set that - so "the board has more headroom now" is true
    # twice over and still does not apply here.
    #
    # Nor is the SOT-223 the constraint, which is the next thing asked. The
    # WHOLE fee-free library - 350 Basic plus 996 Preferred, enumerated, not
    # searched (2026-09-09) - holds three fixed 3.3V linear regulators in
    # any package: this AMS1117, a 100mA HT7533-1 (C14289, SOT-89-3) and a
    # 200mA XC6206 (C5446, SOT-23-3L). Both of the others are an order of
    # magnitude short of the 240mA the ESP32 alone draws. There is no
    # fee-free 3.3V LDO on JLCPCB that can carry this rail, full stop.
    #
    # The one thing that would work is a SWITCHER: XL1509-ADJE1 (C74192) is
    # Preferred, it is U11's own family, and a second one at 3.3V could reuse
    # L1's inductor and an SS34, so it adds no feeder fee and removes this
    # one. A real -$3. Three reasons it is not taken, and NONE of them is
    # "150 kHz is too noisy for the analog front end" - that objection was
    # made here once and it is wrong. The ADE7953 post-regulates internally
    # (VINTA/VINTD/REF are on-chip LDO/reference outputs, decoupled below),
    # the CT path corners at 4.8 kHz so 150 kHz is 31x out, and the MAX31856s
    # convert over ~100 ms behind a 50/60 Hz notch. The fundamental is filtered
    # three times over before it reaches anything that measures.
    #
    #   1. THE BEAT, which nothing filters. The XL1509 has no SYNC pin and its
    #      own spread is 127-173 kHz, so two of them sit tens of kHz apart and
    #      drift independently with temperature and load. Each is a duty-cycle-
    #      modulated load on the shared rail, i.e. a mixer, and |f1-f2| lands
    #      inside both control loops' bandwidth, so the loops track it and put
    #      it on their outputs. That difference frequency goes anywhere from a
    #      few Hz to 46 kHz and MOVES - down through 50/60 Hz where the ADE7953
    #      integrates, and through DC where the MAX31856 lives. A 5 Hz beat is
    #      temperature wander that never reproduces on the bench. Solvable by
    #      frequency choice, never by filtering: see the rev-C note below.
    #
    #   2. FAULT ENERGY, and this is the kiln-specific one. R49's fail-safe
    #      (below) has U10 - the watchdog that drops the SSR - sitting on the
    #      rail U2 makes. An LDO pass element failing short puts 5V on that
    #      rail. A 24V-fed buck failing short puts 24V on it. Same failure,
    #      different energy, on the one part standing between a wedged
    #      controller and 5 kW of element.
    #
    #   3. THE BOARD HAS NEVER BEEN BUILT. Putting a switcher on the analog
    #      rail at the same time as first silicon on the metering and
    #      thermocouple front ends means that if the noise floor disappoints
    #      there is no known-good rail to A/B against. That is the actual
    #      reason to wait, and it expires the moment rev B is characterised.
    #
    # The one argument that DOES favour the switcher is thermal, and it is
    # better than the bench numbers suggest: 0.51 W at 300 mA is a ~27 C rise
    # in this SOT-223 with its pour, but a kiln controller's enclosure ambient
    # is not 25 C, and at 50 C ambient a 500 mA peak puts the junction near
    # 95 C. Inside the 125 C spec, thinner than "0.85 W, that's nothing".
    #
    # REV C, if U2's thermals turn out to be the real constraint: TPS5430DDAR
    # (C9864, Basic, 500 kHz, SOIC-8-EP) or TPS54331DR (C9865, Preferred,
    # 570 kHz). Either beats U11 at ~350/420 kHz, out of band rather than
    # hoped away, takes 3.3V straight off the 24V input, and still reuses
    # L1's 47 uH (dI = 0.12 A at 500 kHz), so it stays fee-free. Design the
    # beat out; do not filter it.
    #
    # Ceramic-stable at 0-ohm ESR (C3/C4 unchanged), Iq 100uA max. The old
    # trade — Vin abs max 6V against the AMS1117's 15V, so a 9/12V adapter
    # kills U2 first — is gone with the 5V input: J2 is 24V into U11 now,
    # and the only unregulated path to U2 is VBUS, which USB caps at 5.5V.
    # KiCad ships no TLV1117LV symbol; TLV1117-33 is the same family and
    # pin map, with the value carrying the real part.
    "U2": dict(lib="Regulator_Linear", sym="TLV1117-33",
               fp="Package_TO_SOT_SMD:SOT-223-3_TabPin2",
               fpf="SOT-223-3_TabPin2.kicad_mod",
               value="TLV1117LV33", at=(38.1, 39.5, 0),
               pins={"1": "GND", "2": "+3V3", "3": "+5V"}),
    "C1": dict(lib="Device", sym="C", fp=C1206[0], fpf=C1206[1],
               value="22uF/25V", at=(45.2, 39.5, 0),
               pins={"1": "+5V", "2": "GND"}),
    "C2": dict(lib="Device", sym="C", fp=C0603[0], fpf=C0603[1],
               value="100nF", at=(42.4, 45.6, 0),
               pins={"1": "+5V", "2": "GND"}),
    "C3": dict(lib="Device", sym="C", fp=C1206[0], fpf=C1206[1],
               value="22uF/25V", at=(50.2, 39.5, 0),
               pins={"1": "+3V3", "2": "GND"}),
    "C4": dict(lib="Device", sym="C", fp=C0603[0], fpf=C0603[1],
               value="100nF", at=(54.3, 39.9, 0),
               pins={"1": "+3V3", "2": "GND"}),
    "LED2": dict(lib="Device", sym="LED", fp=LED0603[0], fpf=LED0603[1],
                 value="green", at=(55.5, 22.3, 0),
                 pins={"1": "LEDP_K", "2": "+3V3"}),
    "R9": dict(lib="Device", sym="R", fp=R0603[0], fpf=R0603[1],
               value="1k", at=(55.5, 25.0, 0),
               pins={"1": "LEDP_K", "2": "GND"}),
    # decoupling at module
    "C6": dict(lib="Device", sym="C", fp=C0603[0], fpf=C0603[1],
               value="100nF", at=(58.65, 28.0, 90),
               pins={"1": "+3V3", "2": "GND"}),
    "C7": dict(lib="Device", sym="C", fp=C0603[0], fpf=C0603[1],
               value="10uF", at=(58.65, 23.8, 90),
               pins={"1": "+3V3", "2": "GND"}),
    # --- EN / BOOT -------------------------------------------------------
    "R1": dict(lib="Device", sym="R", fp=R0603[0], fpf=R0603[1],
               value="10k", at=(56.0, 42.3, 0),
               pins={"1": "+3V3", "2": "EN"}),
    # Rotated (270, so GND is the SOUTH pad) rather than 0, so the GND pad
    # faces the open pour below instead of the sliver between C5, R1 and the
    # module's left edge. At rot 0 that sliver was too narrow to take a
    # stitching via once vias were barred from sitting inside pads
    # (router.VIA_PAD_GAP), stranding this pad on F.Cu.
    #
    # This comment described a rotation the table had stopped carrying - the
    # `at` said 0 - and the board went back to failing the way the comment
    # says it does, just via a different mechanism: at rot 0 the pads lie
    # EAST-WEST, so EN enters on the west and has to come round the north of
    # the part to reach it, and the EN track then runs 1.30 mm over the GND
    # pad and starves its F.Cu thermal to one spoke where the rule wants two.
    # KiCad calls that `starved_thermal`, and it was the board's only DRC
    # violation after U12 went in (the mux re-rolled the routing order, which
    # is what moved EN onto that line). At 270 the pads lie NORTH-SOUTH: EN
    # is the north pad and meets its own track head-on, GND is the south pad
    # with the open pour under it. Do not "simplify" this back to 0.
    "C5": dict(lib="Device", sym="C", fp=C0603[0], fpf=C0603[1],
               value="1uF", at=(52.0, 42.7, 270),
               pins={"1": "EN", "2": "GND"}),
    "R2": dict(lib="Device", sym="R", fp=R0603[0], fpf=R0603[1],
               value="10k", at=(106.0, 22.5, 0),
               pins={"1": "+3V3", "2": "IO0"}),
    # SMD tactile switches, not the 6 mm THT part: XKB TS-1187A (LCSC
    # C318884) is a JLCPCB *Basic* part, so it carries no $3 feeder fee and
    # stays on the SMT line. The THT switches were one of five unique
    # Extended parts that existed only to force Standard assembly.
    #
    # The two buttons are a PAIR and are now placed as one: RESET at x=91,
    # BOOT at x=100, both on y=25, in the free band between the module's east
    # edge (79.75) and H2's pad ring. RESET used to sit at (36.5, 24.2), on
    # the far side of the board from BOOT, which is the wrong arrangement for
    # the one operation that uses both - hold BOOT, tap RESET, release - and
    # it left each button in a 1.2-2.0 mm strip where neither legend fit
    # (`RESET` printed under its own button for two revisions; see
    # gen_pcb.SILK). Level with BOOT, the same 2.4 mm strip that takes `BOOT`
    # takes `RESET`, and the gap between them is 2.5 mm of clear board.
    #
    # The cost is EN's length: the net's other members are R1/C5 beside the
    # module's west edge, so the switch stub is now ~40 mm rather than ~15.
    # That is acceptable here and would not be on a bare reset pin - C5 is a
    # 1 uF sitting AT the module, so the stub is terminated in something very
    # stiff (10 ms with R1), and EN is a static level, not a signal. Do not
    # copy the arrangement to a design whose reset input has only a 100 nF.
    "SW1": dict(lib="Switch", sym="SW_Push",
                fp="Button_Switch_SMD:SW_Push_1P1T_XKB_TS-1187A",
                fpf="SW_Push_1P1T_XKB_TS-1187A.kicad_mod",
                value="RESET", at=(91.0, 25.0, 0),
                pins={"1": "EN", "2": "GND"}),
    "SW2": dict(lib="Switch", sym="SW_Push",
                fp="Button_Switch_SMD:SW_Push_1P1T_XKB_TS-1187A",
                fpf="SW_Push_1P1T_XKB_TS-1187A.kicad_mod",
                value="BOOT", at=(100.0, 25.0, 0),
                pins={"1": "IO0", "2": "GND"}),
    # --- USB -------------------------------------------------------------
    "J1": dict(lib="Connector", sym="USB_C_Receptacle_USB2.0_16P",
               fp="Connector_USB:USB_C_Receptacle_HRO_TYPE-C-31-M-12",
               fpf="USB_C_Receptacle_HRO_TYPE-C-31-M-12.kicad_mod",
               value="USB-C", at=(48.0, 24.4, 180),
               pins={"A1": "GND", "A12": "GND", "B1": "GND", "B12": "GND",
                     "A4": "VBUS", "A9": "VBUS", "B4": "VBUS", "B9": "VBUS",
                     "A5": "CC1", "B5": "CC2",
                     "A6": "USB_DP", "B6": "USB_DP",
                     "A7": "USB_DN", "B7": "USB_DN",
                     "A8": None, "B8": None,
                     # shield pin: "S1" in KiCad <=9 libs, "SH" in KiCad 10
                     "S1": "GND", "SH": "GND"}),
    "R4": dict(lib="Device", sym="R", fp=R0603[0], fpf=R0603[1],
               value="5.1k", at=(53.0, 33.6, 0),
               pins={"1": "CC1", "2": "GND"}),
    "R5": dict(lib="Device", sym="R", fp=R0603[0], fpf=R0603[1],
               value="5.1k", at=(42.0, 33.6, 0),
               pins={"1": "CC2", "2": "GND"}),
    # SRV05-4 rather than the USBLC6-2SC6 this used to be, which is the same
    # part D5 and D6 already carry. The driver was JLCPCB's feeder fee — one
    # part number across three designators instead of two costs $3 less per
    # order, and the SRV05-4 line chosen (C7420376) is a *Preferred* extended
    # part, so it is another $3 cheaper again. That is $6 of a $27 bill, and
    # it is the whole reason this changed.
    #
    # It is not a compromise made to save it. Measured off the two datasheets,
    # the SRV05-4 is the better part here on both axes that matter:
    #
    #   * ESD. USBLC6-2SC6 is IEC 61000-4-2 level 4 and no more - +-8 kV
    #     contact, +-15 kV air. This one is +-30 kV on both.
    #   * Capacitance. 1.0 pF per channel against the USBLC6's 3.5 pF max, on
    #     a pair whose impedance the STACKUP comment goes to some length to
    #     keep at 93.1 ohm.
    #
    # Placed as a FLOW-THROUGH, and the pin map below is that decision. The
    # USBLC6 was a pass-through part: each channel is brought out on both
    # faces (1/6 and 3/4), so the pair entered one side and left the other.
    # The SRV05-4's four channels are independent, one pin each, and the
    # first rev of this swap used two of them (IO3/IO4, east face) and let
    # the pair reach them as stubs. That cannot be routed as a coupled pair
    # at all, and the reason is topological rather than a matter of skill:
    # both pads sit on ONE face, so whichever track runs nearer the part can
    # stub straight in, but the other has to cross it to reach its own pad.
    # The router did the only thing left - took D+ the long way round the
    # package - and the pair came out 50.8 mm against 33.2 mm, over 8 and 5
    # vias, with 0% of its length coupled.
    #
    # So the part is turned 90 degrees to put its pad rows across the pair's
    # path (rot 270: pins 1/2/3 on the north row facing J1, 4/5/6 south), and
    # each line uses BOTH pins of one column: D+ enters pin 3, runs 1 mm under
    # the body, and leaves by pin 4 directly below it; D- does the same
    # through pins 1 and 6. Two straight lines, no stubs, no detour, and the
    # rest of the pair can be routed coupled from the south row onward
    # (gen_pcb.usb_pair_seeds draws this from the pad positions - move the
    # part and the copper follows). The price is the loading this comment
    # once refused to pay - 2.0 pF per line instead of 1.0 - and it is worth
    # paying now that it buys the flow-through: it is still under the 3.5 pF
    # the USBLC6 had, against a Full-Speed budget measured in tens of pF.
    #
    # The middle column is VN (pin 2, GND) north and VP (pin 5, VBUS) south,
    # and that orientation is deliberate. Each middle pad is boxed in by the
    # two lines on either side of it, so each can only be reached through the
    # 1.6 mm channel between them: pin 2 gets its plane via in the channel
    # between J1's escapes, and pin 5 gets VBUS by a via in the channel below
    # the south row, before the two lines converge into a pair. The hand
    # escapes in gen_pcb leave exactly those two slots open. VP goes to VBUS,
    # not +3V3: this array clamps to the rail on pin 5, and the lines it
    # protects are referenced to the 5 V bus.
    #
    # SRV05-4: 1 IO1, 2 VN(GND), 3 IO2, 4 IO3, 5 VP(VBUS), 6 IO4 - the same
    # pinout D5/D6 are documented against below.
    "U4": dict(lib="Power_Protection", sym="SRV05-4",
               fp="Package_TO_SOT_SMD:SOT-23-6", fpf="SOT-23-6.kicad_mod",
               value="SRV05-4", at=(48.0, 34.8, 270),
               pins={"3": "USB_DP", "4": "USB_DP",
                     "1": "USB_DN", "6": "USB_DN",
                     "5": "VBUS", "2": "GND"}),
    # --- Thermocouple ------------------------------------------------------
    # 2x MAX31856 (TSSOP-14) replacing the rev A MAX31855. Pinout confirmed
    # against the KiCad 10 Sensor_Temperature:MAX31856 symbol and the Maxim
    # 19-7534 Rev 0 datasheet (see hardware/kicad/datasheets/REV-B-NOTES.md
    # SS5): 1 AGND 2 BIAS 3 T- 4 T+ 5 AVDD 6 DNC 7 ~DRDY 8 DVDD 9 ~CS 10 SCK
    # 11 SDO 12 SDI 13 ~FAULT 14 DGND. ~DRDY/~FAULT/DNC are left NC - both
    # status bits are readable from registers, and polling them is what keeps
    # the GPIO budget closing (spec 4.1). AVDD/DVDD are separate pins but must
    # share one 3V3 rail (datasheet: AVDD-DVDD limited to +-100mV) with
    # independent 100nF decoupling per pin, each to this board's single GND
    # net (no AGND/DGND split plane exists elsewhere on this board).
    #
    # REV-B-NOTES.md SS5a overrides the brief here: there is NO bias bypass
    # capacitor. "This pin is floating when no conversions are taking place...
    # No bypass or decoupling is specified" (datasheet p.10), unlike AVDD/DVDD
    # which both explicitly call for one. The 0.01uF cap in the datasheet's own
    # application drawings belongs to the T- common-mode filter, not to BIAS.
    # The brief's C14 (100nF, BIAS->GND) is therefore omitted outright.
    #
    # BIAS routing: Figure 8 (the filtered topology this design follows, with
    # the 100R series resistors) is explicit that "BIAS connects to the
    # thermocouple side of the resistor" (SS5a) - i.e. the RAW terminal-side
    # node, upstream of the series R, NOT the IC-side filtered T- pin. That is
    # a different diagram from the datasheet's simple Typical Application
    # Circuit (no series resistors), where BIAS and T- share one pin-level
    # node - do not conflate the two. So here BIAS (pin 2) joins TC1_N/TC2_N
    # (the raw terminal net, same node as J3.2/R15.1), while T- (pin 3) stays
    # alone on the IC-side filtered node TC1_N_F/TC2_N_F, symmetric with
    # T+'s TC1_P_F/TC2_P_F. The open-thermocouple detection bias current
    # sources from BIAS through the thermocouple itself, not through the
    # external filter resistor - routing it through R15/R17 the way the
    # simple-circuit reading would have put that bias current across the
    # filter resistor, which Figure 8's topology specifically avoids.
    #
    # Input filter per REV-B-NOTES.md SS5c / datasheet Figure 8 ("Typical
    # Connection to Reduce the Effect of Noise Pickup"), fit unconditionally -
    # this board sits beside SSR-switched mains wiring with a Wi-Fi radio on
    # the same PCB, the RF-field case the datasheet calls out: 100R 1% series
    # in each leg (1% so the T+/T- series resistors stay matched - datasheet
    # p.28 ties resistor mismatch directly to offset voltage), then, on the
    # IC side of those resistors, 100nF differential across T+/T- plus 10nF
    # common-mode from each leg to GND. No TVS on these nets (spec 4.1): a TVS
    # array's leakage into a ~40uV/degC source is an accuracy error, not
    # protection - the RC filter plus the chip's own input clamps are it.
    #
    # TC1_N/TC2_N run to the screw terminal raw, NOT to GND - unlike rev A's
    # MAX31855 whose T- was grounded at the chip, each MAX31856 channel keeps
    # its own floating differential pair (T- is only soft-referenced near
    # AGND through the internal ~2k BIAS network, not hard-tied to it).
    # Ungrounded-junction probes are required on the finished board: both
    # channels reference T- through that shared internal biasing, so two
    # grounded-junction probes in one kiln chamber would form a ground loop
    # through the kiln body (documentation obligation, Task 16 - not a board
    # change).
    "U3": dict(lib="Sensor_Temperature", sym="MAX31856",
               fp="Package_SO:TSSOP-14_4.4x5mm_P0.65mm",
               fpf="TSSOP-14_4.4x5mm_P0.65mm.kicad_mod",
               value="MAX31856MUD+", at=(97.0, TC1_Y, TC1_ROT),
               pins={"1": "GND", "2": "TC1_N", "3": "TC1_N_F",
                     "4": "TC1_P_F", "5": "+3V3", "6": None, "7": None,
                     "8": "+3V3", "9": "TC1_CS", "10": "SPI_SCLK",
                     "11": "SPI_MISO", "12": "SPI_MOSI", "13": None,
                     "14": "GND"}),
    # AVDD/DVDD decoupling. The datasheet requirement is "independent 100nF
    # per pin", which this satisfies; the DISTANCES are loose and deliberately
    # left that way. Measured pad-to-supply-pin, both channels: 6.4 mm to
    # AVDD, 5.1 mm to DVDD.
    #
    # They agree because THE TWO CHANNELS ARE NOW THE SAME CIRCUIT, laid out
    # twice at a 12.0 mm pitch, and that is the point of the arrangement
    # rather than a coincidence worth preserving by hand. Every part below
    # sits at a fixed offset from its own MAX31856 (see TC_CHANNEL_DY), so a
    # change to one channel is a change to both and the two thermocouple
    # front-ends cannot silently diverge - which they had. U5 used to be
    # rotated 90 against U3's 270, a 180 deg flip that put its AVDD/DVDD on
    # the opposite rows from U3's while the caps stayed on a shared x=90
    # column derived for U3: 9.0 mm and 7.7 mm, the worst pair on the board,
    # and nothing said so. Worse, the flip put U5's ANALOG row (pins 1-7,
    # TC2_N/TC2_N_F/TC2_P_F) on the south side while its 100R/100nF/10nF
    # input filter sat to the north, level with the digital row - so the two
    # channels' input networks were not the same shape, on a differential
    # input worth ~40 uV/C. See the note above U5.
    #
    # Tightening the caps FURTHER was tried and REVERTED; do not repeat it
    # without reading what happened. Parking each cap on its own supply pin's
    # centreline at 1.74 mm left four nets unroutable (TC1_CS, TC2_CS,
    # TC1_P_F, TC2_P_F), because two things already own those centrelines out
    # to ~2.75 mm: the pre-seeded fanout escapes (FANOUT["U3"] = 1.5 mm plus
    # the alternating 0.75 mm, whose far ends ARE the router's terminals) and
    # the +3V3 pins' own plane vias, which land at FANOUT + 1.25 on the same
    # ray. A 0.65 mm pitch TSSOP has no lane to spare either side. Trading a
    # routing perturbation in the densest region of the board (2.30
    # parts/cm2) for a good-practice distance, on a ~100 SPS sigma-delta with
    # no fast edges, is not a trade worth making.
    "C13": dict(lib="Device", sym="C", fp=C0603[0], fpf=C0603[1],
                value="100nF", at=(90.0, TC1_Y - 2.8 * TC1_DY, 0),
                pins={"1": "+3V3", "2": "GND"}),
    "C14": dict(lib="Device", sym="C", fp=C0603[0], fpf=C0603[1],
                value="100nF", at=(90.0, TC1_Y + 2.7 * TC1_DY, 0),
                pins={"1": "+3V3", "2": "GND"}),
    "R14": dict(lib="Device", sym="R", fp=R0603[0], fpf=R0603[1],
                value="100R 1%", at=(102.2, TC1_Y - 3.8 * TC1_DY, 180),
                pins={"1": "TC1_P", "2": "TC1_P_F"}),
    "R15": dict(lib="Device", sym="R", fp=R0603[0], fpf=R0603[1],
                value="100R 1%", at=(105.9, TC1_Y - 3.8 * TC1_DY, 180),
                pins={"1": "TC1_N", "2": "TC1_N_F"}),
    "C15": dict(lib="Device", sym="C", fp=C0603[0], fpf=C0603[1],
                value="100nF", at=(102.2, TC1_Y + 0.2 * TC1_DY, 0),
                pins={"1": "TC1_P_F", "2": "TC1_N_F"}),
    "C16": dict(lib="Device", sym="C", fp=C0603[0], fpf=C0603[1],
                value="10nF", at=(105.9, TC1_Y + 0.2 * TC1_DY, 0),
                pins={"1": "TC1_P_F", "2": "GND"}),
    "C17": dict(lib="Device", sym="C", fp=C0603[0], fpf=C0603[1],
                value="10nF", at=(103.0, TC1_Y + 4.2 * TC1_DY, 0),
                pins={"1": "TC1_N_F", "2": "GND"}),
    "J3": dict(lib="Connector", sym="Screw_Terminal_01x02",
               fp=TBLOCK[0], fpf=TBLOCK[1], value="TC1_K",
               at=(114.0, TC1_Y + 3.2, 90),
               pins={"1": "TC1_P", "2": "TC1_N"}),
    # --- Thermocouple channel 2 (load TC) - channel 1 again, 12 mm south
    # and MIRRORED, with TC2_* nets and TC2_CS. Every `at` below is the
    # channel-1 line with TC1_Y -> TC2_Y and the offset flipped by TC2_DY,
    # so the filter, the caps and the terminal all follow the chip's flip
    # instead of being left on channel 1's side of it (see the TC1_Y/TC2_Y
    # note above - they had been, and channel 2's differential inputs paid
    # for it). Move a part in one channel and move it in both.
    #
    # THE MIRROR IS IN X AS WELL AS Y, and only the y half used to be applied.
    # Flipping U5 reverses the order of its analog pins: U3 reads P_F (97.00),
    # N_F (97.65), N (98.30) west to east and U5 reads N (95.70), N_F (96.35),
    # P_F (97.00). The chip did not move in x, so the FILTER COLUMNS have to
    # reverse to follow it - R16 (the P leg) east at 105.9 and R17 (the N leg)
    # west at 102.2, the opposite of channel 1's R14/R15. With channel 1's x
    # order copied straight across, both ends of the channel crossed: J8's
    # near screw (P, y 53.0) reached for the far west resistor while the far
    # screw (N, y 47.92) reached for the near east one, and downstream P_F
    # left the west pad for the east pin while N_F did the reverse. Channel 1
    # routes 35.2 mm over ZERO vias; channel 2 was routing 128.9 mm over ten,
    # for the same circuit, on a differential input where 40 uV is a degree.
    #
    # C20 turns with them (rot 180), which puts its N_F pad exactly under
    # R17's. C21 and C22 do not move and both get closer to their own nets as
    # a side effect - C21's P_F pad now lands on R16's, where before it was
    # 3.7 mm away across the pair.
    #
    # R16/R17 and C20/C21 keep one exception to the y mirror, and it is J8
    # rather than U5 that makes them one: they are pushed 1.6 mm and 0.4 mm
    # FURTHER out than the mirror asks. Channel 1's filter row clears J3's screws by 0.47 mm going
    # north; mirrored, channel 2's would land on J8's - R17's pads span y
    # 52.9..54.3 and J8's `K+` legend wants 52.25..53.75, the same board.
    # There is no second column to move the legend into (J8's body starts
    # 1.16 mm east of R17's pads), so the resistors give way. What matters -
    # the filter on the same side of the package as the analog pins it
    # filters - is unaffected. ---
    "U5": dict(lib="Sensor_Temperature", sym="MAX31856",
               fp="Package_SO:TSSOP-14_4.4x5mm_P0.65mm",
               fpf="TSSOP-14_4.4x5mm_P0.65mm.kicad_mod",
               value="MAX31856MUD+", at=(97.0, TC2_Y, TC2_ROT),
               pins={"1": "GND", "2": "TC2_N", "3": "TC2_N_F",
                     "4": "TC2_P_F", "5": "+3V3", "6": None, "7": None,
                     "8": "+3V3", "9": "TC2_CS", "10": "SPI_SCLK",
                     "11": "SPI_MISO", "12": "SPI_MOSI", "13": None,
                     "14": "GND"}),
    "C18": dict(lib="Device", sym="C", fp=C0603[0], fpf=C0603[1],
                value="100nF", at=(90.0, TC2_Y - 2.8 * TC2_DY, 0),
                pins={"1": "+3V3", "2": "GND"}),
    "C19": dict(lib="Device", sym="C", fp=C0603[0], fpf=C0603[1],
                value="100nF", at=(90.0, TC2_Y + 2.7 * TC2_DY, 0),
                pins={"1": "+3V3", "2": "GND"}),
    "R16": dict(lib="Device", sym="R", fp=R0603[0], fpf=R0603[1],
                value="100R 1%", at=(105.9, TC2_Y + 5.4, 180),
                pins={"1": "TC2_P", "2": "TC2_P_F"}),
    "R17": dict(lib="Device", sym="R", fp=R0603[0], fpf=R0603[1],
                value="100R 1%", at=(102.2, TC2_Y + 5.4, 180),
                pins={"1": "TC2_N", "2": "TC2_N_F"}),
    "C20": dict(lib="Device", sym="C", fp=C0603[0], fpf=C0603[1],
                value="100nF", at=(102.2, TC2_Y + 0.6, 180),
                pins={"1": "TC2_P_F", "2": "TC2_N_F"}),
    "C21": dict(lib="Device", sym="C", fp=C0603[0], fpf=C0603[1],
                value="10nF", at=(105.9, TC2_Y + 0.6, 0),
                pins={"1": "TC2_P_F", "2": "GND"}),
    "C22": dict(lib="Device", sym="C", fp=C0603[0], fpf=C0603[1],
                value="10nF", at=(103.0, TC2_Y + 4.2 * TC2_DY, 0),
                pins={"1": "TC2_N_F", "2": "GND"}),
    "J8": dict(lib="Connector", sym="Screw_Terminal_01x02",
               fp=TBLOCK[0], fpf=TBLOCK[1], value="TC2_K",
               at=(114.0, TC2_Y + 3.2, 90),
               pins={"1": "TC2_P", "2": "TC2_N"}),
    # --- SSR output: two opto-driven 24 V channels -------------------------
    # REV B.2. The terminals were "+5 V, watchdog-gated, switched low side"
    # with the GPIO on the channel MOSFET's gate through 100R. They are now
    # "24 V, always live, switched low side", the gate is driven through an
    # optocoupler, and the watchdog sits in the shared return instead of the
    # supply. Three separate decisions, so three separate derivations.
    #
    # --- WHY 24 V ---------------------------------------------------------
    # The board's input became 24 V when U11 arrived, so a 5 V control output
    # on a 24 V board was the last place the old input voltage survived. An
    # SSR-40DA-class input takes 3-32 V, so both work; 24 V is chosen for the
    # noise margin on a loom that runs beside element wiring, and because it
    # is what every other DC control terminal in a kiln cabinet already is.
    #
    # The high side is VIN_P - post-F1, post-D8, post-Q8 - not VIN. That is
    # the whole point of picking a node: a terminal fed from raw VIN bypasses
    # the reverse-polarity switch and the fuse, and a screw terminal is
    # exactly where a wiring mistake lands. This used to cost ~0.4 V, the
    # drop of the SS34 that Q8 replaced; it now costs ~33 mV, so the terminal
    # really is at the input voltage and the 3-32 V SSR window is entered
    # with the whole of it.
    #
    # CURRENT BUDGET, and it is a real limit rather than a note. F1 holds at
    # 750 mA and U11 draws ~250 mA of it, so the two channels share ~400 mA
    # before the fuse starts to think about it. Two SSR inputs (~15 mA each)
    # and two indicators (~5 mA each) is 40 mA, a 10x margin. A small DC
    # contactor coil per channel fits; two large ones do not. D9/D10 are
    # sized to that budget and no further - see them.
    #
    # --- WHY THE OPTOCOUPLERS ARE BACK, AND WHAT THEY ARE FOR --------------
    # Rev B opto-isolated both channels (U8/U9 + SJ3/SJ4) and then REVERTED
    # it, because an optocoupler only isolates if the SSR control loop is
    # powered from a supply that is not this board, and this board powers it.
    # THAT REASONING IS STILL CORRECT AND IS NOT BEING OVERTURNED. These
    # terminals are still board-powered, the two sides still share GND, and
    # nothing here is an isolation barrier. There is no pour keepout, no
    # router keepout, no rule area and no check_isolation.py, and none of
    # those should come back - re-read the revert commit (93a31d7) before
    # adding one.
    #
    # What changed is the failure the parts are bought for. At 5 V, a channel
    # MOSFET failing gate-to-drain put 5 V through 100R into a GPIO, which
    # the ESP32's clamp survives. At 24 V the same single failure puts 240 mA
    # into that clamp and takes the module with it. The opto removes the
    # path: the only thing the MCU touches is an LED, so no single failure in
    # the 24 V domain has a conductor to the GPIO at all. That is
    # CONTAINMENT, not isolation, and the distinction is the reason the
    # keepouts stay gone.
    #
    # It is also not more parts than the alternative. A zener from gate to
    # GND contains the same fault for the same one part per channel, and it
    # contains it by conducting - a part that has to survive the fault to
    # work, and that fails open silently. The opto contains it by not being
    # a conductor. Same count, stronger mechanism.
    #
    # Per channel: SSRn_CTRL -> 220R -> U8 LED -> GND.
    #
    # 220R is sized against the ESP32's GUARANTEED V_OH, 0.8*VDD = 2.64 V,
    # not against 3.3 V, and that is the whole reason it is not 330R: the
    # CTR bin is only specified at I_F = 5 mA and CTR falls off steeply
    # below it, and 330R at the guaranteed corner gives 4.7 mA - under the
    # floor, on the datasheet figure this board is supposed to use.
    #   I_F = (V_OH - V_F)/220: 9.5 mA at 3.3 V / 1.2 V, 6.5 mA at the
    #   guaranteed 2.64 V, and 5.6 mA at 2.64 V with V_F at its 1.4 V max
    #   (TLP291 datasheet: 1.1/1.25/1.4 V at I_F = 10 mA, so the max at
    #   ~6 mA is lower still - 5.6 mA is the pessimistic bound).
    # Worst case is still over the floor, and the 9.5 mA best case is half
    # the ESP32's 20 mA recommended source current and a fifth of the LED's
    # 50 mA rating.
    #
    # The GB rank (datasheet p.2: CTR 100-400% at I_F = 5 mA, V_CE = 5 V -
    # 100-400, not the 100-600 the LCSC listing claims) then gives
    # I_C >= 5.6 mA (the worst-case I_F at CTR 100%) against the 1.0 mA the
    # gate node needs through R7's 4.7k: 5.6x. That margin is also the aging
    # budget - an LED driven this far inside its rating loses CTR slowly.
    #
    # THE COLLECTOR SITS ON SSR_EN, A 5 V RAIL, AND THAT IS LOAD-BEARING.
    # An emitter follower into R7 saturates, so the gate lands at
    # 5 V - V_CE(sat) ~= 4.7 V - a voltage set by the RAIL, not by CTR.
    # (V_CE(sat) 0.3 V max at I_C = 2.4 mA / I_F = 8 mA; we ask for 1.0 mA
    # at ~7 mA, so 0.3 V is the pessimistic end.) That clears the CJ2310's
    # 4.5 V R_DS(on) spec point,
    # which is the whole reason this number has to come from a rail and not
    # from a ratio. Put the collector on 24 V instead and the gate goes to
    # ~24 V, over the MOSFET's +-20 V V_GS, and a zener is needed to get back
    # to where the 5 V rail already was for free.
    #
    # R7/R20 (4.7k) still hold the gate down, but against a different thing:
    # the opto's dark current, not a high-impedance GPIO. The datasheet
    # bounds I_CEO at 0.08 uA max at 25 C and 50 uA max at 85 C (both at
    # V_CE = 48 V; this collector sees 5 V). Interpolated, that is ~1 uA at
    # 50 C - but AT 85 C the bound is 50 uA, and across the 10k these were
    # until review A5 (2026-09-29) that is 0.5 V: the CJ2310's V_GS(th)
    # floor, with no margin left. (An earlier note here said "~10 uA hot,
    # 5x"; that was the 25 C I_C(off) spec, not a hot one.) 4.7k, an existing
    # BOM line, puts the 85 C corner at 0.24 V, 2x under the floor, and still
    # asks only 1 mA of the >= 5.6 mA the opto can pass. Going lower buys
    # little: 2.2k would need 2.1 mA, and the CTR margin is also the aging
    # budget above. The GPIO can
    # no longer reach the gate at all, which is strictly better than what
    # they used to guard.
    #
    # --- WHY THE WATCHDOG MOVED TO THE RETURN ------------------------------
    # The watchdog must still be able to open a channel whose MOSFET has
    # failed SHORT - that is the case a firmware-owned interlock cannot cover
    # and the reason it is in the load path rather than the control path.
    # Keeping it on the high side at 24 V would need a 60 V P-channel switch
    # (the only fee-free one at JLCPCB is a 50 V/130 mA part that would cap
    # the terminals below their own current budget) plus a resistive divider
    # to keep its V_GS inside +-20 V off a rail that reaches 37 V when D8
    # clamps a sustained fault - which puts the board's most safety-critical
    # node on a divider referenced to the fault.
    #
    # Q7 in the shared return does the same job with the same part as the
    # channels, and leaves the ENTIRE watchdog - U10, Q3, Q4, R47, SJ2 - in
    # the 5 V domain, unchanged, with its fail-safe argument intact word for
    # word. SSR_EN keeps its name and its meaning (the watchdog's permission
    # to heat); it now carries gate drive instead of load current.
    #
    # THIS IS NOT THE "STACKED LOW SIDE" (topology A) THE WATCHDOG BLOCK
    # BELOW REJECTS. That proposal made Q3 - whose gate the old charge pump
    # could only lift to 2.16 V, below the 2.5 V where the AO3400A
    # guarantees any R_DS(on) - the series element, so its drop was unbounded
    # and subtracted from the channel's V_GS. Q7 is a dedicated switch with
    # its gate on SSR_EN at ~5 V, where the CJ2310 is specified at 125 mOhm:
    # 5 mV at 40 mA, 50 mV at the 400 mA budget. The objection was about an
    # unbounded drop, and this one is bounded by a datasheet line.
    #
    # Two independent things collapse when the window expires, which is a
    # gain over the single high-side switch: SSR_EN falls, so the optos lose
    # their collector rail AND Q7 loses its gate. Either alone opens both
    # channels.
    #
    # R18 is why that works at all. SSR_EN is Q4's DRAIN, so with Q4 off
    # nothing defines it - and Q7's gate hangs on it. This is exactly the
    # bug R49 was added to fix on Q3's gate ("a floating gate is not off"),
    # one node downstream, and it fails in the same dangerous direction.
    # 10k rather than R49's 100k because this node gates the heat directly
    # and 0.5 mA is not worth saving.
    #
    # R22 defines SSR_RTN for the mirror-image reason. With Q7 off and both
    # channels off, SSR_RTN is an island between three drain-source
    # leakages and would charge toward 24 V - putting -24 V across Q5/Q6's
    # gates, outside the +-20 V rating, with everything nominally OFF.
    #
    # 100k, not 10k, and the difference is the fault this whole arrangement
    # exists for. With Q5 FAILED SHORT and the window expired, the only
    # thing between 24 V and the SSR is R22 in series with the SSR's own
    # input (~1.2k): 10k passes 2.1 mA, and an SSR-40DA-class input can
    # trigger from about 2 mA. That is a watchdog that does not quite work
    # in the one case it is in the load path for. 100k passes 237 uA, an
    # order of magnitude under any trigger.
    #
    # It is still stiff enough for the job it was added for: 3 x 1 uA of
    # I_DSS (CJ2310 datasheet, at 60 V) across 100k is 0.3 V, so Q5/Q6 see
    # -0.3 V V_GS rather than -24 V. The third state - watchdog tripped,
    # firmware still calling for heat - is simply the first one again:
    # SSR_EN is down, so the opto has no collector rail and Q5's gate sits
    # at R7's 0 V whatever the GPIO does. (An earlier note here had Q5
    # running as a source follower in that state; it cannot, because its
    # gate drive and Q7's come off the same rail.)
    #
    # What R22 does NOT cover is the fault it was sized for. With Q5 failed
    # short and the window expired, SSR_RTN is pulled up through the SSR's
    # own input to 24 x 100k/101.2k = 23.7 V, and the HEALTHY channel's
    # MOSFET then sees V_GS = -23.7 V against the CJ2310's +-20 V. It is a
    # second-order stress after a first fault, and the watchdog still holds
    # the SSR off while it lasts - but it is outside a rating. 2026-09-29
    # review, rev-C item C2.
    #
    # --- PARTS -------------------------------------------------------------
    # CJ2310 replaces the AO3400A on every switch that now stands off 24 V
    # (Q5, Q6, Q7): 60 V against the 37 V D8 clamps a sustained fault to, and
    # 125 mOhm specified AT 4.5 V, which is the gate voltage these actually
    # get. The AO3400A is a 30 V part and would be inside its rating in
    # normal operation and outside it during the one event the TVS exists
    # for. It is one of this rev's two new feeders (+$3 each); the TLP291
    # optos are the other - Extended, not Basic (see U8).
    "Q5": dict(lib="Transistor_FET", sym="2N7002", fp=SOT23[0], fpf=SOT23[1],
               value="CJ2310", at=(36.3, 76.46, 0),
               pins={"1": "SSR1_GATE", "2": "SSR_RTN", "3": "SSR1_OUT"}),
    # SOP-4, not the SMDIP-4 this started as, and the reason is geometry
    # rather than electricals. The SMD-DIP4 body is 12.04 mm wide over its
    # courtyard; the corridor between J4/J9 and the rest of the block is
    # ~5.5 mm and has to carry BOTH these parts and the four per-terminal
    # legends (`24V`/`OUT` at each screw's y, which silk.py may slide in x
    # but not in y). A 12 mm opto leaves the legends nowhere to go and they
    # print on the terminal body - three check_silk failures, and no amount
    # of re-spacing fixes it because the corridor is simply too narrow.
    # 8.50 x 3.10 mm opens it to ~6.7 mm and everything else falls out.
    # Costs one Extended feeder; the LTV-817S was Basic.
    "U8": dict(lib="Isolator", sym="TLP291",
               fp="Package_SO:SOP-4_4.4x2.6mm_P1.27mm",
               fpf="SOP-4_4.4x2.6mm_P1.27mm.kicad_mod",
               value="TLP291", at=(45.0, 77.5, 0),
               pins={"1": "SSR1_LED_A", "2": "GND",
                     "3": "SSR1_GATE", "4": "SSR_EN"}),
    "R6": dict(lib="Device", sym="R", fp=R0603[0], fpf=R0603[1],
               value="220R", at=(51.5, 80.5, 180),
               pins={"1": "SSR1_CTRL", "2": "SSR1_LED_A"}),
    "R7": dict(lib="Device", sym="R", fp=R0603[0], fpf=R0603[1],
               value="4.7k", at=(55.5, 80.5, 0),
               pins={"1": "SSR1_GATE", "2": "GND"}),
    # Freewheel across the terminal pair, cathode on the supply. An SSR input
    # is resistive and needs none; a DC contactor coil - the load 24 V is
    # worth having for - needs one or it puts its collapse across Q5. Sized
    # to the F1 budget above and not beyond it: the 1N4148W's 450 mA
    # repetitive peak covers a coil interrupted at the ~200 mA per channel
    # that budget allows, and it is already on the BOM (D3/D4).
    "D9": dict(lib="Device", sym="D", fp="Diode_SMD:D_SOD-123",
               fpf="D_SOD-123.kicad_mod", value="1N4148W", at=(36.3, 71.33, 90),
               pins={"1": "VIN_P", "2": "SSR1_OUT"}),
    # The channel's readout row: the indicator resistor, the LED and the
    # control test point on one y, with channel 2's row the same three parts
    # 8 mm south on the same three x. See SSR_IND_Y / SSR_TP_X.
    #
    # 10k, not the 680R this was at 5 V nor the 4.7k it was at first on 24 V:
    # (24 - 2.0)/10k = 2.2 mA and 48 mW. At 4.7k the resistor burned 103 mW,
    # 82% of an 0805's 125 mW, and 127 mW - over rating - at the HDR-15-24's
    # +10% trim (26.4 V); at 10k that corner is 60 mW. An indicator LED is
    # plainly visible at 2 mA. Review A3, 2026-09-29. The pair
    # still sits across the TERMINAL, so it reads the channel's actual
    # output state - lit only when Q5 AND Q7 are both conducting, which is
    # firmware asking and the watchdog agreeing.
    "LED3": dict(lib="Device", sym="LED", fp=LED0603[0], fpf=LED0603[1],
                 value="amber", at=(SSR_IND_X, SSR1_IND_Y, 0),
                 pins={"1": "SSR1_IND_K", "2": "VIN_P"}),
    "R10": dict(lib="Device", sym="R", fp=R0603[0], fpf=R0603[1],
                value="10k", at=(52.0, SSR1_IND_Y, 0),
                pins={"1": "SSR1_OUT", "2": "SSR1_IND_K"}),
    "J4": dict(lib="Connector", sym="Screw_Terminal_01x02",
               fp=TBLOCK[0], fpf=TBLOCK[1], value="SSR1", at=(26.0, 75.5, 270),
               pins={"1": "VIN_P", "2": "SSR1_OUT"}),
    # --- SSR channel 2: exact copy of channel 1, ~12mm south ---------------
    "Q6": dict(lib="Transistor_FET", sym="2N7002", fp=SOT23[0], fpf=SOT23[1],
               value="CJ2310", at=(36.3, 91.2, 0),
               pins={"1": "SSR2_GATE", "2": "SSR_RTN", "3": "SSR2_OUT"}),
    "U9": dict(lib="Isolator", sym="TLP291",
               fp="Package_SO:SOP-4_4.4x2.6mm_P1.27mm",
               fpf="SOP-4_4.4x2.6mm_P1.27mm.kicad_mod",
               value="TLP291", at=(45.0, 90.5, 0),
               pins={"1": "SSR2_LED_A", "2": "GND",
                     "3": "SSR2_GATE", "4": "SSR_EN"}),
    "R19": dict(lib="Device", sym="R", fp=R0603[0], fpf=R0603[1],
                value="220R", at=(52.0, 92.5, 180),
                pins={"1": "SSR2_CTRL", "2": "SSR2_LED_A"}),
    "R20": dict(lib="Device", sym="R", fp=R0603[0], fpf=R0603[1],
                value="4.7k", at=(57.0, 92.5, 0),
                pins={"1": "SSR2_GATE", "2": "GND"}),
    "D10": dict(lib="Device", sym="D", fp="Diode_SMD:D_SOD-123",
                fpf="D_SOD-123.kicad_mod", value="1N4148W", at=(36.3, 86.07, 90),
                pins={"1": "VIN_P", "2": "SSR2_OUT"}),
    "LED4": dict(lib="Device", sym="LED", fp=LED0603[0], fpf=LED0603[1],
                 value="amber", at=(SSR_IND_X, SSR2_IND_Y, 0),
                 pins={"1": "SSR2_IND_K", "2": "VIN_P"}),
    "R21": dict(lib="Device", sym="R", fp=R0603[0], fpf=R0603[1],
                value="10k", at=(52.0, SSR2_IND_Y, 0),
                pins={"1": "SSR2_OUT", "2": "SSR2_IND_K"}),
    "J9": dict(lib="Connector", sym="Screw_Terminal_01x02",
               fp=TBLOCK[0], fpf=TBLOCK[1], value="SSR2", at=(26.0, 88.0, 270),
               pins={"1": "VIN_P", "2": "SSR2_OUT"}),
    # --- Shared switched return, and the two nodes that must not float -----
    # Q7 carries both channels. Its drain stands off 24 V whenever a channel
    # is commanded on and the window has expired, so it is the same 60 V
    # CJ2310 rather than a second part number.
    "Q7": dict(lib="Transistor_FET", sym="2N7002", fp=SOT23[0], fpf=SOT23[1],
               value="CJ2310", at=(36.3, 80.94, 0),
               pins={"1": "SSR_EN", "2": "GND", "3": "SSR_RTN"}),
    "R18": dict(lib="Device", sym="R", fp=R0603[0], fpf=R0603[1],
                value="10k", at=(45.5, 86.3, 0),
                pins={"1": "SSR_EN", "2": "GND"}),
    # Placed north of D9 rather than in the channel-2 column with the parts
    # it serves, and that is a SILK constraint, not an electrical one. A
    # pulldown does not care about a 9 mm stub, and the column between Q7 and
    # the display-damping row is the overflow area the silk placer was using
    # for R54/R56's reference designators - those two are boxed between the
    # R55/R58 row and J5 and have nowhere else to go. Four parts in that
    # column cost two silk_overlap violations against a budget of zero; three
    # parts and one fewer designator clears it.
    "R22": dict(lib="Device", sym="R", fp=R0603[0], fpf=R0603[1],
                value="100k", at=(36.3, 66.95, 0),
                pins={"1": "SSR_RTN", "2": "GND"}),
    # --- Hardware watchdog (Task 12) ---------------------------------------
    # WDT_KICK (U1.29, a firmware square wave) retriggers U10, a one-shot
    # whose Q output keeps Q3 enhanced, Q3 holds SSR_PG (the gate of the
    # high-side switch Q4) down, and Q4 supplies SSR_EN - the +5V rail that
    # feeds both opto collectors (U8/U9) and Q7's gate. Stop
    # kicking and the window (1.65-2.71s worst case, R46*C38, see
    # arithmetic below) expires, Q falls, R47 pulls SSR_PG to +5V, Q4 turns
    # off, R18 pulls SSR_EN down, and both channels open - the optos lose
    # their collector rail and Q7 loses its gate, either of which is
    # sufficient. This is the only interlock on this board that survives
    # firmware death - lid/over-temp/stale-TC are firmware-owned and die
    # with it. It is still only SUPPLEMENTARY: the real protection is a
    # mechanical over-temperature cutout in series with the element
    # contactor.
    #
    # THE RETRIGGER IS EDGE-DRIVEN - that is the entire point. Firmware
    # wedged with WDT_KICK stuck high must fail exactly like firmware that
    # stopped toggling, and a monostable retriggered on B's RISING edge does
    # precisely that: a DC level delivers no edge, the window expires, Q falls.
    #
    # Gates ONLY the heat outputs (SSR_EN). AUX1-3 (vent/purge/spare, via
    # U6/ULN2003) and the buzzer are on separate nets entirely - untouched by
    # Q3/Q4 - so a stalled controller can still open its vent.
    #
    # --- WHY NOT THE DIODE CHARGE PUMP THIS REPLACES ----------------------
    # Rev B shipped a BAT54S clamp-and-peak-detector (C38 100nF, C39 1uF,
    # R46 1M) into Q3's gate, and it does not work. Solving its steady state
    # exactly - V_hold(min) = d*a*A/(1-b*d), a = C38/(C38+C39), d = e^(-T/tau),
    # A = V_OH - 2*Vf - gives, at the 5 Hz kick the firmware plan called for,
    # 0.63V against the AO3400A's Vgs(th) max of 1.45V. The rail never comes
    # up. It is not a corner case either: the typical corner (V_OH 3.3V,
    # Vf 0.2V) reaches 0.84V, below even the TYPICAL 1.0V threshold.
    #
    # The sizing note this replaces computed the DECAY constant (R46*C39 = 1s)
    # and the gate margin but never the REPLENISHMENT constant
    # (R46*C38 = 0.1s), and flagged its own values as an unverified assumption
    # because "no target kick frequency or hold-decay spec exists yet".
    #
    # Raising the kick rate rescues the gate voltage (>= 250 Hz) but cannot
    # rescue the temperature behaviour. Schottky reverse leakage through the
    # BAT54S's second diode (nothing to do with the board's old D2, which was
    # the USB ORing part U12 replaced) discharges the hold node in parallel
    # with R46 and roughly doubles per
    # 10 C, so the budget for a transient firmware stall - a flash erase
    # stalls BOTH cores - falls from 0.31s at 25C to 0.11s at 60C, and near
    # 85C the pump stops holding at all. A kiln controller sits next to a
    # 5 kW heat source. No choice of passives fixes that, because the leak is
    # in the timing path; the fix is to take it out of the timing path.
    #
    # --- THE ONE-SHOT ----------------------------------------------------
    # U10 (SN74LVC1G123, LCSC C26159250) is a single retriggerable monostable.
    # WDT_KICK drives B (rising-edge trigger) with A tied low and CLR high;
    # every edge restarts the window, and Q stays HIGH for as long as edges
    # keep arriving. Q drives Q3's gate directly. Q3, Q4, R47 and the SJ2
    # defeat jumper are unchanged - only what holds Q3's gate up has changed.
    #
    # Window: tw ~= K*R*C with K = 1.0-1.1, the datasheet's own spec'd bound
    # at its 10k x 0.1uF anchor, and the same limits at 125C as at 85C.
    # R46 100k 1% and C38 22uF 25V 1206, with 10% purchase tolerance and a
    # 15% bias/temp derating allowance, give a worst-case window of
    # 1.65-2.71s. Firmware kicks at 5 Hz (a rising edge every 200 ms), so the
    # margin is 8.3x at the minimum window. A wedged controller loses the rail
    # within 2.71s - 0.22 C of overshoot on a 60 kJ/K kiln at 5 kW, against a
    # runaway timescale of ~16 minutes.
    #
    # Both values are already on this BOM (R46 -> C149504, C38 -> C12891), so
    # neither adds a feeder. U10 does: it is Extended and not Preferred, +$3.
    # Note the BAT54S it replaces was Extended-but-PREFERRED, i.e. fee-free -
    # removing it saves nothing. See gen_jlc.LCSC's note on that distinction.
    #
    # Leakage now lives where it is specified: the Rext/Cext I/O leakage is
    # +-0.25uA against a 33uA charge current, 0.8%, over the full -40..125C
    # range. That is the whole reason this is an IC and not an RC.
    #
    # Q3's gate drive becomes Q's VOH, ~3.2V, which finally clears the 2.5V
    # point where the AO3400A guarantees ANY Rds(on) - the corner the pump
    # block flagged and could not reach.
    #
    # Fail-safe polarity is unchanged and now has three independent reasons to
    # hold: no edges -> window expires -> Q low; R48 pulls B low whenever the
    # MCU drives nothing, so a floating CMOS input cannot self-trigger the
    # one-shot during boot ROM, flashing or reset; and with U10 unpowered
    # entirely, Q3's gate simply floats, which R47 already answers.
    # Then Q3 off -> R47 pulls SSR_PG to +5V -> Q4 off -> rail dead.
    #
    # R49 pulls WDT_OK down. The earlier note here claimed no pulldown was
    # needed because "with U10 unpowered Q3's gate simply floats, which R47
    # already answers" - that is wrong, and wrong in the fail-DANGEROUS
    # direction. R47 holds SSR_PG, not Q3's gate, and it only wins while Q3
    # is off. A floating gate is not off: the AO3400A's Vgs(th) floor is
    # ~0.65V, so any leakage or coupling that lifts WDT_OK above it turns Q3
    # ON, which pulls SSR_PG down through a few tens of milliohms against
    # R47's 100k, which turns Q4 ON and makes the SSR rail LIVE with no
    # firmware and no watchdog. The case is real rather than theoretical:
    # +3V3 is U2's output and +5V is not, so any +3V3 failure (LDO dead,
    # rail shorted, U2 in thermal shutdown) unpowers U10 while leaving the
    # SSR rail's supply intact. 100k against Q's push-pull VOH costs 32uA
    # and defines the node whenever U10 does not.
    "R49": dict(lib="Device", sym="R", fp=R0603[0], fpf=R0603[1],
                value="100k", at=(58.0, 45.8, 0),
                pins={"1": "WDT_OK", "2": "GND"}),
    "U10": dict(lib="74xGxx", sym="74LVC1G123", fp=SSOP8[0], fpf=SSOP8[1],
                value="SN74LVC1G123", at=(53.5, 49.7, 0),
                pins={"1": "GND", "2": "WDT_KICK", "3": "+3V3", "4": "GND",
                      "5": "WDT_OK", "6": "WDT_CT_N", "7": "WDT_CT_P",
                      "8": "+3V3"}),
    # Rotated 90 deg, and its pins swapped to match: U10's pins 6 and 7 are
    # 0.5 mm apart on the same edge, so with the cap lying horizontal one of
    # the two timing nets had to cross the other's pad and the router could
    # not seat it. Perpendicular, pin 6 (CT_N) fans south to pad 1 and pin 7
    # (CT_P) fans north to pad 2, and the two runs diverge instead of meeting.
    "C38": dict(lib="Device", sym="C", fp=C1206[0], fpf=C1206[1],
                value="22uF", at=(58.0, 50.3, 90),
                pins={"1": "WDT_CT_N", "2": "WDT_CT_P"}),
    "R46": dict(lib="Device", sym="R", fp=R0603[0], fpf=R0603[1],
                value="100k", at=(58.0, 54.1, 0),
                # Rail on pin 1, not pin 2: KiCad's R symbol runs its pins
                # vertically, and a rail hanging off the BOTTOM pin is
                # power_path()'s "exactly wrong" case - the port comes back up
                # past the pin and its bar lands on the part's own fields. The
                # PCB does not care which pad is which here; C38 is due north.
                pins={"1": "+3V3", "2": "WDT_CT_P"}),
    "C39": dict(lib="Device", sym="C", fp=C0603[0], fpf=C0603[1],
                value="100nF", at=(53.5, 53.5, 0),
                pins={"1": "+3V3", "2": "GND"}),
    # Holds B low whenever the MCU drives nothing - boot ROM, flashing, reset,
    # or a dead module. No edges means the one-shot expires, which is the
    # power-on state the rail must have.
    "R48": dict(lib="Device", sym="R", fp=R0603[0], fpf=R0603[1],
                value="100k", at=(48.5, 52.5, 0),
                pins={"1": "WDT_KICK", "2": "GND"}),
    "Q3": dict(lib="Transistor_FET", sym="AO3400A", fp=SOT23[0], fpf=SOT23[1],
               value="AO3400A", at=(52.0, 57.5, 0),
               pins={"1": "WDT_OK", "2": "GND", "3": "SSR_PG"}),
    # High-side switch for the SSR gate-drive rail. AO3401A (P-channel,
    # SOT-23, LCSC C15127, JLCPCB Basic): source on +5V, gate on SSR_PG,
    # drain IS SSR_EN. It carries gate drive only - ~1.5 mA into two opto
    # collectors, Q7's gate and R18 - which is why a 30 V part is still the
    # right one here while Q5/Q6/Q7 had to move to 60 V.
    # Pin order from KiCad's own Transistor_FET:AO3401A symbol
    # (extends TP0610T): 1 G, 2 S, 3 D.
    "Q4": dict(lib="Transistor_FET", sym="AO3401A", fp=SOT23[0], fpf=SOT23[1],
               value="AO3401A", at=(40.8, 84.0, 0),
               pins={"1": "SSR_PG", "2": "+5V", "3": "SSR_EN"}),
    # Q4's gate pull-up: the fail-safe. Nothing holding SSR_PG down means
    # SSR_PG = +5V means Q4 off means no gate-drive rail. 100k keeps Q3's load at
    # 50 uA (see the arithmetic above) while staying stiff enough that Q4's
    # own gate leakage moves the node by only ~10 mV.
    "R47": dict(lib="Device", sym="R", fp=R0603[0], fpf=R0603[1],
                value="100k", at=(45.5, 84.0, 0),
                pins={"1": "+5V", "2": "SSR_PG"}),
    # Bring-up defeat: shorts SSR_PG straight to GND (through Q3's own
    # source net), holding Q4 on and bypassing the watchdog gate entirely so
    # the SSRs work before the firmware kick task exists. Silkscreened
    # "WDT DEFEAT" - see gen_pcb.py SILK. MUST be removed (left open) in
    # service - this is a foot-gun by design, not a normal-operation jumper.
    "SJ2": dict(lib="Jumper", sym="SolderJumper_2_Open",
                fp="Jumper:SolderJumper-2_P1.3mm_Open_RoundedPad1.0x1.5mm",
                fpf="SolderJumper-2_P1.3mm_Open_RoundedPad1.0x1.5mm.kicad_mod",
                value="WDT_DEFEAT", at=(57.0, 57.5, 0),
                pins={"1": "SSR_PG", "2": "GND"}),
    # --- Aux output bank (vent / purge / spare) --------------------------
    # ULN2003A: 7 Darlington channels with integrated freewheel diodes to COM,
    # and a JLCPCB *Basic* part - so it replaces ~19 discrete parts at zero
    # feeder fee. Pin order (SOIC-16, confirmed against KiCad 10's own
    # Transistor_Array:ULN2003A symbol): I1..I7 = 1..7, GND = 8, COM = 9,
    # O7..O1 = 10..16 (note O1 is pin 16, so the outputs run backwards).
    #
    # COM goes to AUX_VP, its own screw terminal, NOT the board's +5V: a gas
    # purge solenoid is realistically 12V or 24V DC and the ULN is rated 50V /
    # 500mA per channel. A solder link (SJ1) ties AUX_VP to +5V for plain 5V
    # relays. The buzzer deliberately keeps its discrete driver (Q2/D4/R8/R11)
    # so a 5V buzzer and a 24V solenoid never share a COM rail.
    #
    # R23-R25 hold the inputs low while the ESP32 pins are high-impedance at
    # boot - a floating Darlington input must not energize a solenoid. Per
    # REV-B-NOTES.md SS6, 10k is sufficient: worst case (ignoring the ULN's
    # own nominal-only internal pulldowns) V_in(max) = 50nA x 10k = 0.5mV,
    # ~1000x margin under any threshold that would turn a channel on, and
    # GPIO 14/15/16 carry no pull-up at reset.
    #
    # Designators: the task brief called these R20-R22, but Task 7 (SSR
    # optocoupler channels) already consumed R20-R22 - verified against the
    # live COMPONENTS dict before adding these. Using R23-R25 instead.
    "U6": dict(lib="Transistor_Array", sym="ULN2003A",
               fp="Package_SO:SOIC-16_3.9x9.9mm_P1.27mm",
               fpf="SOIC-16_3.9x9.9mm_P1.27mm.kicad_mod",
               value="ULN2003A", at=(39.0, 55.0, 180),
               pins={"1": "AUX1", "2": "AUX2", "3": "AUX3",
                     "4": None, "5": None, "6": None, "7": None,
                     "8": "GND", "9": "AUX_VP",
                     "10": None, "11": None, "12": None, "13": None,
                     "14": "AUX3_OUT", "15": "AUX2_OUT", "16": "AUX1_OUT"}),
    "R23": dict(lib="Device", sym="R", fp=R0603[0], fpf=R0603[1],
                value="10k", at=(46.0, 61.2, 0),
                pins={"1": "AUX1", "2": "GND"}),
    "R24": dict(lib="Device", sym="R", fp=R0603[0], fpf=R0603[1],
                value="10k", at=(46.0, 58.0, 0),
                pins={"1": "AUX2", "2": "GND"}),
    "R25": dict(lib="Device", sym="R", fp=R0603[0], fpf=R0603[1],
                value="10k", at=(46.0, 54.5, 0),
                pins={"1": "AUX3", "2": "GND"}),
    # 4-position terminal: coil rail + three switched low sides.
    "J10": dict(lib="Connector", sym="Screw_Terminal_01x04",
                fp="TerminalBlock_Phoenix:TerminalBlock_Phoenix_MKDS-1,5-4-5.08_1x04_P5.08mm_Horizontal",
                fpf="TerminalBlock_Phoenix_MKDS-1,5-4-5.08_1x04_P5.08mm_Horizontal.kicad_mod",
                value="AUX", at=(26.0, 52.0, 270),
                pins={"1": "AUX_VP", "2": "AUX1_OUT",
                      "3": "AUX2_OUT", "4": "AUX3_OUT"}),
    # Solder link: AUX_VP <- +5V for 5V relay coils. Open by default.
    "SJ1": dict(lib="Jumper", sym="SolderJumper_2_Open",
                fp="Jumper:SolderJumper-2_P1.3mm_Open_RoundedPad1.0x1.5mm",
                fpf="SolderJumper-2_P1.3mm_Open_RoundedPad1.0x1.5mm.kicad_mod",
                value="AUX_VP=5V", at=(46.0, 49.5, 0),
                pins={"1": "+5V", "2": "AUX_VP"}),
    # --- Buzzer ----------------------------------------------------------
    "BZ1": dict(lib="Device", sym="Buzzer",
                fp="Buzzer_Beeper:Buzzer_12x9.5RM7.6",
                fpf="Buzzer_12x9.5RM7.6.kicad_mod",
                value="active 5V", at=(41.0, 68.95, 0),
                pins={"1": "+5V", "2": "BUZZ_K"}),
    "D4": dict(lib="Device", sym="D", fp="Diode_SMD:D_SOD-123",
               fpf="D_SOD-123.kicad_mod", value="1N4148W", at=(65.0, 66.0, 0),
               pins={"1": "+5V", "2": "BUZZ_K"}),
    "Q2": dict(lib="Transistor_FET", sym="AO3400A", fp=SOT23[0], fpf=SOT23[1],
               value="AO3400A", at=(65.0, 70.0, 0),
               pins={"1": "BUZZ_GATE", "2": "GND", "3": "BUZZ_K"}),
    "R11": dict(lib="Device", sym="R", fp=R0603[0], fpf=R0603[1],
                value="100R", at=(65.0, 74.0, 0),
                pins={"1": "ALARM", "2": "BUZZ_GATE"}),
    "R8": dict(lib="Device", sym="R", fp=R0603[0], fpf=R0603[1],
               value="10k", at=(65.0, 78.0, 0),
               pins={"1": "BUZZ_GATE", "2": "GND"}),
    # --- WS2812B status LED ---------------------------------------------
    # R3 / LED1 / C10 west to east with D3 below, in the quietest part-free
    # window this board has: 0.26 mm/mm2 of track and zero vias, against
    # 0.53 mm/mm2 and eight vias where the cluster used to sit. Measured, and
    # measuring it correctly is the whole story of where this went.
    #
    # It moved out of the strip above J7 because a 5 x 5 mm PLCC4 is wider
    # than three pin pitches and was sitting squarely on the label band for
    # J7's pins 5, 6 and 7: `SDA` and `3V3` were pushed 2.60 mm onto the
    # connector body and `SCL` onto LED1's own outline, so the row printed as
    # `3V3 GND TX RX . . . GND` and counting from either end gave the wrong
    # pin - on the one header carrying I2C and a 3.3 V rail. No silk placer
    # can fix that (analysis/silkscreen-review.md §B); the part had to move.
    #
    # Two candidate homes measured as EMPTY and were not, and both cost a
    # full re-route to find out:
    #
    #   the band south of the module (x 60..88, y 44..56) is U1's escape.
    #   Forty castellated pads fan through it to the test-point row at y 57.
    #   SPI_MOSI and SPI_SCLK could not reach TP4/TP5 and TC1_CS finished
    #   unrouted.
    #
    #   the lane at the middle of the board (x 67..80, y 63..95) is the
    #   nameplate's, and it is also the I2C corridor from the test-point row
    #   down to the pull-ups and J7 - 220 mm of track through it. I2C_SDA and
    #   I2C_SCL could not reach the ADE7953.
    #
    # The reason both looked free is a measurement bug worth not repeating:
    # the density probe counted a track only if an ENDPOINT fell inside the
    # window, so a corridor - which by definition is traces passing straight
    # through - read as zero. Worse, it was run against the board from the
    # failed build, where the very nets in question were missing. Measure
    # against a FULLY ROUTED board, and clip each segment to the window
    # (Liang-Barsky) rather than testing its endpoints.
    #
    # It was at (92.25, 97.45) until this revision, in the 5 mm strip above
    # J7 - which is J7's PIN-NAME strip. A 5 x 5 mm PLCC4 is wider than three
    # pin pitches, so LED1 and its 330R covered the label band for pins 5, 6
    # and 7 outright: `SDA` and `3V3` were pushed 2.60 mm onto the connector
    # body and `SCL` onto LED1's own outline, and the row printed as
    # `3V3 GND TX RX . . . GND` - a 10 mm hole, so counting from either end
    # gives the wrong pin on the one header carrying I2C and a 3.3 V rail.
    # No silk placer can fix that; the part had to move. See
    # analysis/silkscreen-review.md §B.
    #
    # So it lands one lane west and one band north of where it was: x 66..82,
    # y 85..95, which is toward the centre of the board (the old spot was
    # 22 mm east and 27 mm south of it), in front of the panel rather than
    # behind a connector housing, and clear of every pin-name band. The
    # 800 kHz single-wire protocol does not care about the run from IO48.
    "LED1": dict(lib="LED", sym="WS2812B",
                 fp="LED_SMD:LED_WS2812B_PLCC4_5.0x5.0mm_P3.2mm",
                 fpf="LED_WS2812B_PLCC4_5.0x5.0mm_P3.2mm.kicad_mod",
                 value="WS2812B", at=(74.0, 88.0, 0),
                 pins={"1": "VLED", "2": None, "3": "GND", "4": "WS_DIN"}),
    "R3": dict(lib="Device", sym="R", fp=R0603[0], fpf=R0603[1],
               value="330R", at=(68.0, 88.0, 0),
               pins={"1": "LED_DATA", "2": "WS_DIN"}),
    # Silicon, not the SS14 Schottky this was, and the buck is the reason.
    # VLED = +5V - Vf, and the WS2812B needs 0.7*VLED to stay under the 3.3V
    # the ESP32 drives. On the old unregulated rail an SS14's ~0.3 V left
    # VLED at 4.3 V (VIH 3.01 V) only because the input sagged; on a regulated
    # 5.0 V rail the same diode gives VLED 4.7 V and VIH 3.29 V - a 10 mV
    # margin, i.e. none. A 1N4148W drops 0.65-0.85 V across the WS2812B's
    # 5-60 mA range, putting VLED at ~4.15 V and VIH at ~2.9 V, comfortably
    # under 3.3 V and still well above the part's 3.5 V VDD minimum.
    #
    # What regulating removed is the TRADE, not the drop. The review's
    # "trimming the PSU up to help the SSR/relay drops hurts the LED" is gone
    # - VLED no longer moves with the installer's trim pot - so a fixed drop
    # is now a real fix rather than a hedge, and the 74AHCT1G125 the review
    # offered as the alternative is not needed.
    "D3": dict(lib="Device", sym="D", fp="Diode_SMD:D_SOD-123",
               fpf="D_SOD-123.kicad_mod",
               value="1N4148W", at=(74.0, 93.0, 0),
               pins={"1": "VLED", "2": "+5V"}),
    "C10": dict(lib="Device", sym="C", fp=C0603[0], fpf=C0603[1],
                value="100nF", at=(80.0, 88.0, 0),
                pins={"1": "VLED", "2": "GND"}),
    # --- Protected dry-contact inputs (lid / gas flow / spare) -----------
    # Generalises rev A's single lid-switch filter (below) to three
    # identical channels, all on J11, plus one SRV05-4 TVS array covering
    # them. 1k series, 10k pull-up to +3V3, 100nF to GND per channel. Open
    # contact reads HIGH = "open/inactive", so a broken wire, a pulled
    # connector or a failed-open switch all read "open" and fail safe.
    # IN1 = lid (IO4), IN2 = gas-flow interlock (IO2), IN3 = spare (IO1) -
    # see docs/pin-assignments.md. Wire a dry contact between each channel
    # and J11.4 (GND).
    #
    # R13 replaces the ESP32's weak ~45k internal pull-up with a stiff 10k,
    # so an open switch holds the node high against far more leakage and
    # capacitive pickup. R12 limits fault/ESD current into the pin, and C12
    # sees R12||R13 (~0.9k) with the switch closed - a ~1.8 kHz corner
    # (~90us), rising to ~160 Hz (10k x 100nF) with it open. Fast enough to
    # leave mechanical bounce to the firmware, which samples at 500 ms;
    # slow enough to swallow EMI transients. Closed-switch level is
    # 3.3V x 1k/11k = 0.30V, well under the ESP32's 0.25 x VDD (0.83V) V_IL.
    #
    # Rev A skipped a TVS (a unique Extended part / $3 feeder fee for one
    # input); rev B's externally-exposed net count goes from two to ~ten,
    # so one SRV05-4 array (D5) now covers all three raw inputs upstream of
    # the series resistors. NOT extended to the thermocouple inputs
    # (TC1_P/N, TC2_P/N, Task 6) - array leakage into a ~40 uV/C source is
    # an accuracy error, not protection.
    #
    # Designator note: the brief that originated this block called for
    # R23-R26; R23-R25 were already consumed by Task 8's ULN2003 pulldowns
    # by the time this landed, so the second and third channels use the
    # next free run, R26-R29, instead. Re-verify against the live
    # COMPONENTS dict before reusing numbers near here - a duplicate key
    # silently overwrites the earlier component.
    #
    # Placement: R12/R13/C12 (channel 1, née rev A's lid filter) keep their
    # original spot in the free band between LED1 and J7. Channels 2 and 3
    # extend the same schematic row/PCB band eastward; D5 and J11 sit just
    # past them. See gen_sch.py SCH_AT for the >=20mm spacing rule that
    # keeps facing pin-label stubs from merging nets (Tasks 7, 8).
    "R12": dict(lib="Device", sym="R", fp=R0603[0], fpf=R0603[1],
                value="1k", at=(35.0, 111.0, 180),
                pins={"1": "IN1_RAW", "2": "IN1"}),
    "R13": dict(lib="Device", sym="R", fp=R0603[0], fpf=R0603[1],
                value="10k", at=(40.0, 111.0, 0),
                pins={"1": "+3V3", "2": "IN1"}),
    "C12": dict(lib="Device", sym="C", fp=C0603[0], fpf=C0603[1],
                value="100nF", at=(45.0, 111.0, 0),
                pins={"1": "IN1", "2": "GND"}),
    "R26": dict(lib="Device", sym="R", fp=R0603[0], fpf=R0603[1],
                value="1k", at=(50.0, 111.0, 180),
                pins={"1": "IN2_RAW", "2": "IN2"}),
    "R27": dict(lib="Device", sym="R", fp=R0603[0], fpf=R0603[1],
                value="10k", at=(55.0, 111.0, 0),
                pins={"1": "+3V3", "2": "IN2"}),
    # Channel 2's filter cap, in channel 2's row. It used to sit at
    # (35.0, 115.0) - 20 mm west of its own R26/R27, on the far side of
    # channel 3 - which is what made IN2 the longest signal net on the board
    # (158.6 mm routed, 108.3 mm ideal) and hung a westward spur across
    # channel 3's row. x 58.9 is the only slot that exists for it: R27's
    # courtyard ends at 56.7 and J11's begins at 61.0, so the 0805 lands with
    # ~0.5 mm either side. It takes IN2's ideal from 108.3 mm to ~94 mm and
    # makes the three dry-contact channels three clean rows.
    "C23": dict(lib="Device", sym="C", fp=C0603[0], fpf=C0603[1],
                value="100nF", at=(58.9, 111.0, 0),
                pins={"1": "IN2", "2": "GND"}),
    "R28": dict(lib="Device", sym="R", fp=R0603[0], fpf=R0603[1],
                value="1k", at=(40.0, 115.0, 180),
                pins={"1": "IN3_RAW", "2": "IN3"}),
    "R29": dict(lib="Device", sym="R", fp=R0603[0], fpf=R0603[1],
                value="10k", at=(45.0, 115.0, 0),
                pins={"1": "+3V3", "2": "IN3"}),
    "C24": dict(lib="Device", sym="C", fp=C0603[0], fpf=C0603[1],
                value="100nF", at=(50.0, 115.0, 0),
                pins={"1": "IN3", "2": "GND"}),
    # SRV05-4: 1 IO1, 2 VN(GND), 3 IO2, 4 IO3, 5 VP(+3V3), 6 IO4 (spare).
    "D5": dict(lib="Power_Protection", sym="SRV05-4",
               fp="Package_TO_SOT_SMD:SOT-23-6", fpf="SOT-23-6.kicad_mod",
               value="SRV05-4", at=(56.0, 115.0, 0),
               pins={"1": "IN1_RAW", "2": "GND", "3": "IN2_RAW",
                     "4": "IN3_RAW", "5": "+3V3", "6": None}),
    "J11": dict(lib="Connector", sym="Screw_Terminal_01x04",
                fp="TerminalBlock_Phoenix:TerminalBlock_Phoenix_MKDS-1,5-4-5.08_1x04_P5.08mm_Horizontal",
                fpf="TerminalBlock_Phoenix_MKDS-1,5-4-5.08_1x04_P5.08mm_Horizontal.kicad_mod",
                value="INPUTS", at=(64.0, 114.0, 0),
                pins={"1": "IN1_RAW", "2": "IN2_RAW",
                      "3": "IN3_RAW", "4": "GND"}),
    # --- CT current sensing (ADE7953, I2C, current-only) -----------------
    # Two current channels, one per SSR zone. I2C rather than SPI: the bus
    # exists for the expansion header anyway (Task 11), so the chip costs
    # zero extra GPIOs.
    #
    # NO MAINS ON THIS BOARD. The voltage channel (VP/VN) is unpopulated and
    # goes to J13, a DNP SELV header, so a future off-board isolated AC
    # accessory upgrades this to true power in firmware alone. IRMS is
    # reported against a configured nominal mains voltage until then
    # (REV-B-NOTES.md SS1: IRMSA/IRMSB are computed entirely within the
    # current signal path and do not depend on VP/VN).
    #
    # Every value below is taken from hardware/kicad/datasheets/REV-B-NOTES.md
    # (ADE7953 Rev. C), which OVERRIDES the task brief's guessed values.
    # Designators were renumbered against the live COMPONENTS dict: the
    # brief's R27-R33/D8 collide with Task 9 (R27/R28/R29) and Task 7 (D5).
    #
    # Interface strapping (REV-B-NOTES.md SS3, correcting the brief):
    #   pins 7/8 PULL_HIGH -> +3V3 direct, no resistor (Table 5: "internal
    #     node pins", not interface-select - the brief's framing was wrong)
    #   pin 14 PULL_LOW -> GND direct, no resistor; routed into the EP land
    #   pin 25 SCLK -> +3V3 via R37 10k pull-up (interface-select: 1 = I2C)
    #   pin 28 ~CS -> +3V3 via R38 10k pull-up (interface-select: 1 = I2C/UART)
    #   pin 27 MOSI/SCL/Rx -> I2C_SCL, pin 26 MISO/SDA/Tx -> I2C_SDA (the
    #     ACTUAL bus signals - the brief had these swapped onto pins 25/28)
    # 10k is Figure 35's Test Circuit value; the datasheet gives no
    # resistor spec for 25/28 (COULD NOT VERIFY #3), only "pulled high".
    # Both pins are static logic inputs nothing else drives, so the value
    # isn't critical - resistors instead of hard ties buy an override path
    # for bring-up or a future SPI experiment for 2 cents.
    #
    # I2C address is fixed at 0x38 (no address pins, REV-B-NOTES.md SS3) -
    # collides with a PCF8574A expander and some touch controllers on the
    # Task 11 expansion header. Nothing else on THIS board's bus conflicts.
    #
    # Pins left unconnected: 1 ZX (voltage zero-cross, meaningless with no
    # voltage channel), 20 ~REVP (needs both channels), 23/24 CF1/CF2
    # (calibration frequency outputs, unused). 21 ZX_I and 22 ~IRQ are also
    # left NC for now - REV-B-NOTES.md SS1/SS3 recommend routing both to a
    # GPIO (ZX_I for the datasheet's recommended synchronous IRMS read;
    # IRQ for the power-up-complete signal) but no GPIO is allocated to
    # this task's scope; a bare test point is a candidate for Task 13.
    #
    # EP (pin 29) is a ground pin, not just a thermal tab (REV-B-NOTES.md
    # SS2, Rev. C p.10/p.68: "Connect the pad to AGND and DGND") - tied GND.
    "U7": dict(lib="Sensor", sym="ADE7953xCP",
               fp="Package_DFN_QFN:QFN-28-1EP_5x5mm_P0.5mm_EP3.1x3.1mm",
               fpf="QFN-28-1EP_5x5mm_P0.5mm_EP3.1x3.1mm.kicad_mod",
               value="ADE7953ACPZ", at=(95.0, 72.0, 0),
               pins={"1": None, "2": "ADE_RESET", "3": "ADE_VINTD",
                     "4": "GND", "5": "CTA_F", "6": "CTA_FN",
                     "7": "+3V3", "8": "+3V3", "9": "CTB_F", "10": "GND",
                     "11": "ADE_VN", "12": "ADE_VP", "13": "ADE_REF",
                     "14": "GND", "15": "ADE_VINTA", "16": "GND",
                     # 19 CLKOUT is the far side of the on-chip oscillator's
                     # inverter and exists only to hang a crystal off. Y1 is
                     # now a powered oscillator driving CLKIN as a logic input
                     # (datasheet p.9: "An external clock can be provided at
                     # this input"), so nothing drives back into 19 and it is
                     # left open. ADE_CLKOUT is gone with it.
                     "17": "+3V3", "18": "ADE_CLKIN", "19": None,
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
