BenSeverson/bisque/hardware/kicad/generator/gen_jlc.py

"""Generate JLCPCB assembly files (BOM.csv + CPL.csv) from design.py.

Every LCSC part number below was verified live against the LCSC catalog
(package, value and stock) — see VERIFIED_ON. The most recent sweep re-checked
the library tier and the stock of all 39 lines and re-fitted every land pattern
(`lcsc_pads.py --refresh`, then `check_jlc_placement.py`); no `fee_free` flag
had drifted. Re-verify before a production run, since stock and part status
drift.

CPL coordinates follow KiCad's footprint-position convention (Y negated), plus
a per-part correction to both the angle and the origin: JLCPCB places LCSC's
footprint for the part, not ours, and the two libraries do not always agree on
where zero rotation points or where the origin sits. See JLC_PLACEMENT, which
check_jlc_placement.py derives from LCSC's own land patterns and verifies.

Parts in HAND_SOLDER are deliberately left off *both* files and written to
hand-solder-parts.csv instead — see that table for why. JLCPCB's PCBA upload
rejects a CPL carrying designators the BOM doesn't have, so a part must drop
out of both or neither.

Designators in NOT_ASSEMBLED (test points, solder jumpers, the DNP AC-sense
header) are excluded even earlier, before HAND_SOLDER is consulted — they
have no manufactured part at all, so they must not appear in the shopping
list either.
"""
import csv
import re
import math
import os
import sys

sys.path.insert(0, os.path.dirname(__file__))
from design import COMPONENTS

VERIFIED_ON = "2026-09-09"    # C75882, C55144 and C17557 added 2026-09-21

# JLCPCB does not place our footprint. It places LCSC's footprint for that
# part number, anchoring *its* origin at Mid X / Mid Y and turning *its* pin 1
# by Rotation. Two things therefore have to be corrected per part: the angle
# between LCSC's zero-rotation reference and KiCad's, and any offset between
# the two footprints' origins.
#
# Both are measured, not guessed: check_jlc_placement.py fits LCSC's real land
# pattern (generator/lcsc_pads.json, fetched from EasyEDA's component API —
# the library the JLCPCB assembly preview renders) onto the KiCad footprint
# this board uses, and `--derive` prints this table. Every entry below is that
# fit; re-run the checker after changing a part number or a footprint.
#
# This replaced a package-family regex table taken from the community list in
# bennymeg/Fabrication-Toolkit. That list is right about the families it was
# built from and wrong here in two ways that reached the assembly preview:
# `^SOT-23 -> 180` also matches SOT-23-**6**, whose LCSC land is drawn across
# the pins rather than along them (270, not 180), and `^QFN- -> 90` is 180 out
# for the ADE7953's LFCSP-28. A per-part fit cannot make that class of mistake.
#
# dx/dy are millimetres in the CPL's frame (x right, y up), applied after the
# part's own board rotation. They are zero for all but two parts: KiCad anchors
# the ESP32-S3 module and the USB-C receptacle at their body centres, LCSC
# anchors them on the pad pattern.
JLC_PLACEMENT = {
    # U8/U9. LCSC draws the opto's land ACROSS the package where KiCad draws
    # it along - pads at (+-1.27, +-5.0) against our (+-4.765, +-1.27) - so
    # this is a quarter turn, not the identity a 4-pad DIP looks like it
    # should be. Exactly the class of error a package-family table makes.
    "C12891":   (  0,  0.000,  0.000),   # C1    C_1206_3216Metric                    resid 0.118 (2 pin#)
    "C149504":  (  0,  0.000,  0.000),   # R47   R_0805_2012Metric                    resid 0.088 (2 pin#)
    "C15127":   (180,  0.000,  0.000),   # Q4    SOT-23                               resid 0.283 (3 pin#)
    "C15850":   (  0,  0.000,  0.000),   # C7    C_0805_2012Metric                    resid 0.050 (2 pin#)
    "C160404":  (  0,  0.000,  0.000),   # J14   JST_SH_SM04B-SRSS-TB_1x04-1MP_P1.00m resid 0.000 (4 pin#)
    "C165948":  (  0,  0.000,  1.571),   # J1    USB_C_Receptacle_HRO_TYPE-C-31-M-12  resid 0.000 (8 pin#)
    "C1710":    (  0,  0.000,  0.000),   # C16   C_0805_2012Metric                    resid 0.050 (2 pin#)
    "C1739":    (  0,  0.000,  0.000),   # C31   C_0805_2012Metric                    resid 0.050 (2 pin#)
    "C17408":   (  0,  0.000,  0.000),   # R14   R_0805_2012Metric                    resid 0.088 (2 pin#)
    "C17414":   (  0,  0.000,  0.000),   # R1    R_0805_2012Metric                    resid 0.088 (2 pin#)
    "C17621":   (  0,  0.000,  0.000),   # R63   R_0805_2012Metric                    resid 0.088 (2 pin#)
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
